gowenrw/psycho_badge/art/Image2LCD_Settings.png

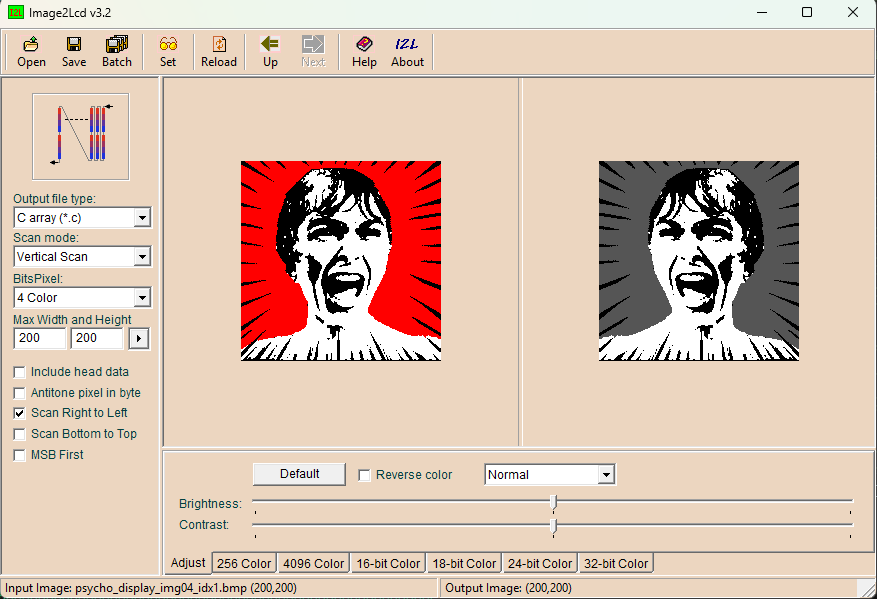
art/Image2LCD_Settings.png
