gowenrw/psycho_badge/art/inspiration/09eceb80-aa4b-47ba-a81a-bc735ab3dbdd.jpg

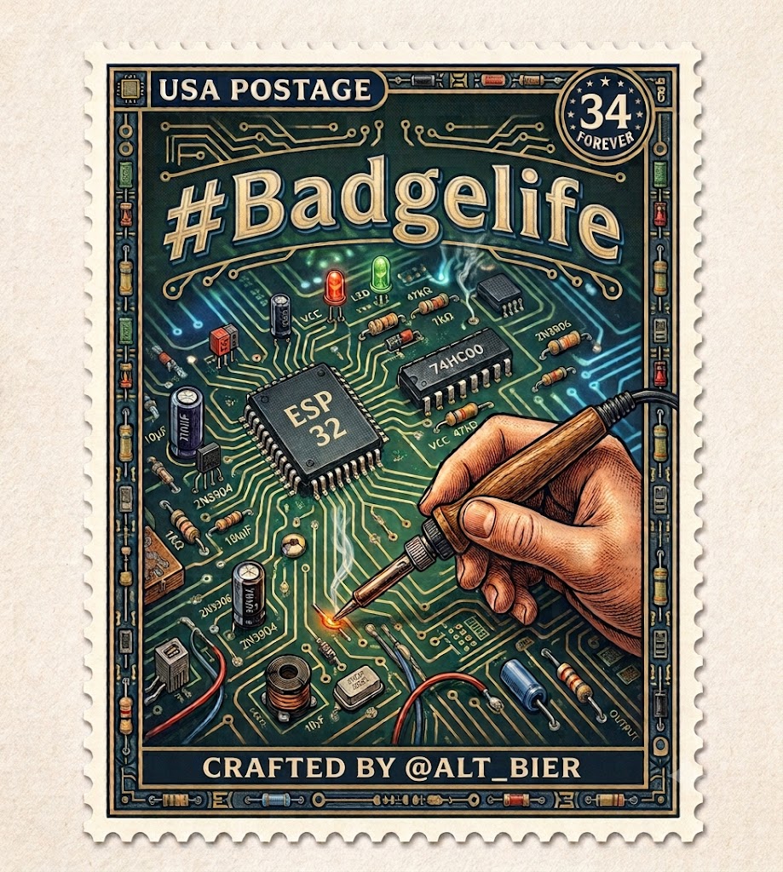
art/inspiration/09eceb80-aa4b-47ba-a81a-bc735ab3dbdd.jpg
