gowenrw/psycho_badge/art/inspiration/51a8uor2yWL._AC_UF894,1000_QL80_.jpg

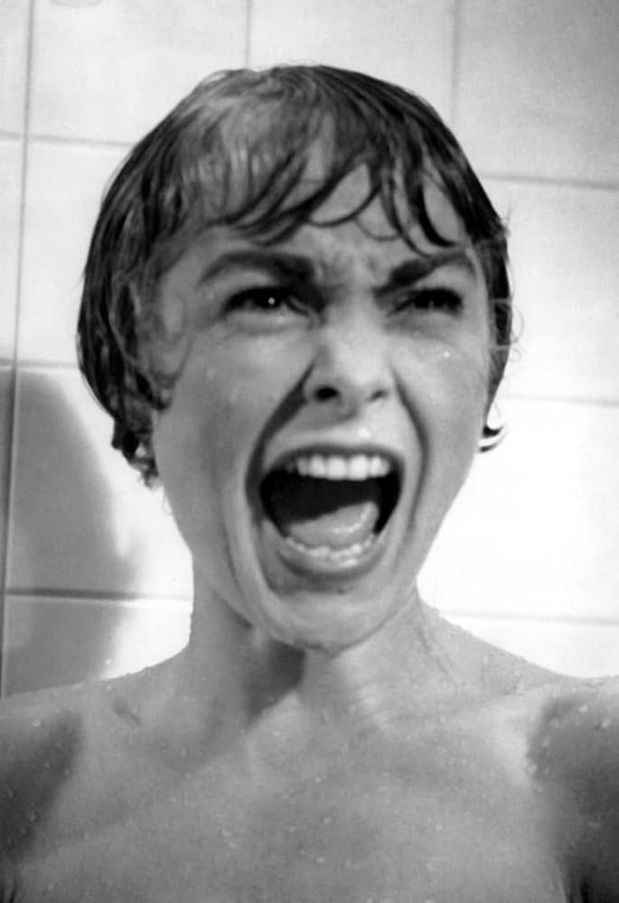
art/inspiration/51a8uor2yWL._AC_UF894,1000_QL80_.jpg
