gowenrw/psycho_badge/art/inspiration/78148790-cfff-4a0e-b91e-01b8ff07a633.jpg

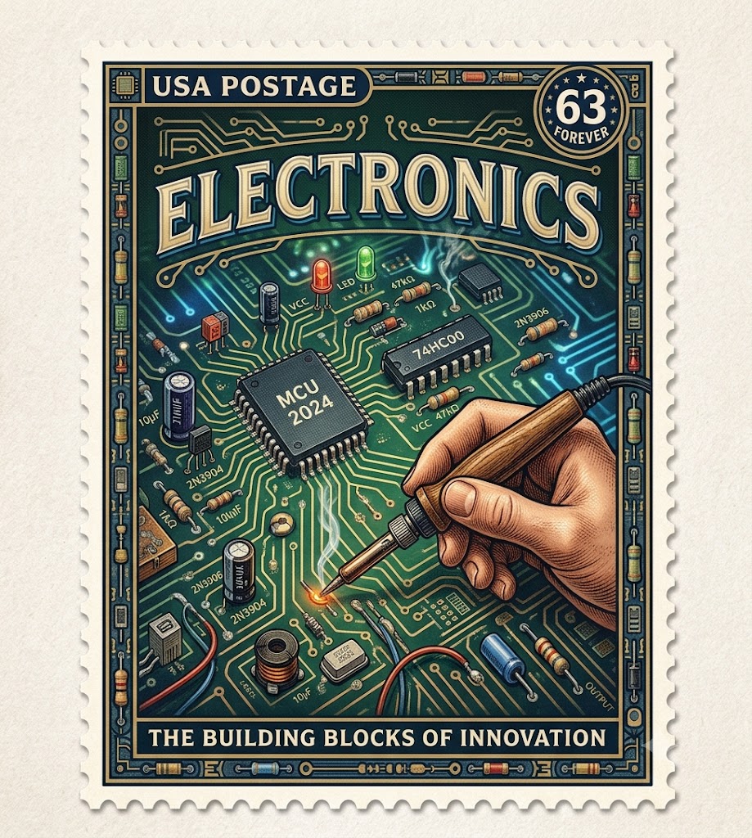
art/inspiration/78148790-cfff-4a0e-b91e-01b8ff07a633.jpg
