gowenrw/psycho_badge/art/inspiration/4122593071_39e41a47dc_c.jpg

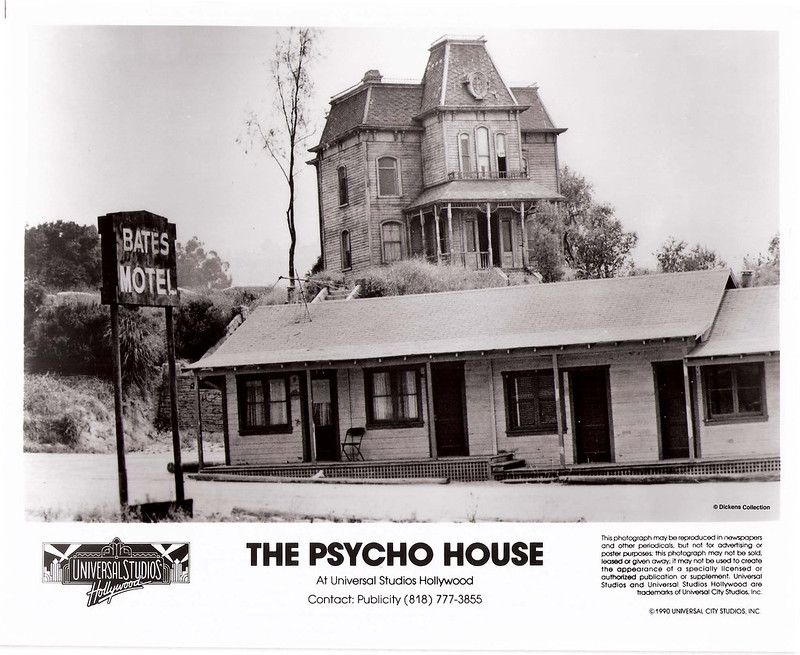
art/inspiration/4122593071_39e41a47dc_c.jpg
