gowenrw/psycho_badge/art/inspiration/5621367626_267cc80568_b.jpg

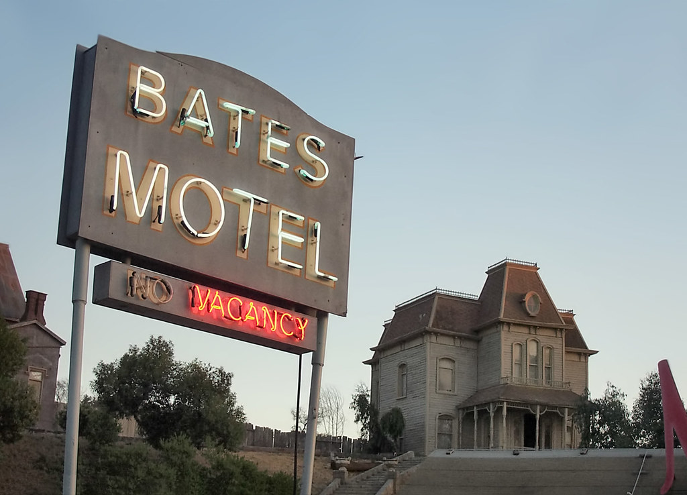
art/inspiration/5621367626_267cc80568_b.jpg
