gowenrw/psycho_badge/art/inspiration/alfred_hitchcock_presents.jpg

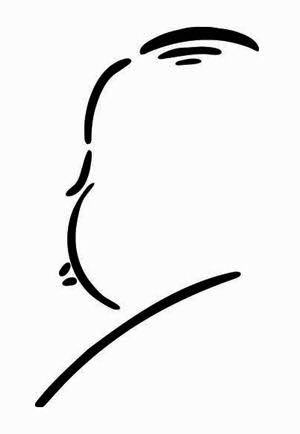
art/inspiration/alfred_hitchcock_presents.jpg
