gowenrw/psycho_badge/art/inspiration/alt_bier_a_small_array_of_antennas_and_satellite_dishes_on_a_ro_00e93679-4413-47bc-a557-2c08350d457e.png

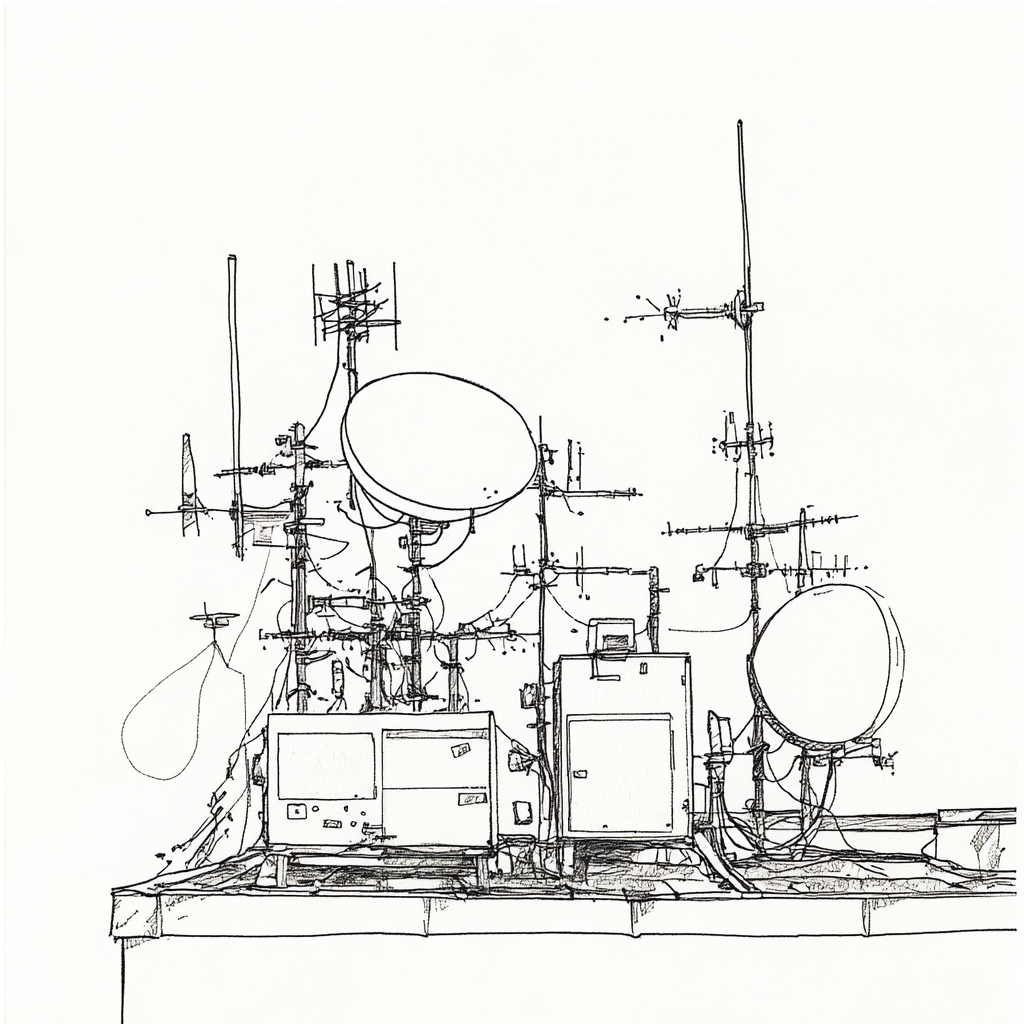
art/inspiration/alt_bier_a_small_array_of_antennas_and_satellite_dishes_on_a_ro_00e93679-4413-47bc-a557-2c08350d457e.png
