gowenrw/psycho_badge/art/inspiration/alt_bier_front_of_a_motel_room_with_a_large_bay_window_and_door_1ff72061-c35d-46a8-9a01-6a3859370cd5.png

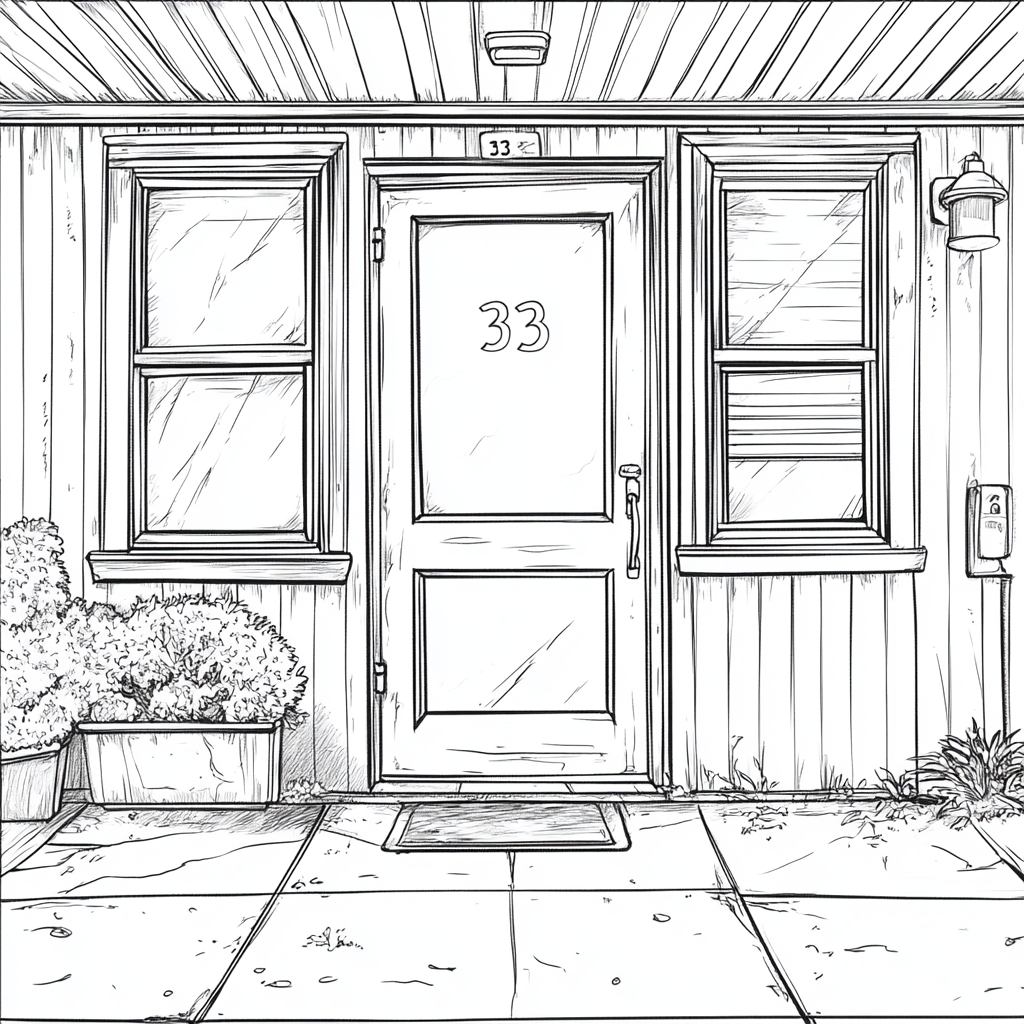
art/inspiration/alt_bier_front_of_a_motel_room_with_a_large_bay_window_and_door_1ff72061-c35d-46a8-9a01-6a3859370cd5.png
