gowenrw/psycho_badge/art/inspiration/alt_bier_front_of_a_motel_room_with_a_large_bay_window_and_door_b3eee03a-e481-4e49-9f6b-45e3d3eed8d4.png

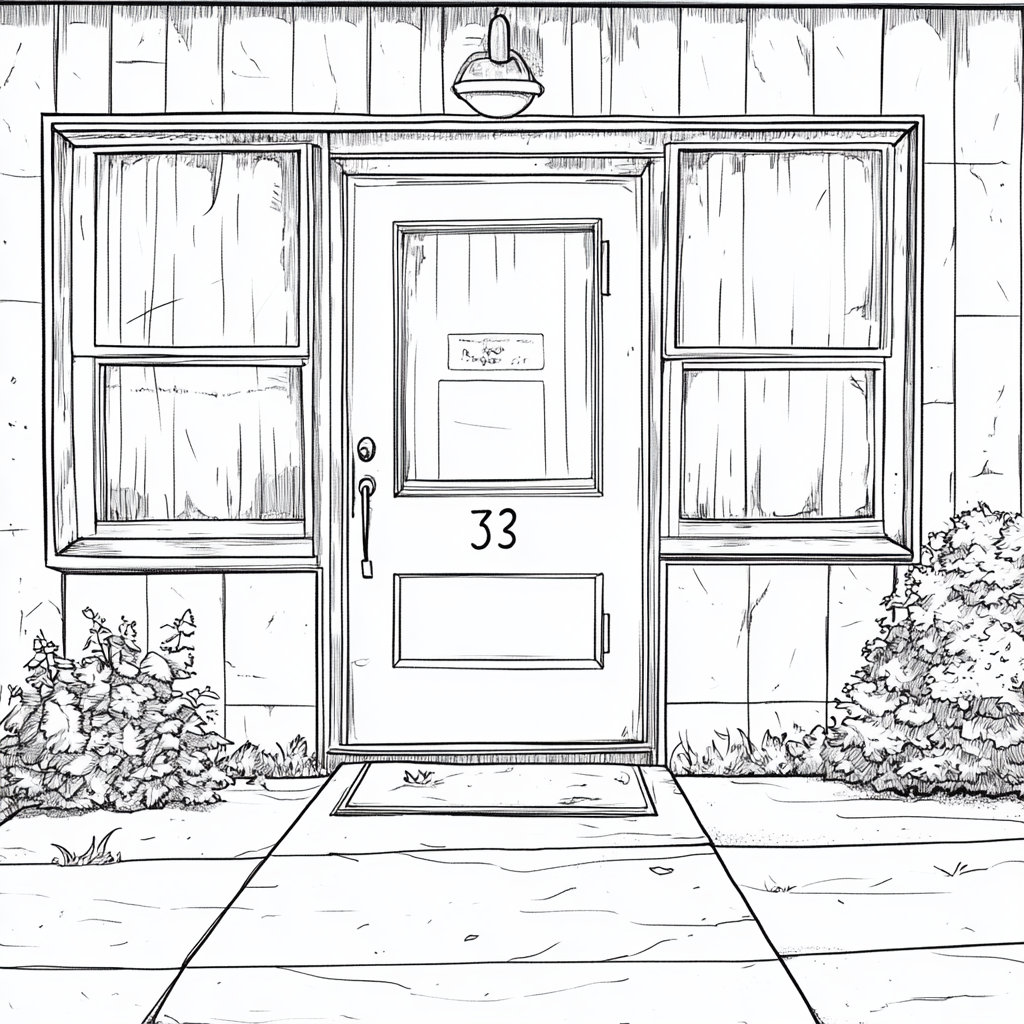
art/inspiration/alt_bier_front_of_a_motel_room_with_a_large_bay_window_and_door_b3eee03a-e481-4e49-9f6b-45e3d3eed8d4.png
