gowenrw/psycho_badge/art/inspiration/alt_bier_image_756xbq756xbq756x.png

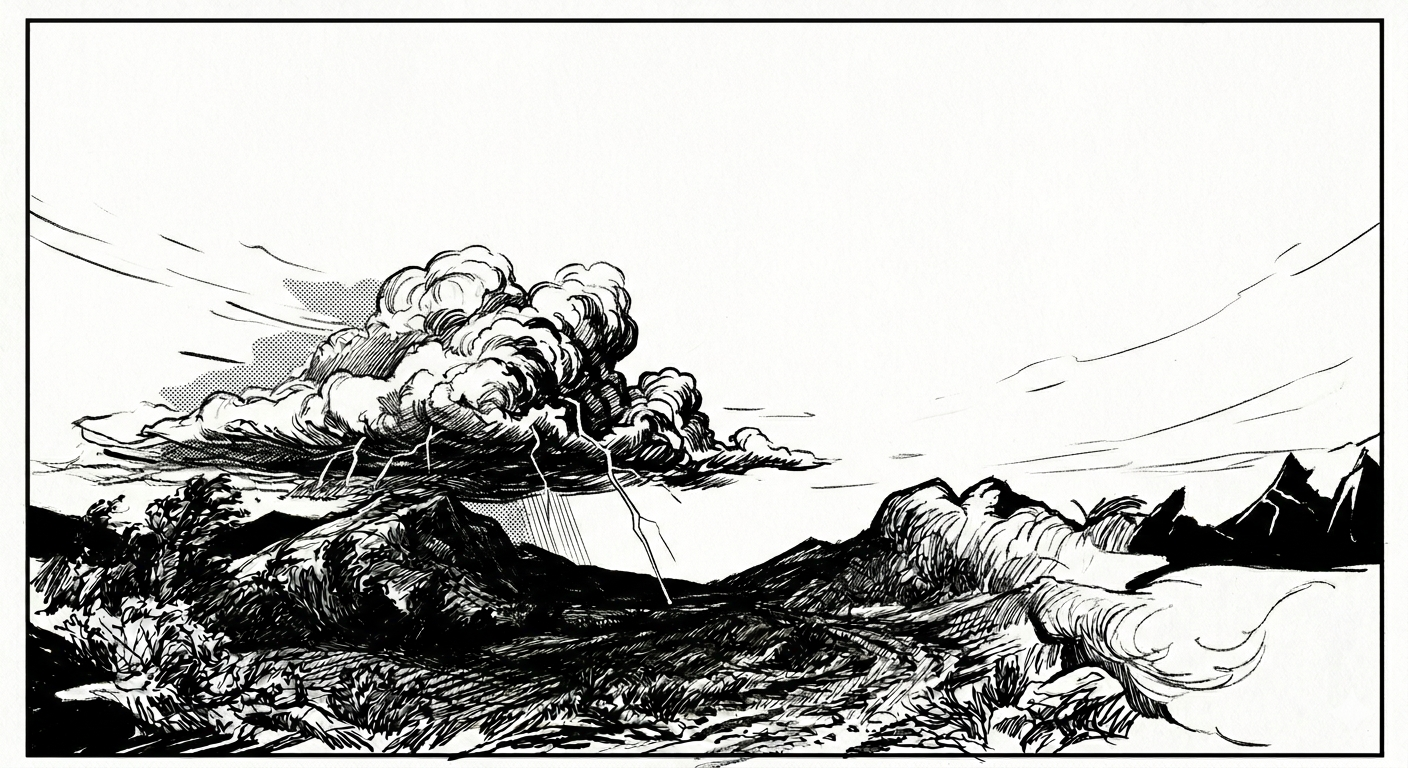
art/inspiration/alt_bier_image_756xbq756xbq756x.png
