gowenrw/psycho_badge/art/inspiration/alt_bier_image_aumj92aumj92aumj.png

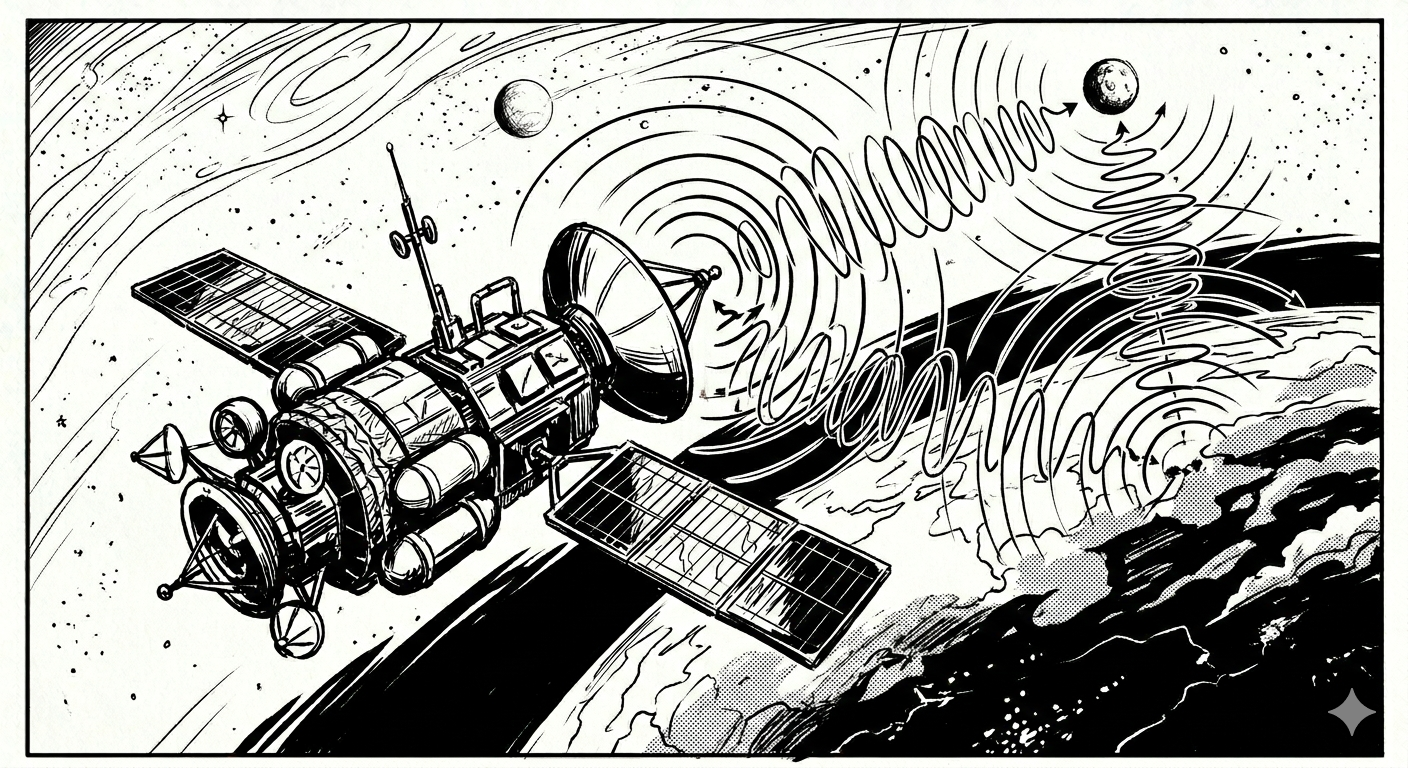
art/inspiration/alt_bier_image_aumj92aumj92aumj.png
