gowenrw/psycho_badge/art/inspiration/alt_bier_image_n5bnvrn5bnvrn5bn.png

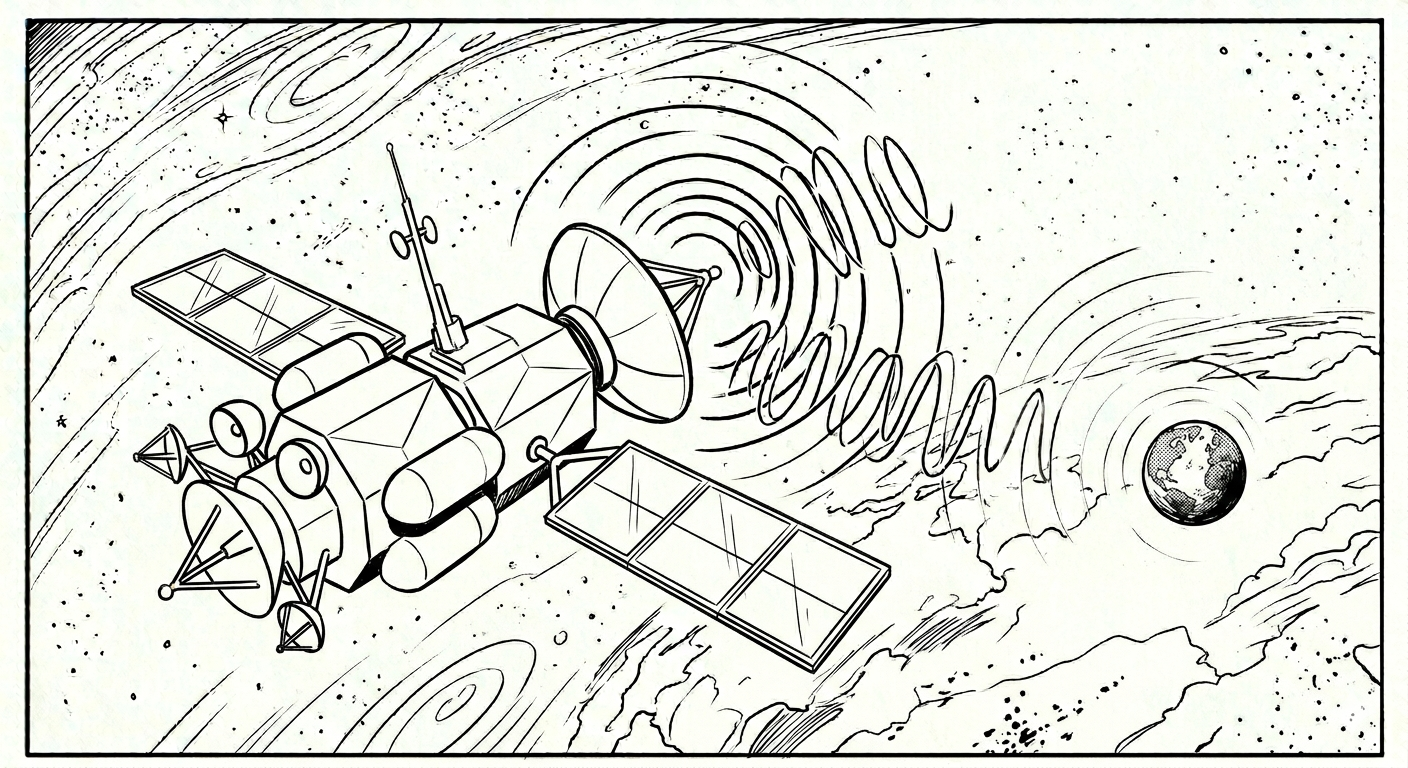
art/inspiration/alt_bier_image_n5bnvrn5bnvrn5bn.png
