gowenrw/psycho_badge/art/inspiration/alt_bier_image_p0ahntp0ahntp0ah.png

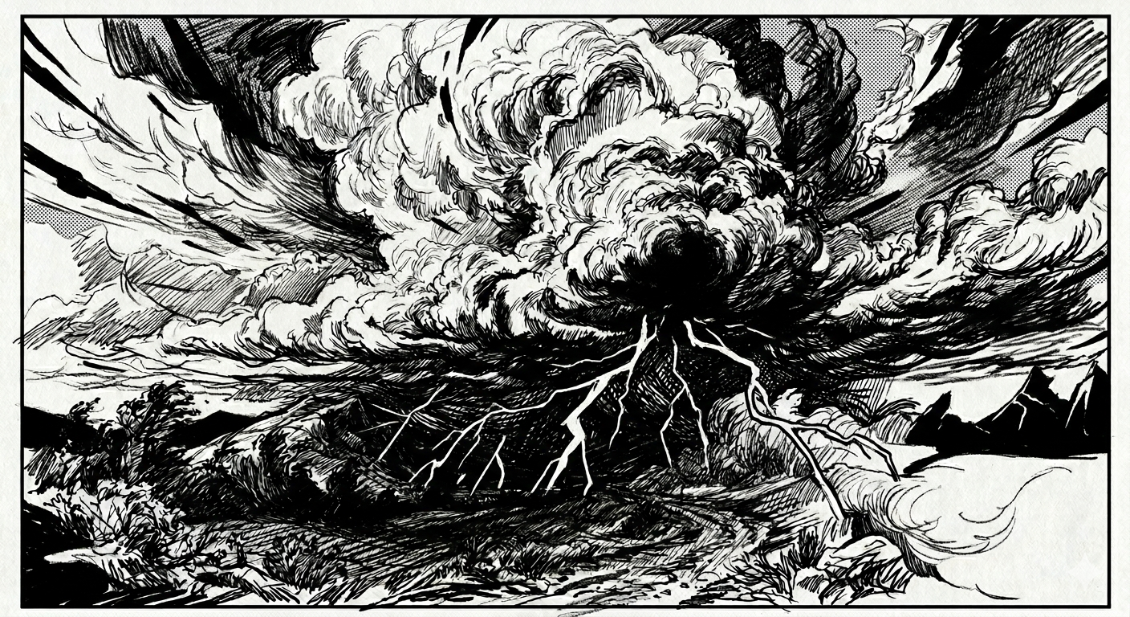
art/inspiration/alt_bier_image_p0ahntp0ahntp0ah.png
