gowenrw/psycho_badge/art/inspiration/alt_bier_image_rigv1rigv1rigv1r.png

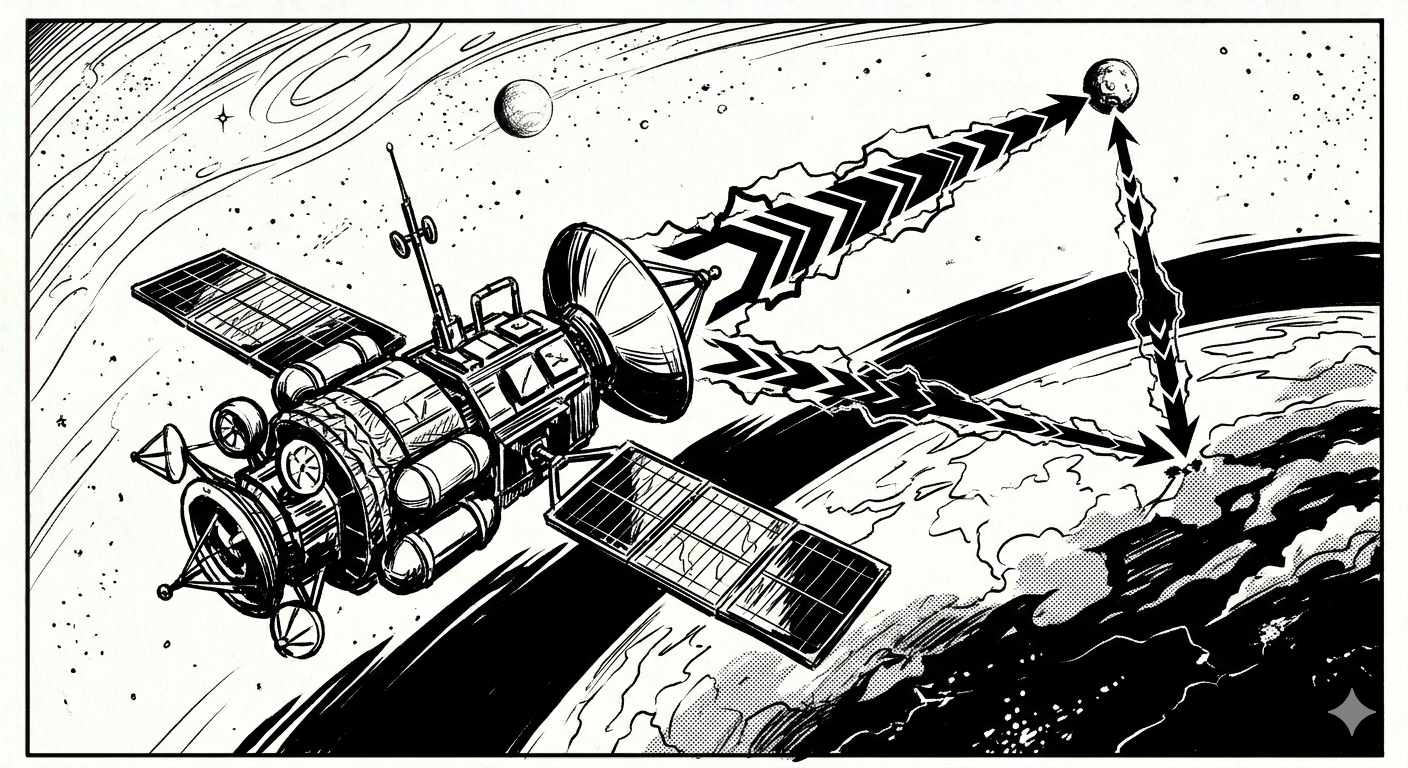
art/inspiration/alt_bier_image_rigv1rigv1rigv1r.png
