gowenrw/psycho_badge/art/inspiration/alt_bier_small_motel_cabin_line_art_in_the_style_of_coloring_bo_fb256de8-bc3b-488d-bda0-6eb76a03a0a5.png

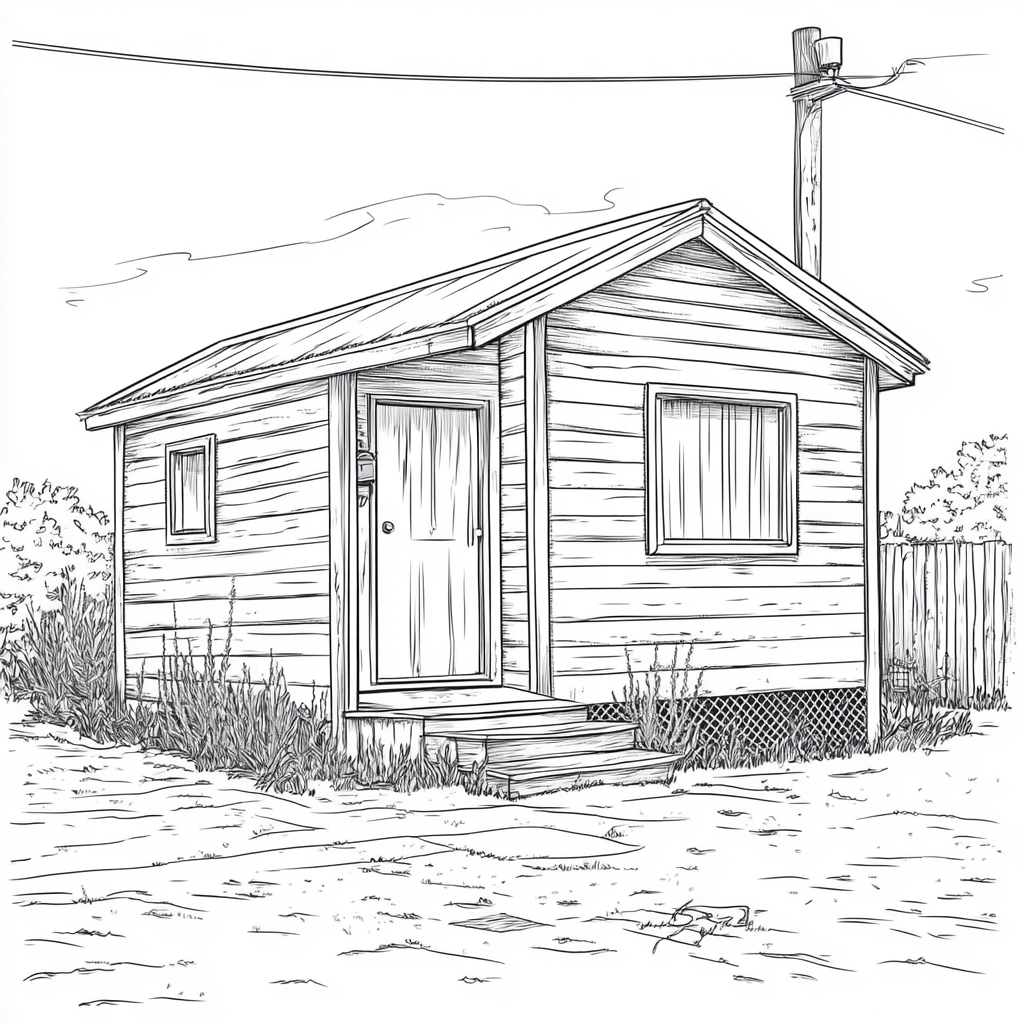
art/inspiration/alt_bier_small_motel_cabin_line_art_in_the_style_of_coloring_bo_fb256de8-bc3b-488d-bda0-6eb76a03a0a5.png
