gowenrw/psycho_badge/art/inspiration/b29aaca8-62c0-4f67-92ab-7d956eef123c.jpg

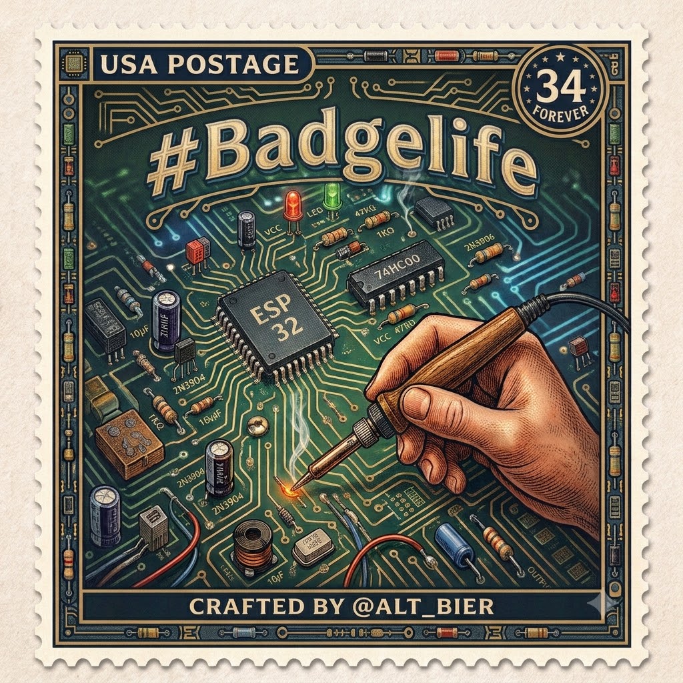
art/inspiration/b29aaca8-62c0-4f67-92ab-7d956eef123c.jpg
