gowenrw/psycho_badge/art/inspiration/Bates-Motel-House-Psycho-1960.jpg

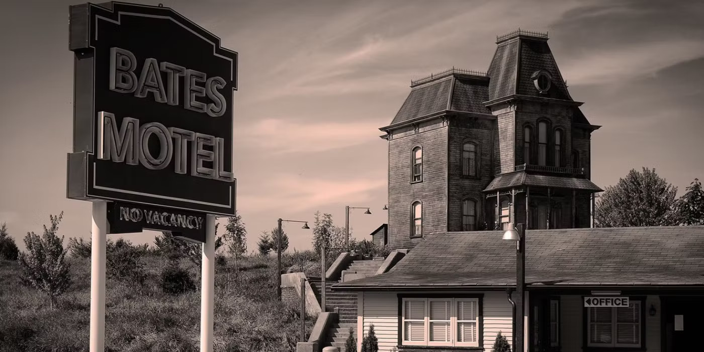
art/inspiration/Bates-Motel-House-Psycho-1960.jpg
