gowenrw/psycho_badge/art/inspiration/cb8425abfd5140c085e9a8f64b2272b4.jpg

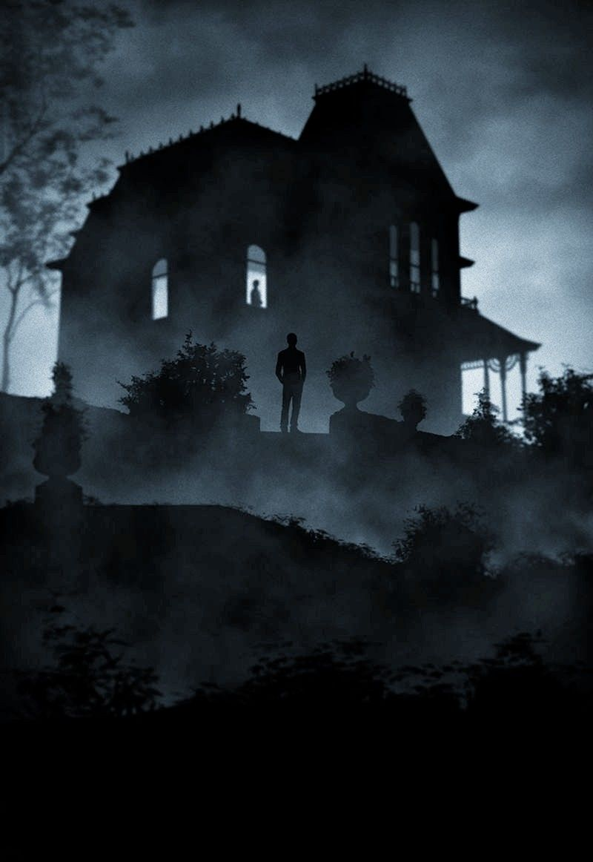
art/inspiration/cb8425abfd5140c085e9a8f64b2272b4.jpg
