gowenrw/psycho_badge/art/inspiration/il_570xN.5547620067_drzp.jpg

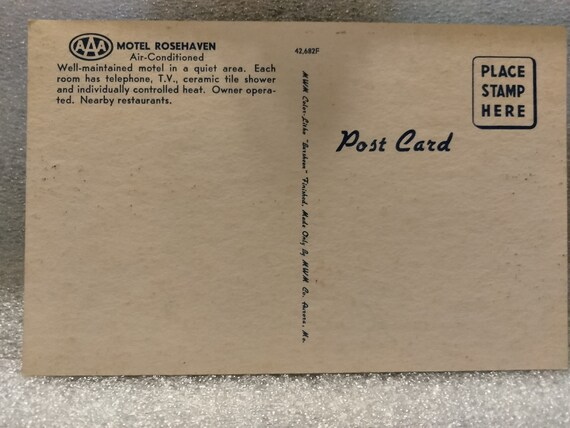
art/inspiration/il_570xN.5547620067_drzp.jpg
