gowenrw/psycho_badge/art/inspiration/il_fullxfull.896021947_tdyu.webp

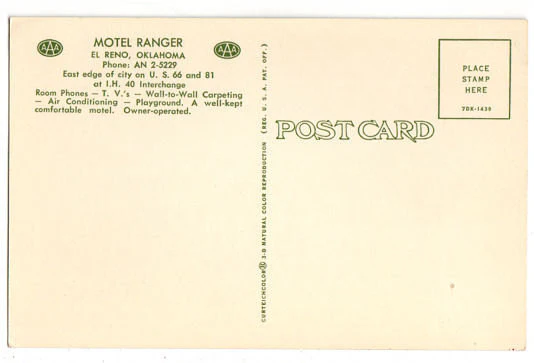
art/inspiration/il_fullxfull.896021947_tdyu.webp
