gowenrw/psycho_badge/art/inspiration/image_9cf47526.png

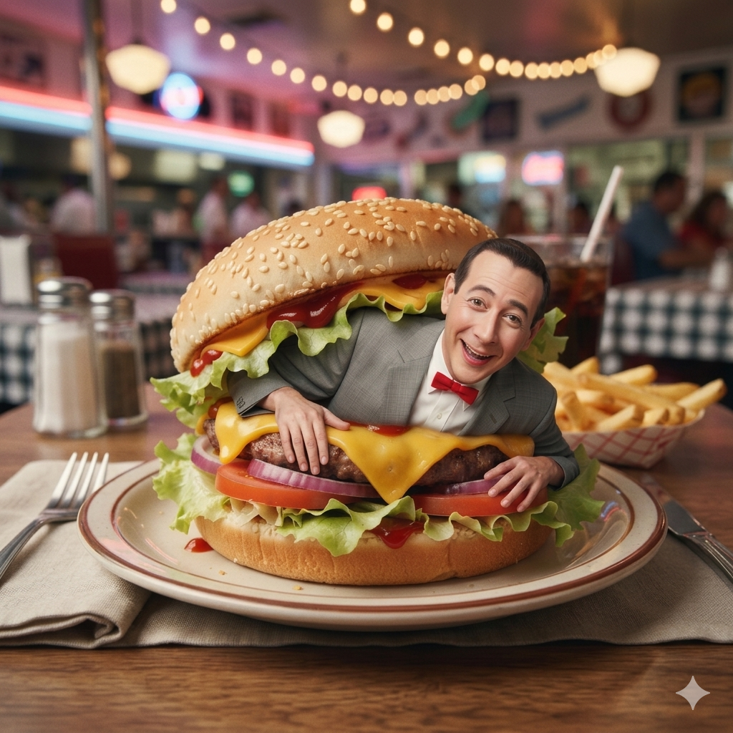
art/inspiration/image_9cf47526.png
