gowenrw/psycho_badge/art/inspiration/images.jpg

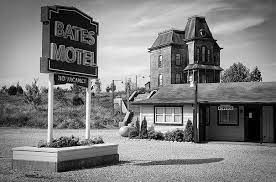
art/inspiration/images.jpg
