gowenrw/psycho_badge/art/inspiration/img_1089.webp

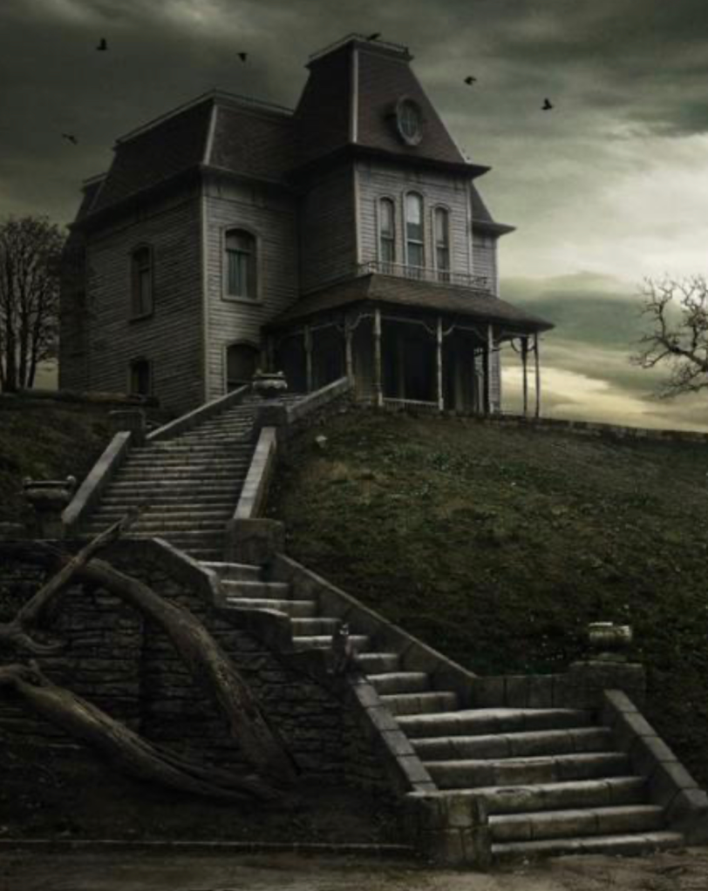
art/inspiration/img_1089.webp
