gowenrw/psycho_badge/art/inspiration/mother_image_1.jpg

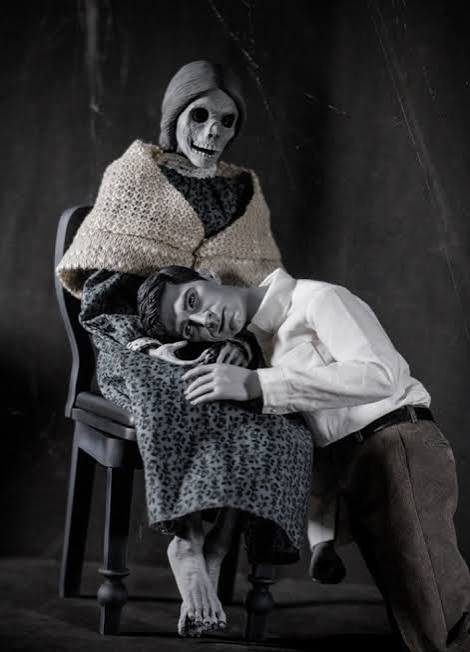
art/inspiration/mother_image_1.jpg
