gowenrw/psycho_badge/art/inspiration/mother_image_2.jpg

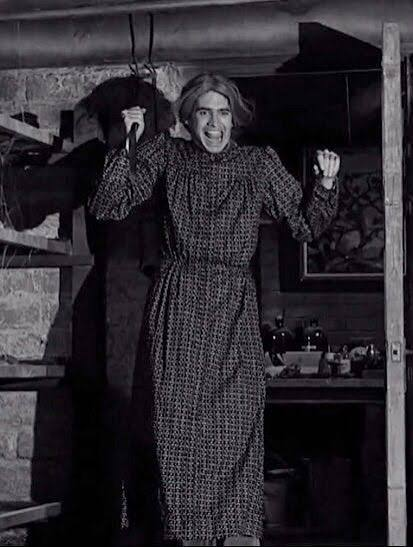
art/inspiration/mother_image_2.jpg
