gowenrw/psycho_badge/art/inspiration/norman_image_1.jpg

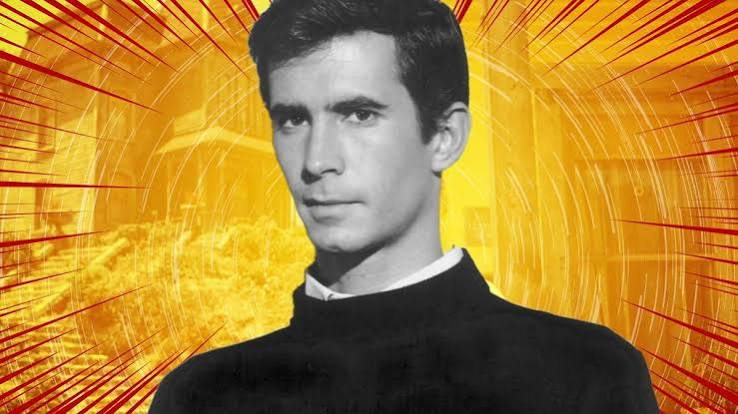
art/inspiration/norman_image_1.jpg
