gowenrw/psycho_badge/art/inspiration/peewee_burger2.png

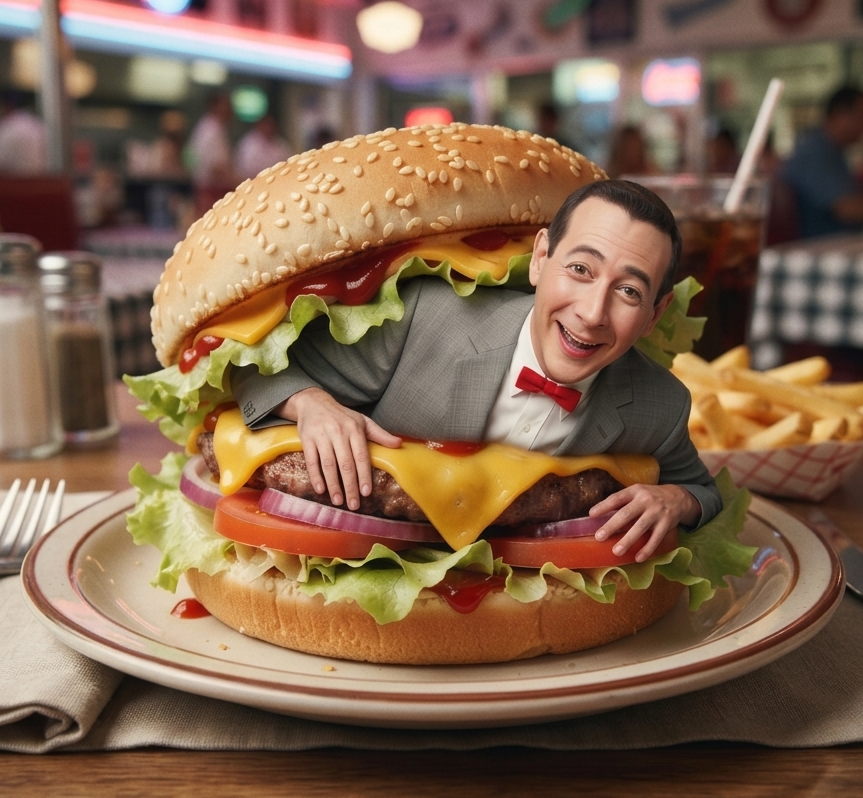
art/inspiration/peewee_burger2.png
