gowenrw/psycho_badge/art/inspiration/peewee_burger.png

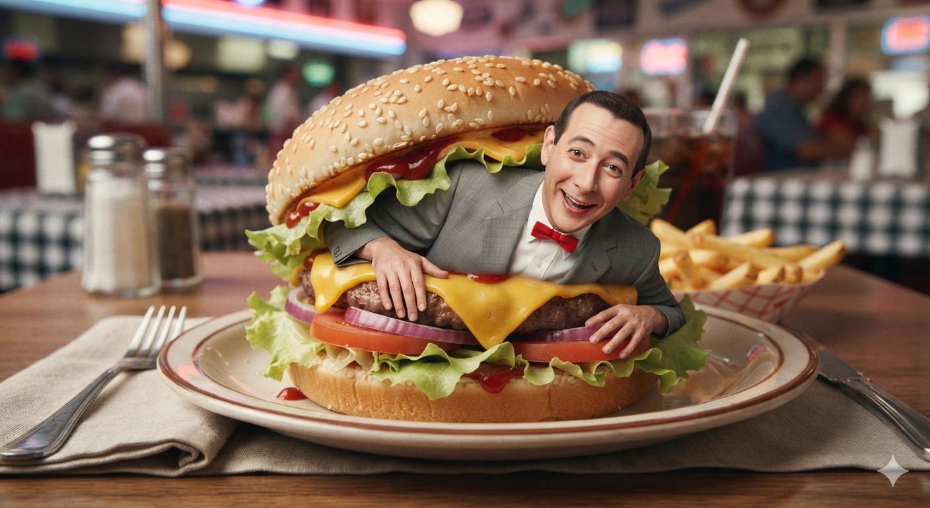
art/inspiration/peewee_burger.png
