gowenrw/psycho_badge/art/inspiration/psycho-bates-motel-alfred-hitchcock-craig-roberts.jpg

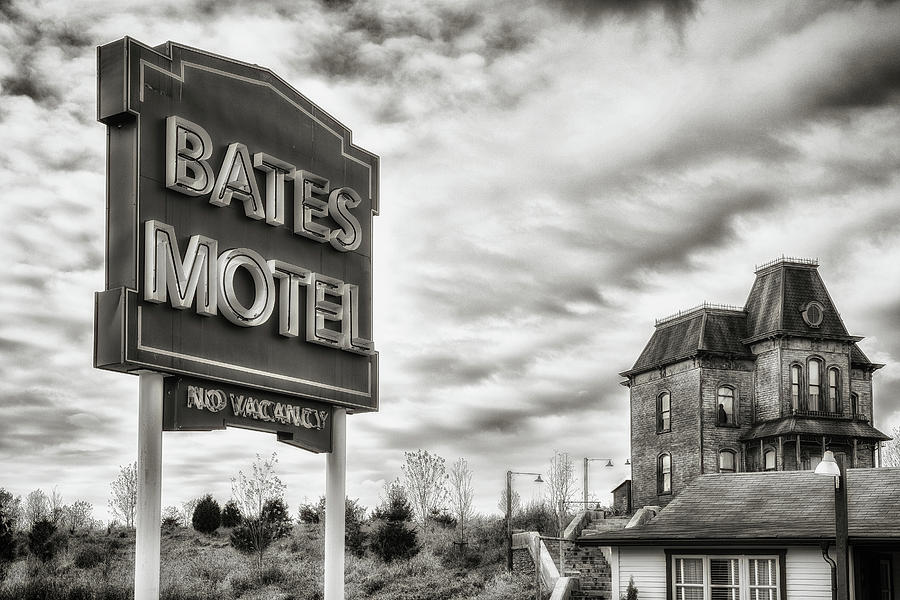
art/inspiration/psycho-bates-motel-alfred-hitchcock-craig-roberts.jpg
