gowenrw/psycho_badge/art/inspiration/psycho-pic-1.jpg

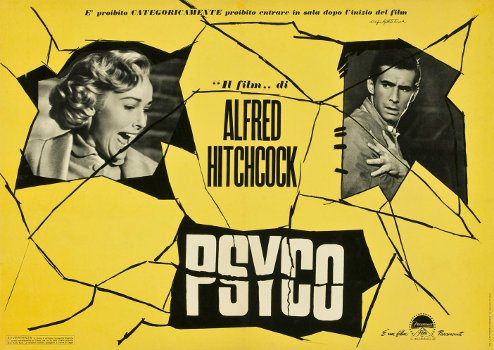
art/inspiration/psycho-pic-1.jpg
