gowenrw/psycho_badge/art/inspiration/psycho-pic-2.jpg

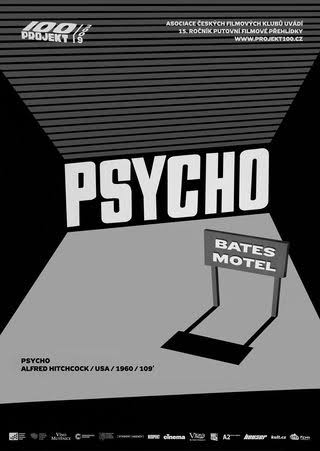
art/inspiration/psycho-pic-2.jpg
