gowenrw/psycho_badge/art/inspiration/psycho-pic-3.jpg

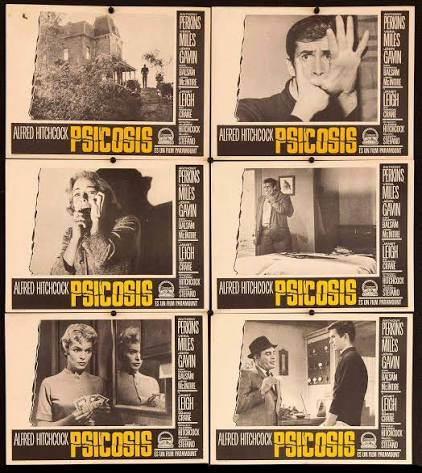
art/inspiration/psycho-pic-3.jpg
