gowenrw/psycho_badge/art/inspiration/psycho-pic-4.jpg

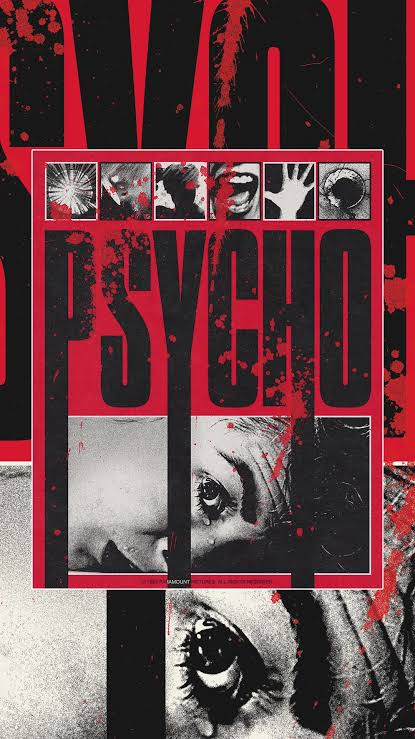
art/inspiration/psycho-pic-4.jpg
