gowenrw/psycho_badge/art/inspiration/psycho_car_swamp.jpg

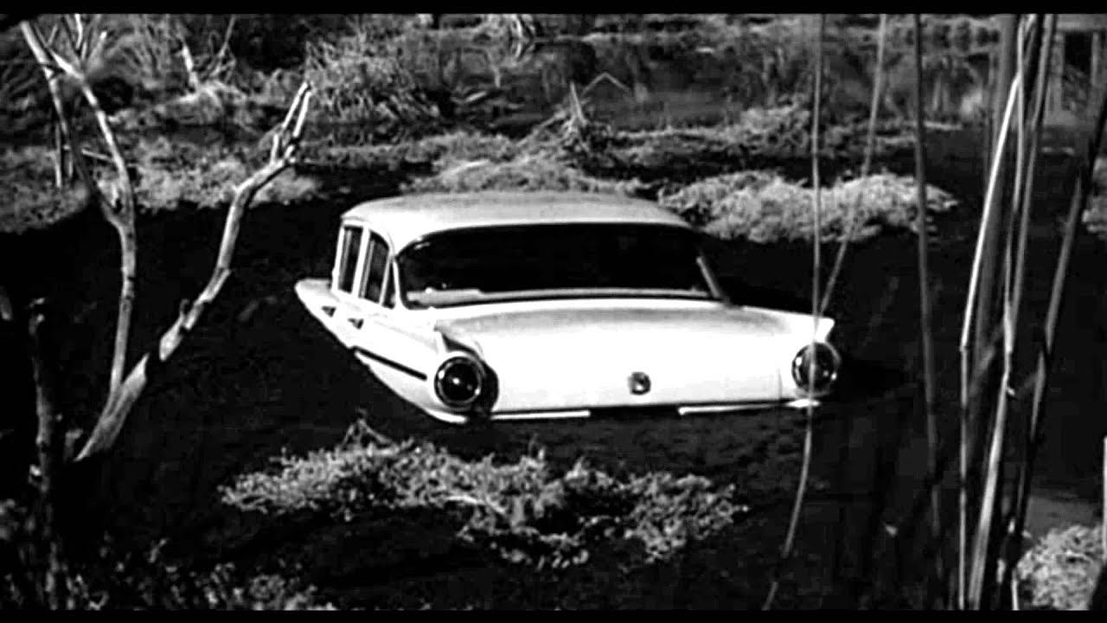
art/inspiration/psycho_car_swamp.jpg
