gowenrw/psycho_badge/art/inspiration/PsychoLC5A.jpg

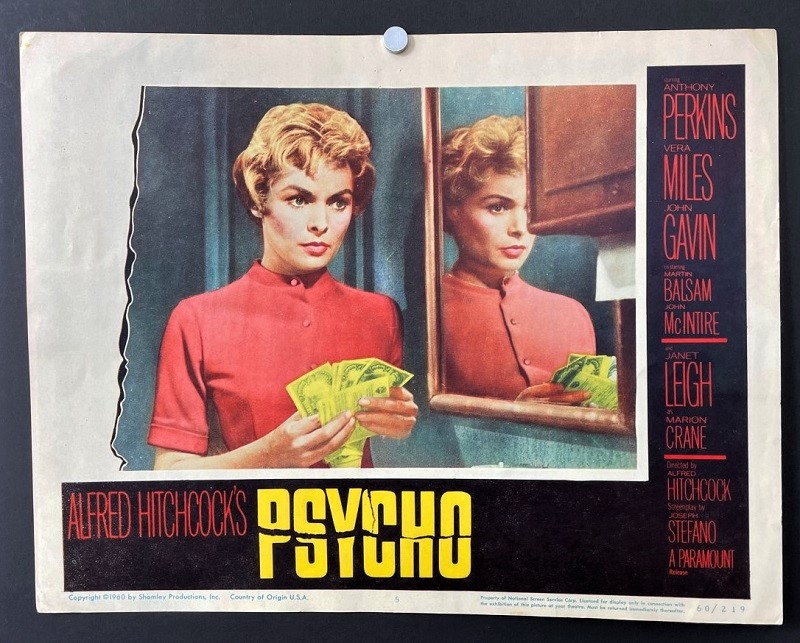
art/inspiration/PsychoLC5A.jpg
