gowenrw/psycho_badge/art/inspiration/PsychoLC5A_3.jpg

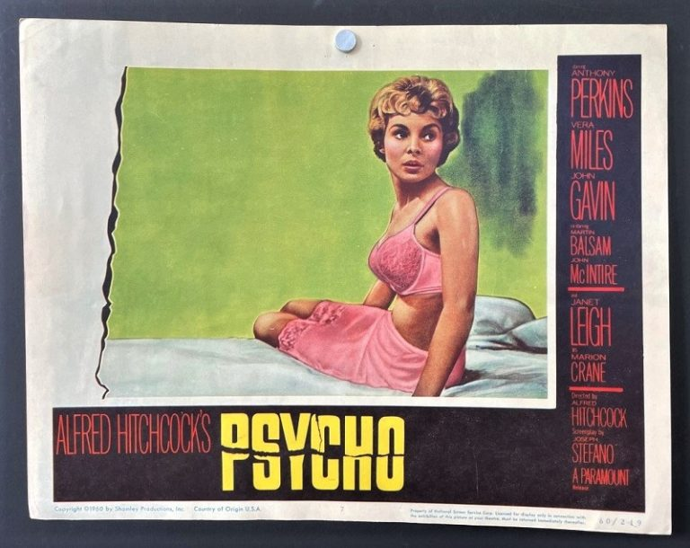
art/inspiration/PsychoLC5A_3.jpg
