gowenrw/psycho_badge/art/inspiration/reaching_image_1.jpg

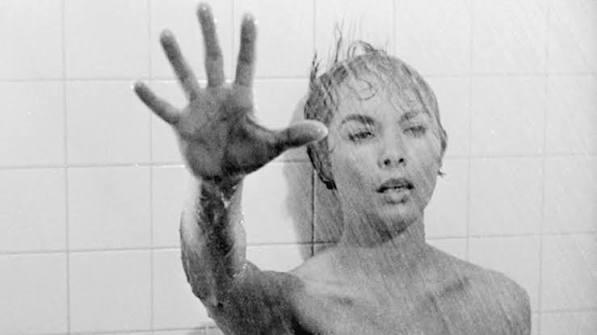
art/inspiration/reaching_image_1.jpg
