gowenrw/psycho_badge/art/inspiration/s-l400.jpg

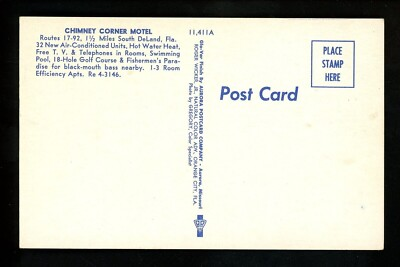
art/inspiration/s-l400.jpg
