gowenrw/psycho_badge/art/inspiration/s-l1200.jpg

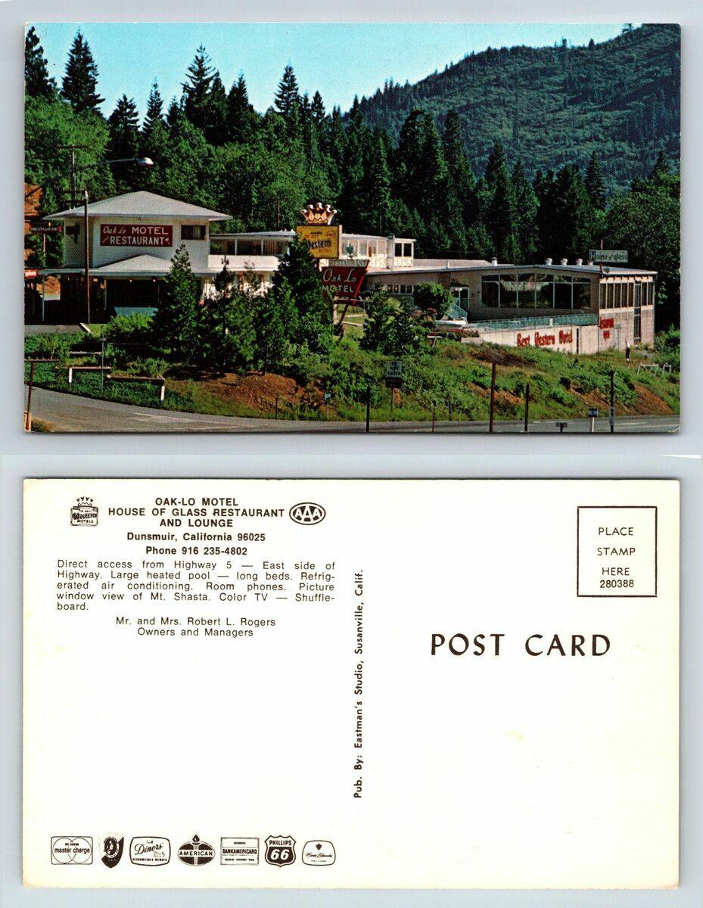
art/inspiration/s-l1200.jpg
