gowenrw/psycho_badge/art/inspiration/s-l1200.png

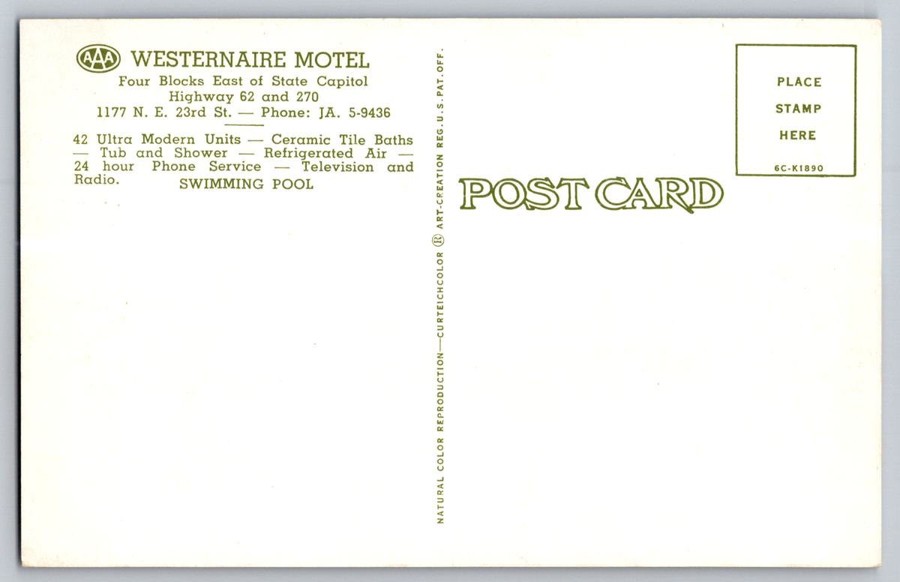
art/inspiration/s-l1200.png
