gowenrw/psycho_badge/art/inspiration/s-l1200_1.jpg

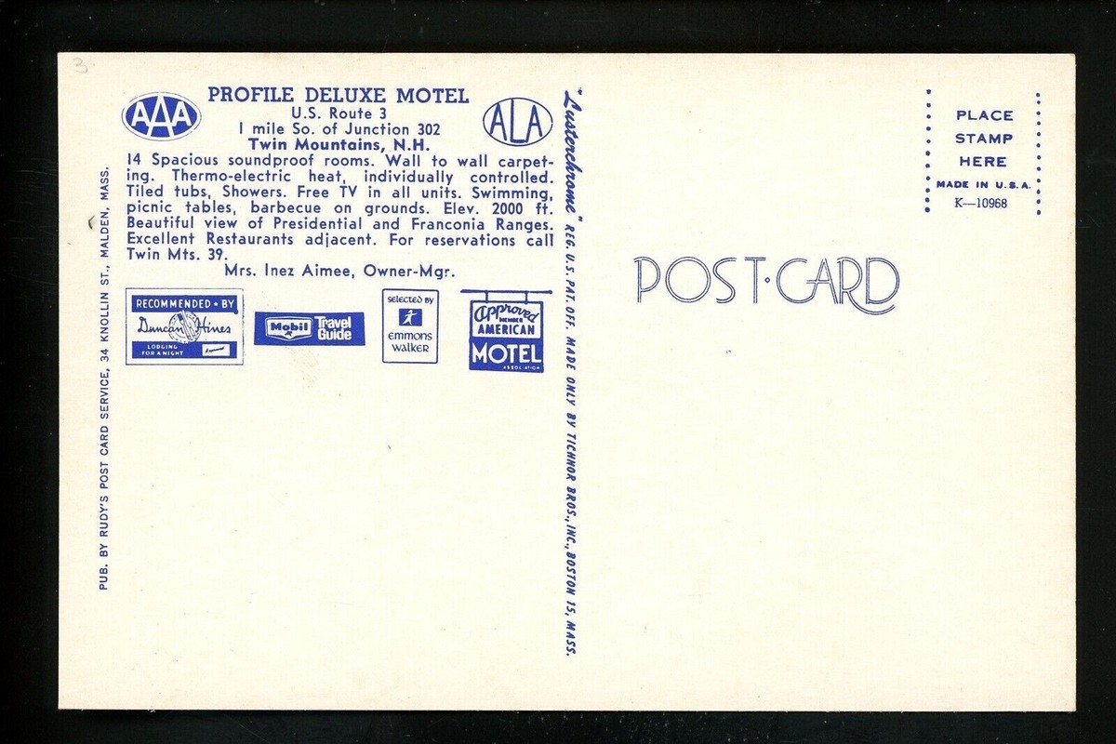
art/inspiration/s-l1200_1.jpg
