gowenrw/psycho_badge/art/inspiration/scream_images_1.jpg

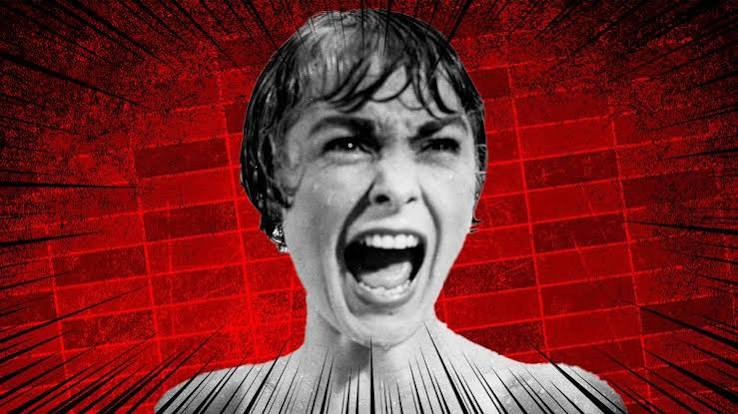
art/inspiration/scream_images_1.jpg
