gowenrw/psycho_badge/art/inspiration/Screenshot 2026-07-10 091231.png

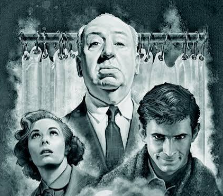
art/inspiration/Screenshot 2026-07-10 091231.png
