gowenrw/psycho_badge/art/inspiration/Screenshot 2026-07-10 091304.png

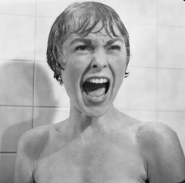
art/inspiration/Screenshot 2026-07-10 091304.png
