gowenrw/psycho_badge/art/inspiration/Screenshot 2026-07-10 091631.png

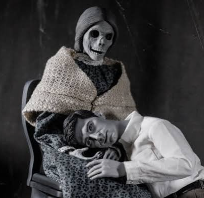
art/inspiration/Screenshot 2026-07-10 091631.png
