gowenrw/psycho_badge/art/inspiration/Screenshot 2026-07-10 092219.png

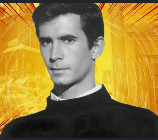
art/inspiration/Screenshot 2026-07-10 092219.png
