gowenrw/psycho_badge/art/inspiration/stabbing_image_1.jpg

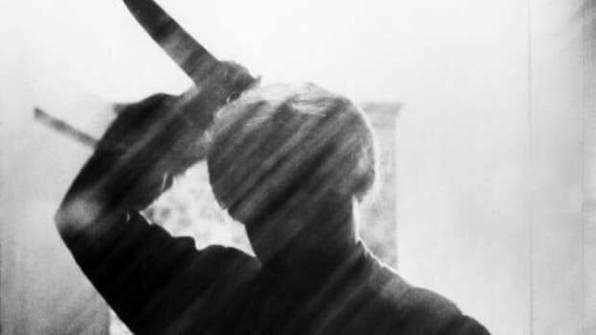
art/inspiration/stabbing_image_1.jpg
