gowenrw/psycho_badge/art/inspiration/thumb1-640x360.jpg

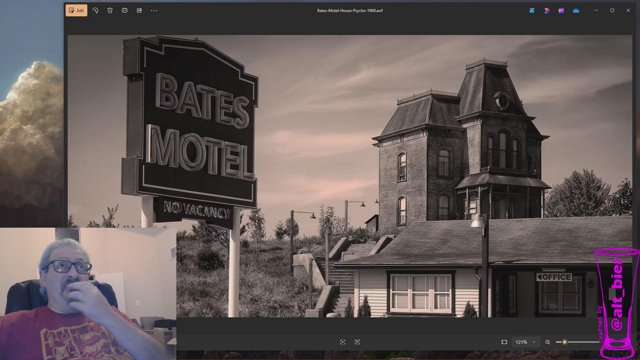
art/inspiration/thumb1-640x360.jpg
