gowenrw/psycho_badge/art/inspiration/tumblr_nlfos3hwl71qgivo1o1_1280.jpg

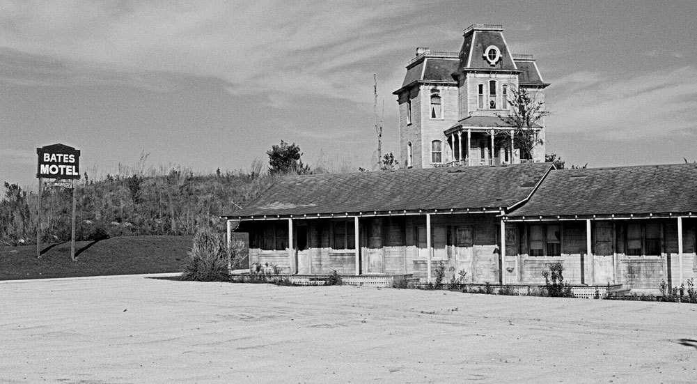
art/inspiration/tumblr_nlfos3hwl71qgivo1o1_1280.jpg
