gowenrw/psycho_badge/art/inspiration/univ_psycho_house_mid_1970s_bison.jpg

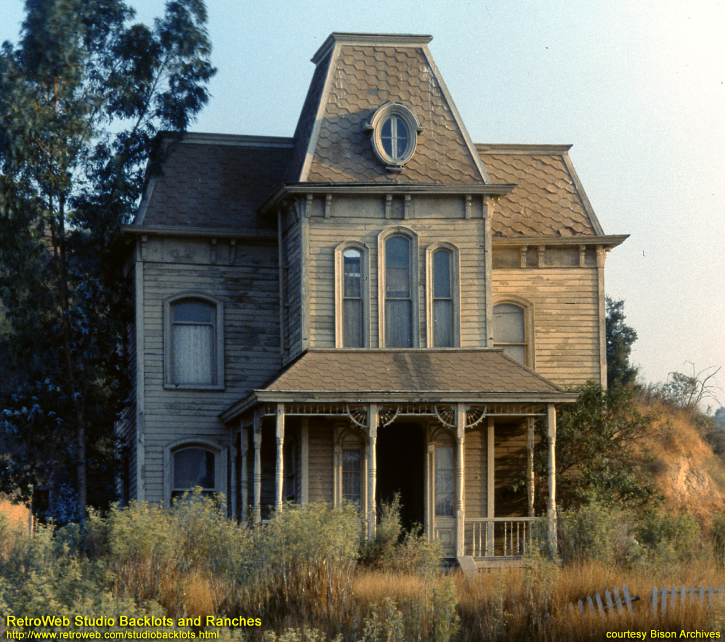
art/inspiration/univ_psycho_house_mid_1970s_bison.jpg
