gowenrw/psycho_badge/art/psycho_display_img02.jpg

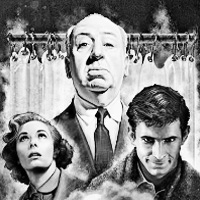
art/psycho_display_img02.jpg
