gowenrw/psycho_badge/art/psycho_display_img03.jpg

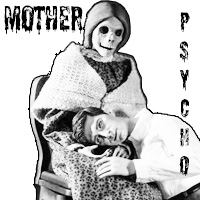
art/psycho_display_img03.jpg
