gowenrw/psycho_badge/art/psycho_display_img04.jpg

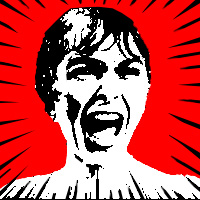
art/psycho_display_img04.jpg
