gowenrw/psycho_badge/art/psycho_display_img05.jpg

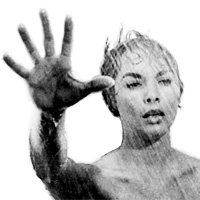
art/psycho_display_img05.jpg
