gowenrw/psycho_badge/art/psycho_display_img06.jpg

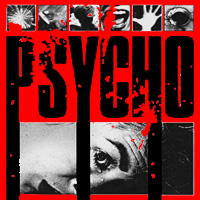
art/psycho_display_img06.jpg
