gowenrw/psycho_badge/art/psycho_display_img07.jpg

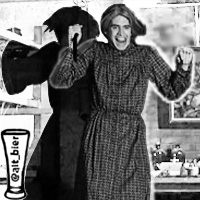
art/psycho_display_img07.jpg
