gowenrw/psycho_badge/art/SandB_silhouette-1.png

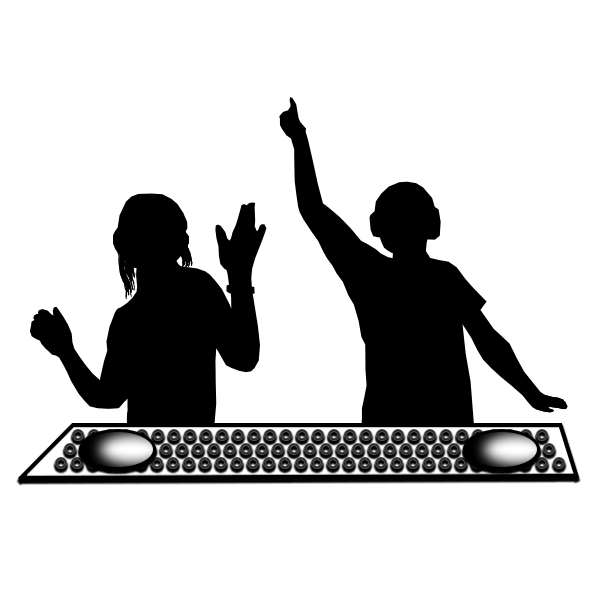
art/SandB_silhouette-1.png
