gowenrw/psycho_badge/art/SB_Hype_Train-1.png

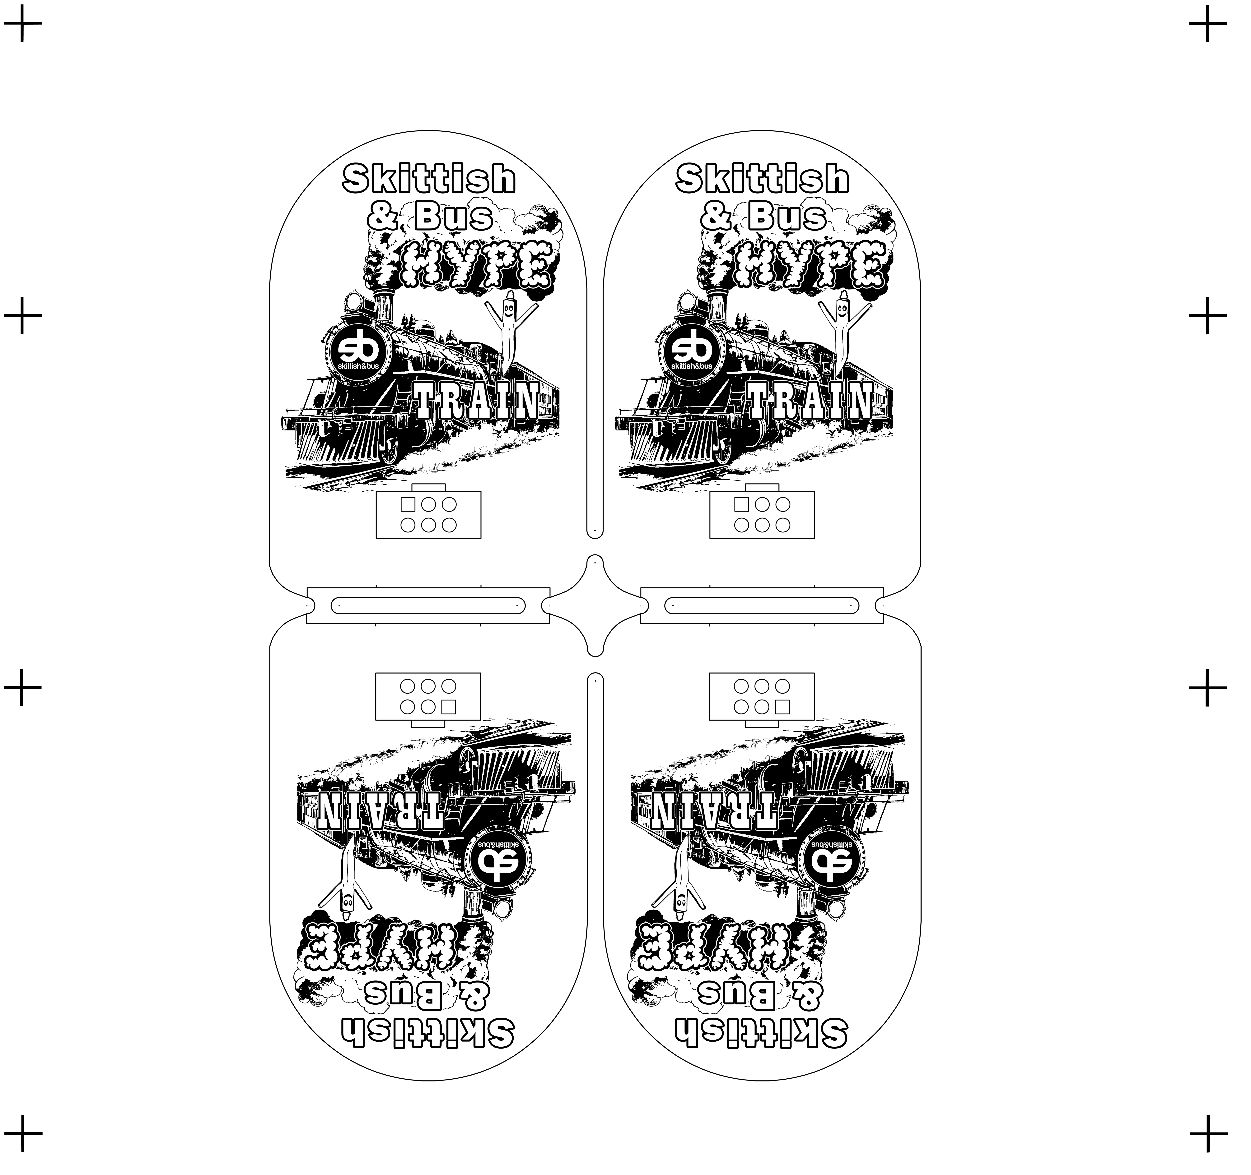
art/SB_Hype_Train-1.png
