gowenrw/psycho_badge/art/SB_Hype_Train-1_F_Mask.png

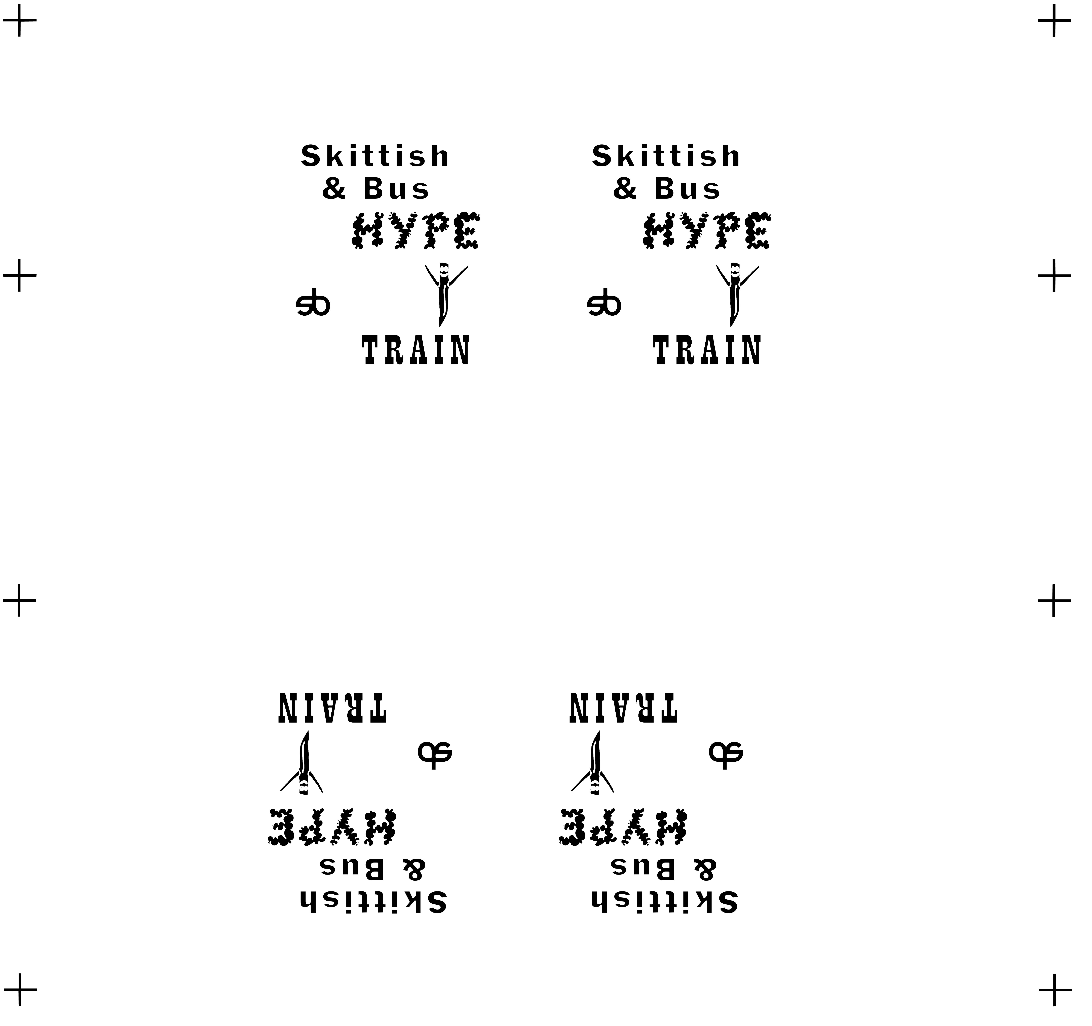
art/SB_Hype_Train-1_F_Mask.png
