gowenrw/psycho_badge/art/SB_Hype_Train-1_F_Silk.png

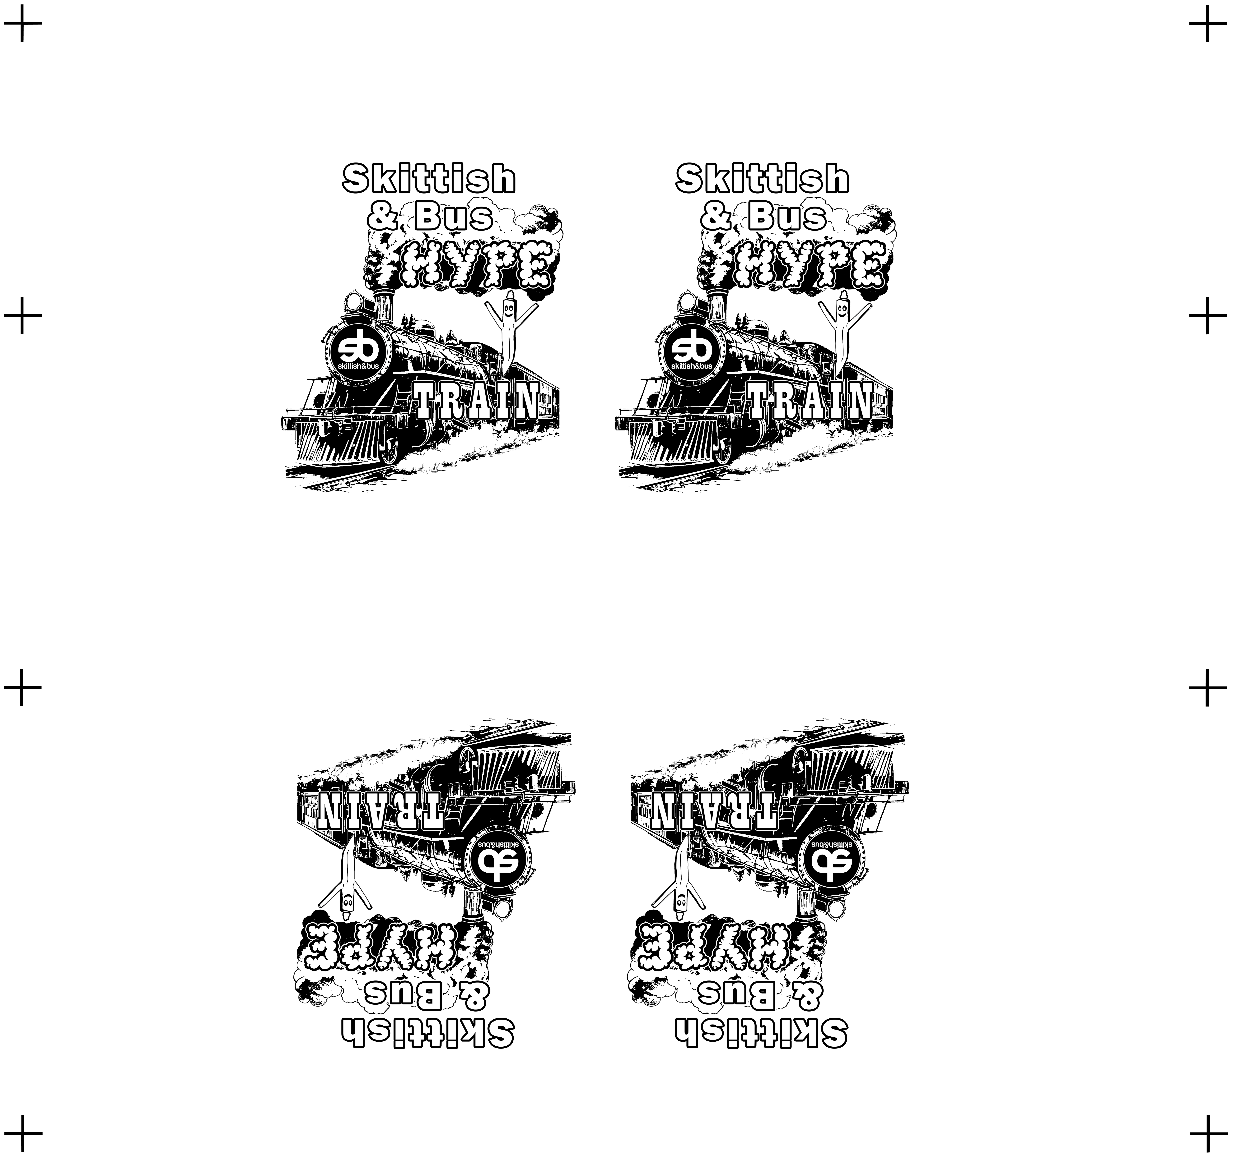
art/SB_Hype_Train-1_F_Silk.png
