gowenrw/psycho_badge/art/Scream_Face_.png

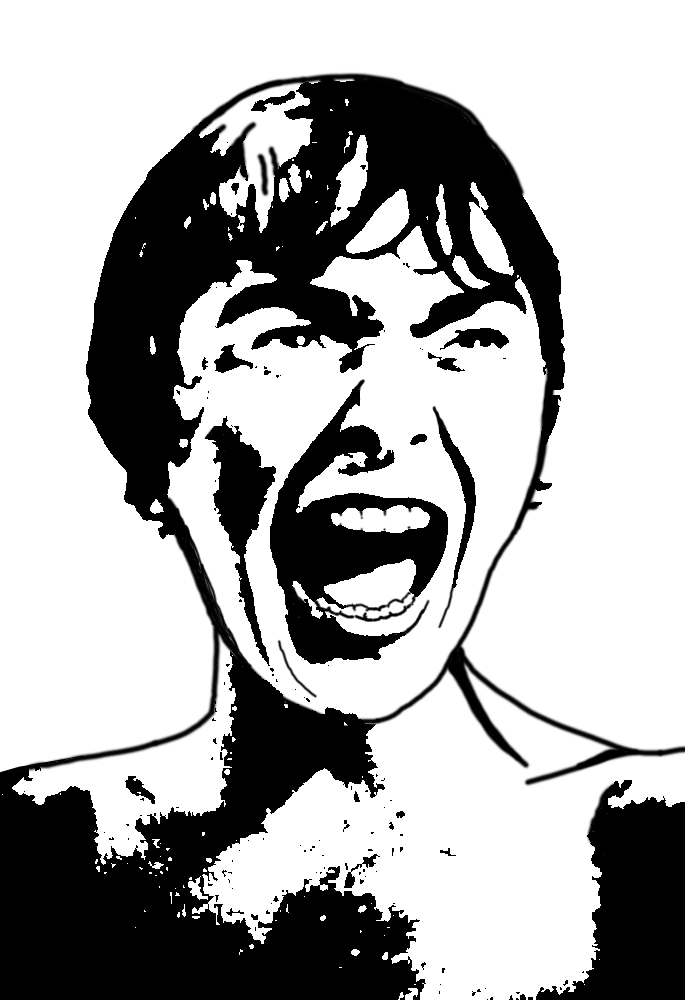
art/Scream_Face_.png
