gowenrw/psycho_badge/art/Scream_Face_SAO_B_Mask.png

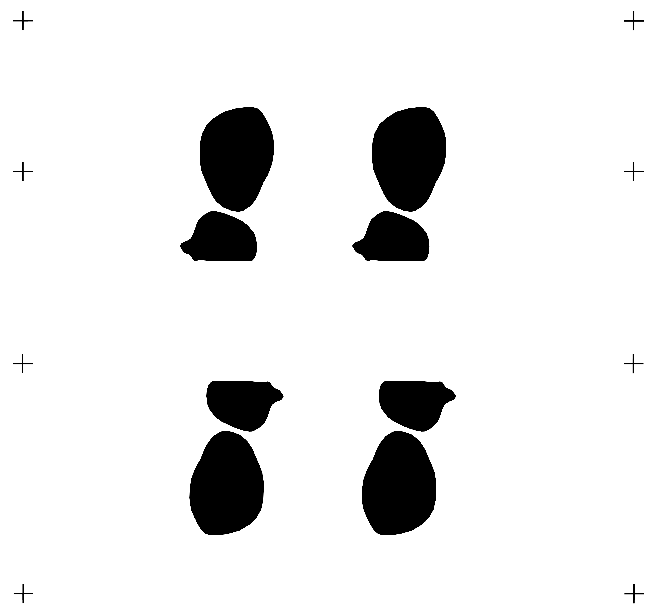
art/Scream_Face_SAO_B_Mask.png
