gowenrw/psycho_badge/art/Scream_Face_SAO_F_Cu.png

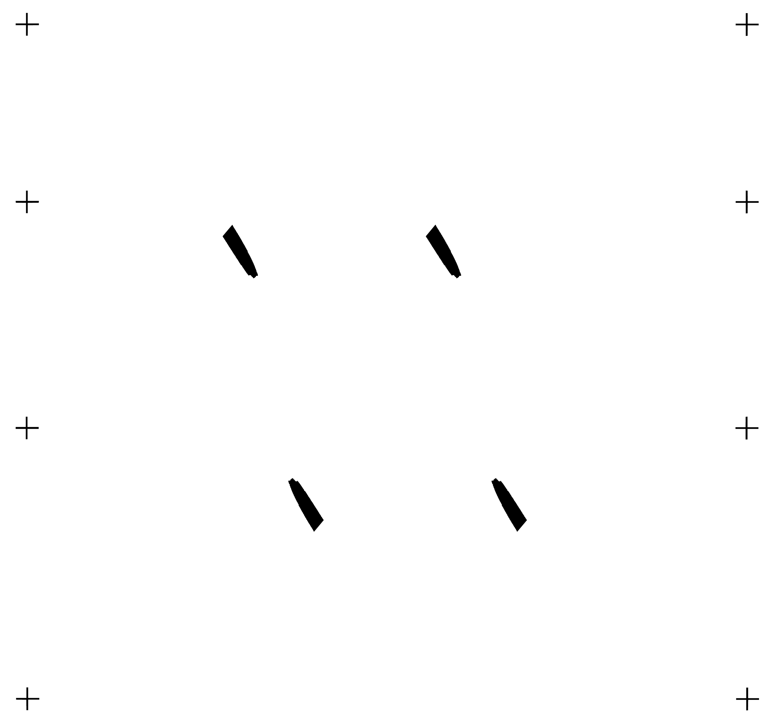
art/Scream_Face_SAO_F_Cu.png
