gowenrw/psycho_badge/art/Scream_Face_SAO_F_Silk.png

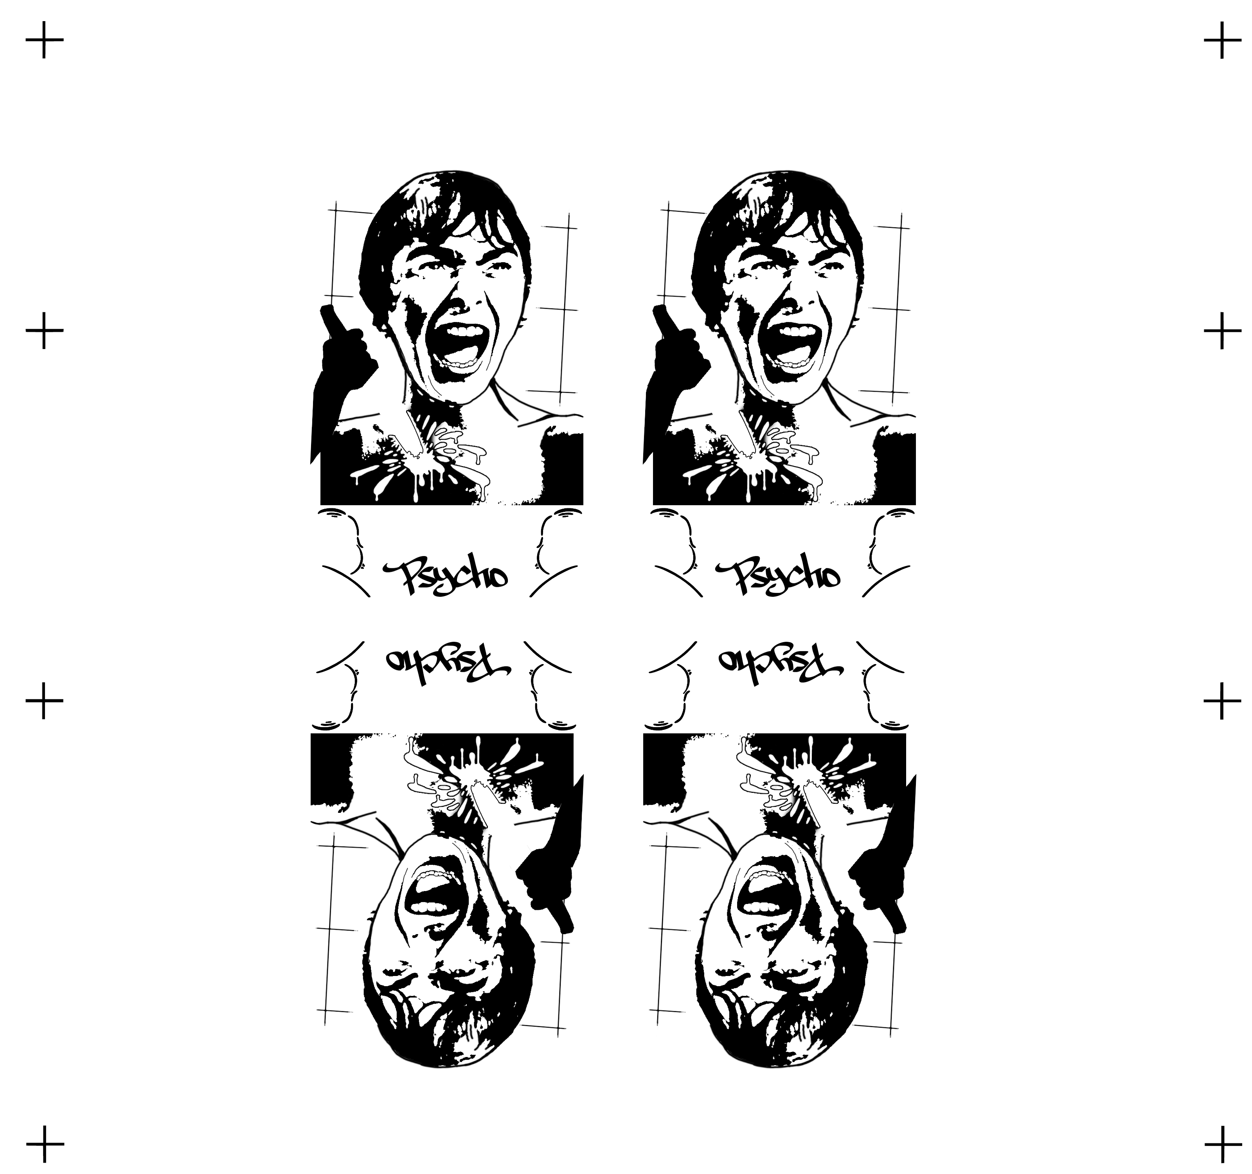
art/Scream_Face_SAO_F_Silk.png
