gowenrw/psycho_badge/eda/psycho_sao/snapshots/psycho_sao_3d_back.png

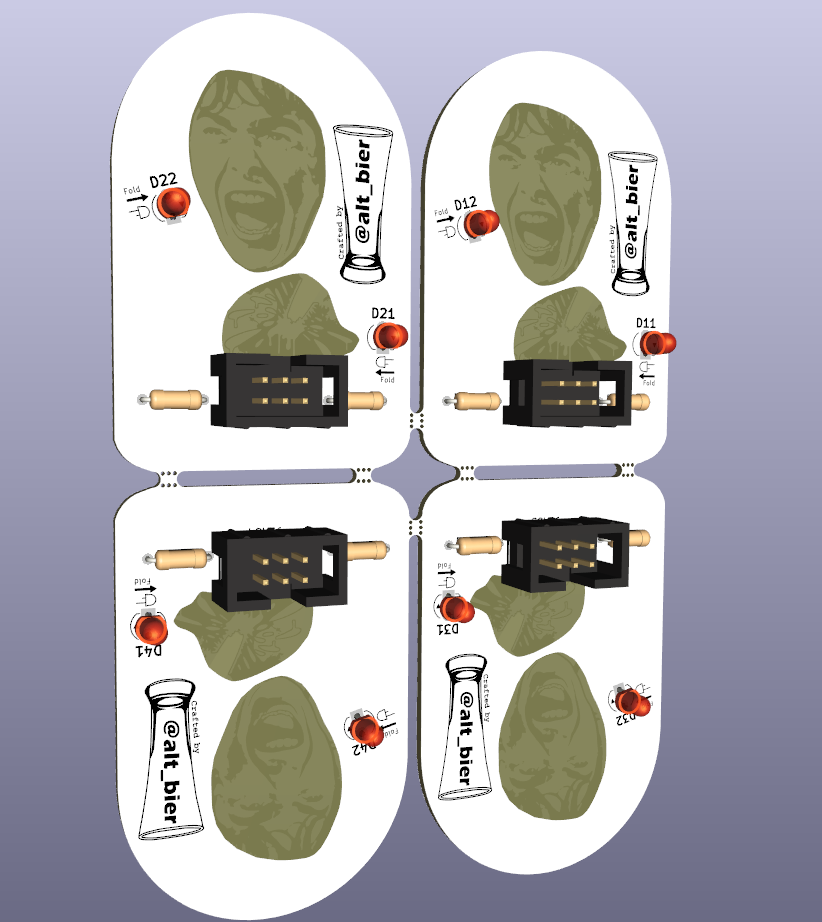
eda/psycho_sao/snapshots/psycho_sao_3d_back.png
