gowenrw/psycho_badge/eda/psycho_sao/snapshots/psycho_sao_3d_front.png

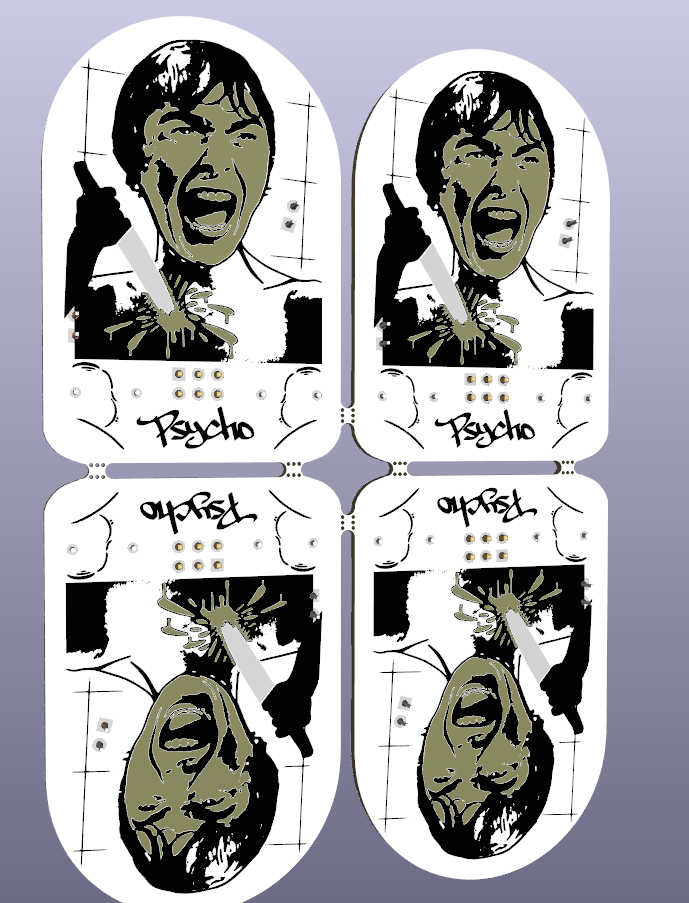
eda/psycho_sao/snapshots/psycho_sao_3d_front.png
