gowenrw/psycho_badge/eda/psycho_sao/3d_models/BatteryHolder_2466_1xAAA.step

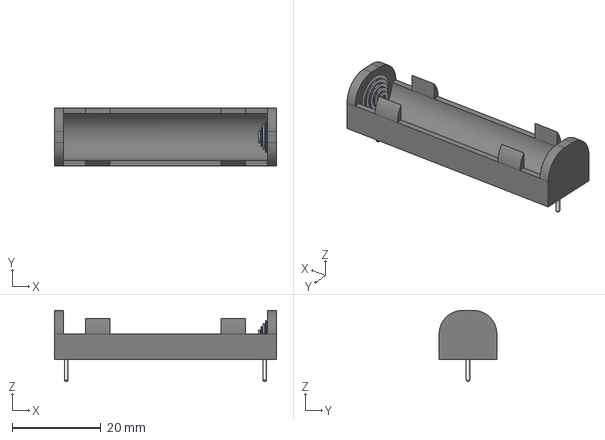
[picture p113: CAD file, 2025-05-31]
eda/psycho_sao/3d_models/BatteryHolder_2466_1xAAA.step
50.0 x 13.0 x 16.0 mm
