gowenrw/psycho_badge/eda/psycho_sao/3d_models/CP_Radial_D5.0mm_P2.00mm.step

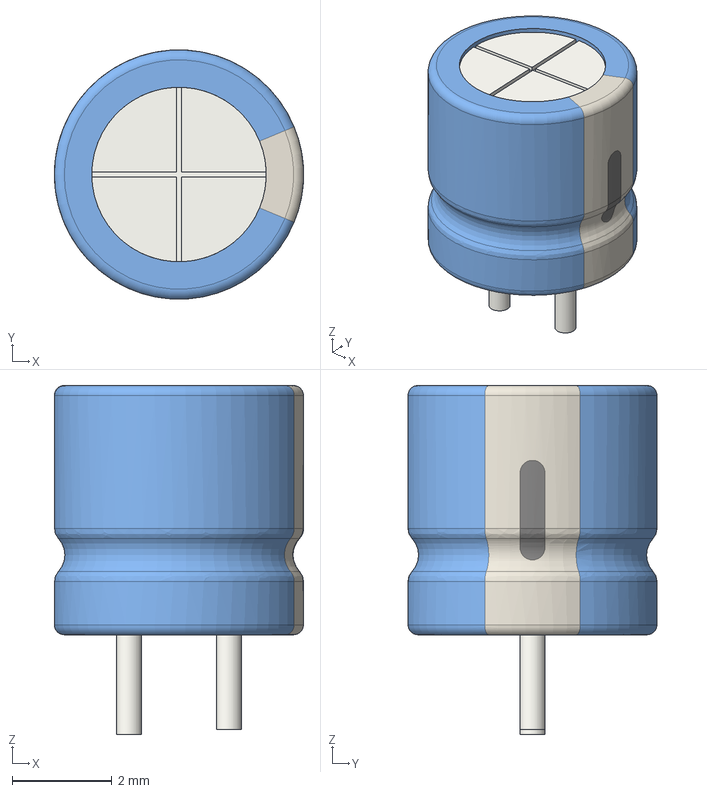
[picture p115: CAD file, 2025-05-31]
eda/psycho_sao/3d_models/CP_Radial_D5.0mm_P2.00mm.step
5.00 x 5.00 x 7.00 mm
