gowenrw/psycho_badge/eda/psycho_sao/3d_models/LED_0805_2012Metric_Castellated.step

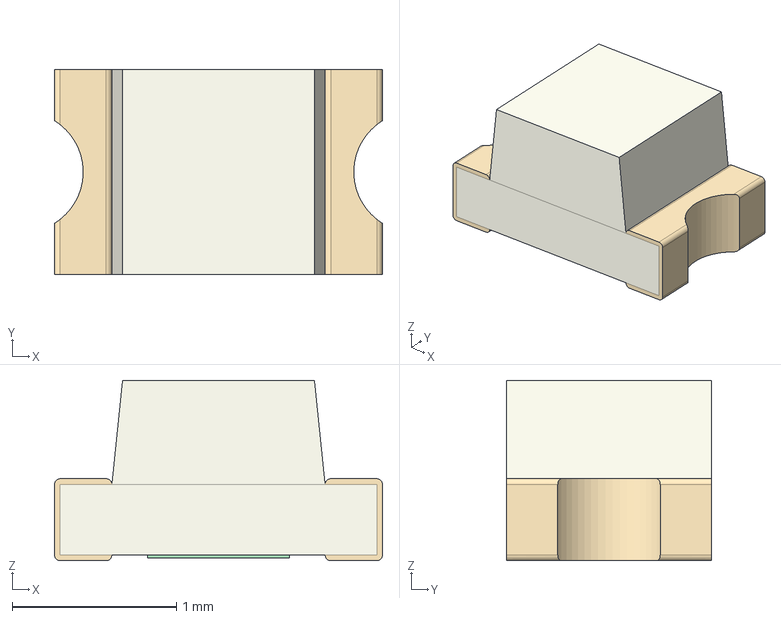
[picture p119: CAD file, 2025-05-31]
eda/psycho_sao/3d_models/LED_0805_2012Metric_Castellated.step
2.00 x 1.25 x 1.10 mm
