gowenrw/psycho_badge/eda/psycho_sao/3d_models/PinHeader_1x04_P2.54mm_Horizontal.step

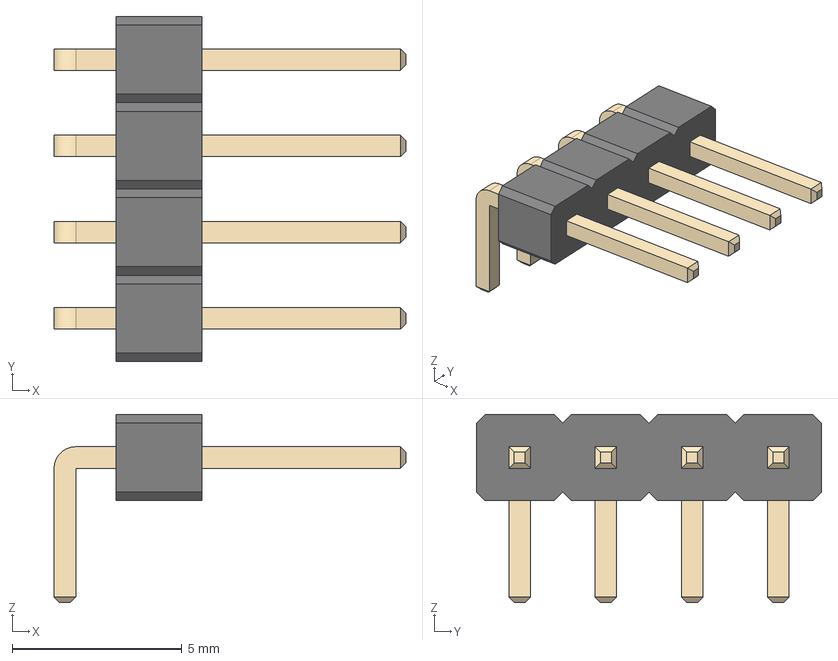
[picture p121: CAD file, 2025-05-31]
eda/psycho_sao/3d_models/PinHeader_1x04_P2.54mm_Horizontal.step
10.4 x 10.2 x 5.54 mm
