gowenrw/psycho_badge/eda/psycho_sao/3d_models/PinHeader_1x10_P2.54mm_Vertical.step

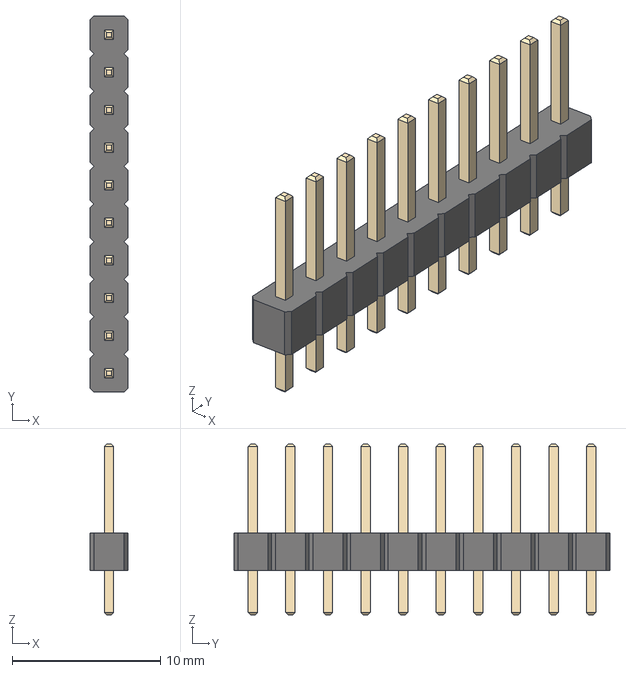
[picture p124: CAD file, 2025-05-31]
eda/psycho_sao/3d_models/PinHeader_1x10_P2.54mm_Vertical.step
2.54 x 25.4 x 11.5 mm
