gowenrw/psycho_badge/eda/psycho_sao/3d_models/LED_D3.0mm-3.step

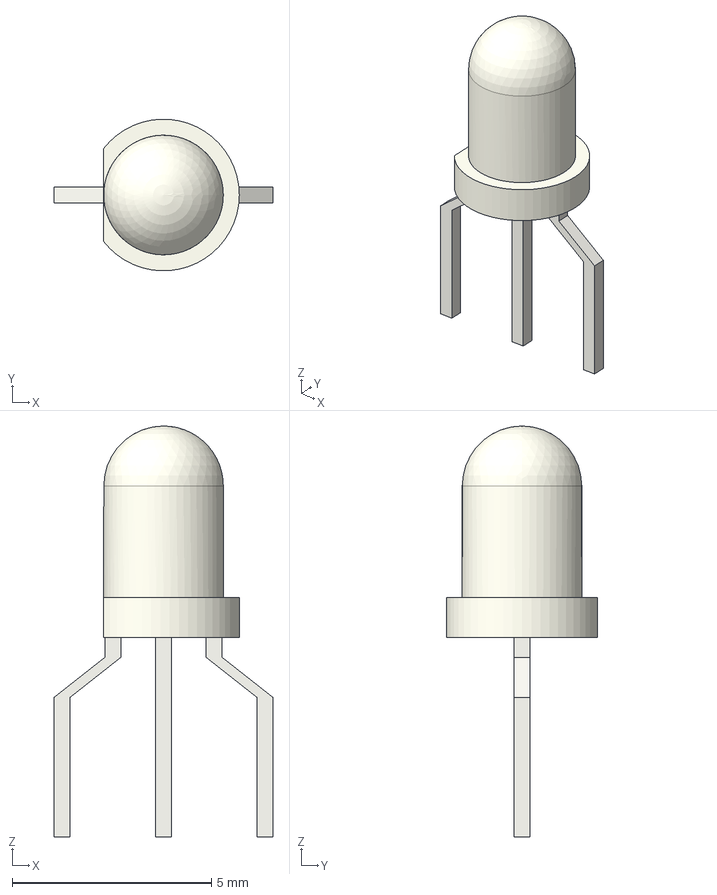
[picture p126: CAD file, 2025-05-31]
eda/psycho_sao/3d_models/LED_D3.0mm-3.step
5.48 x 3.80 x 10.3 mm
