gowenrw/psycho_badge/eda/psycho_sao/3d_models/PinSocket_1x07_P2.54mm_Vertical.step

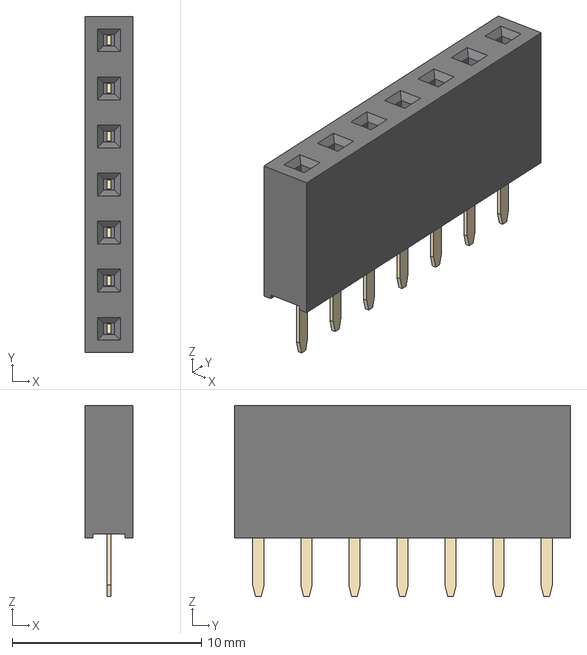
[picture p128: CAD file, 2025-05-31]
eda/psycho_sao/3d_models/PinSocket_1x07_P2.54mm_Vertical.step
2.54 x 17.8 x 10.1 mm
