gowenrw/psycho_badge/eda/psycho_sao/3d_models/PinHeader_1x08_P2.54mm_Horizontal.step

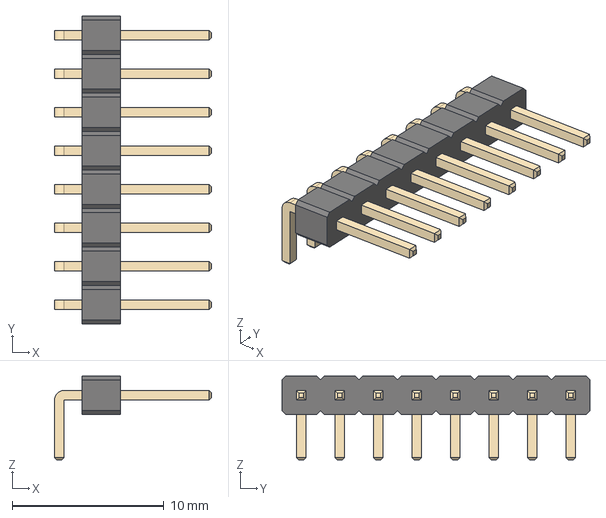
[picture p129: CAD file, 2025-05-31]
eda/psycho_sao/3d_models/PinHeader_1x08_P2.54mm_Horizontal.step
10.4 x 20.3 x 5.54 mm
