gowenrw/psycho_badge/eda/psycho_sao/3d_models/LED_D3.0mm_Horizontal_O1.27mm_Z2.0mm_IRBlack.step

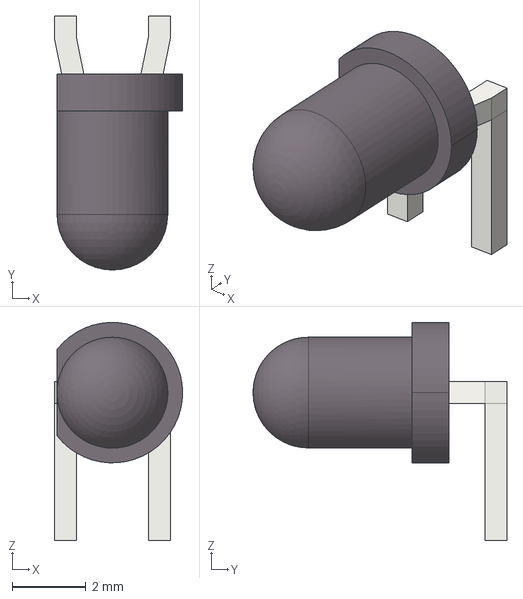
[picture p131: CAD file, 2025-05-31]
eda/psycho_sao/3d_models/LED_D3.0mm_Horizontal_O1.27mm_Z2.0mm_IRBlack.step
3.47 x 6.87 x 5.90 mm
