gowenrw/psycho_badge/eda/psycho_sao/3d_models/Battery_Holder_CR2032_BS-2-1.stp

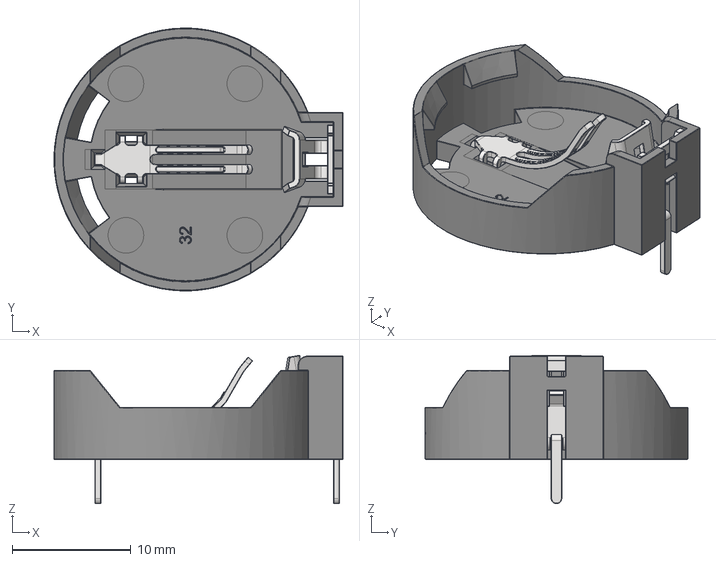
[picture p132: CAD file, 2025-05-31]
eda/psycho_sao/3d_models/Battery_Holder_CR2032_BS-2-1.stp
24.3 x 22.1 x 12.5 mm
