gowenrw/psycho_badge/eda/psycho_sao/3d_models/PinHeader_1x04_P2.54mm_Vertical.step

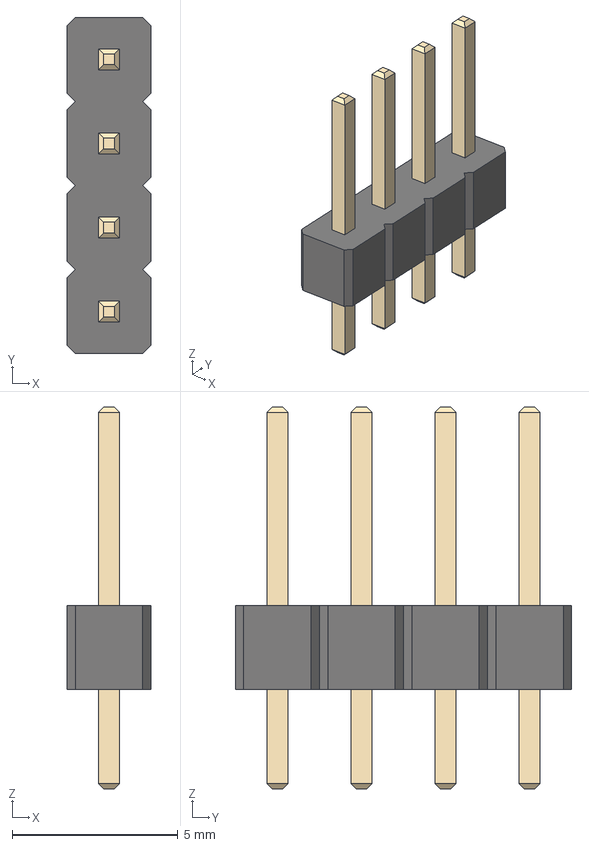
[picture p133: CAD file, 2025-05-31]
eda/psycho_sao/3d_models/PinHeader_1x04_P2.54mm_Vertical.step
2.54 x 10.2 x 11.5 mm
