gowenrw/psycho_badge/eda/psycho_sao/3d_models/LED_D5.0mm.step

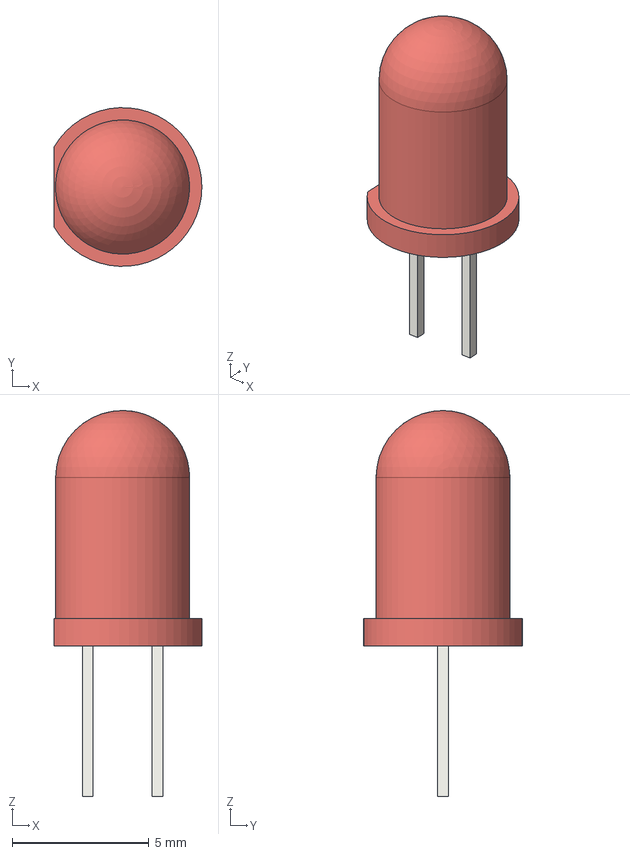
[picture p135: CAD file, 2025-05-31]
eda/psycho_sao/3d_models/LED_D5.0mm.step
5.40 x 5.79 x 14.1 mm
