gowenrw/psycho_badge/eda/psycho_sao/3d_models/IDC-Header_2x03_P2.54mm_Vertical.step

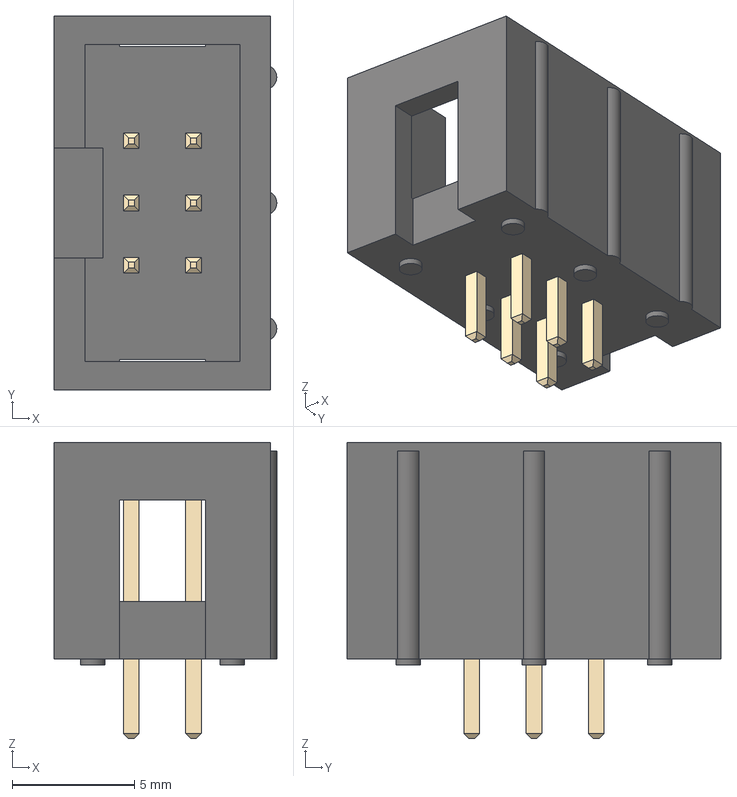
[picture p138: CAD file, 2025-05-31]
eda/psycho_sao/3d_models/IDC-Header_2x03_P2.54mm_Vertical.step
9.10 x 15.3 x 12.1 mm
