gowenrw/psycho_badge/eda/psycho_sao/3d_models/LED_D5.0mm_Horizontal_O6.35mm_Z9.0mm.step

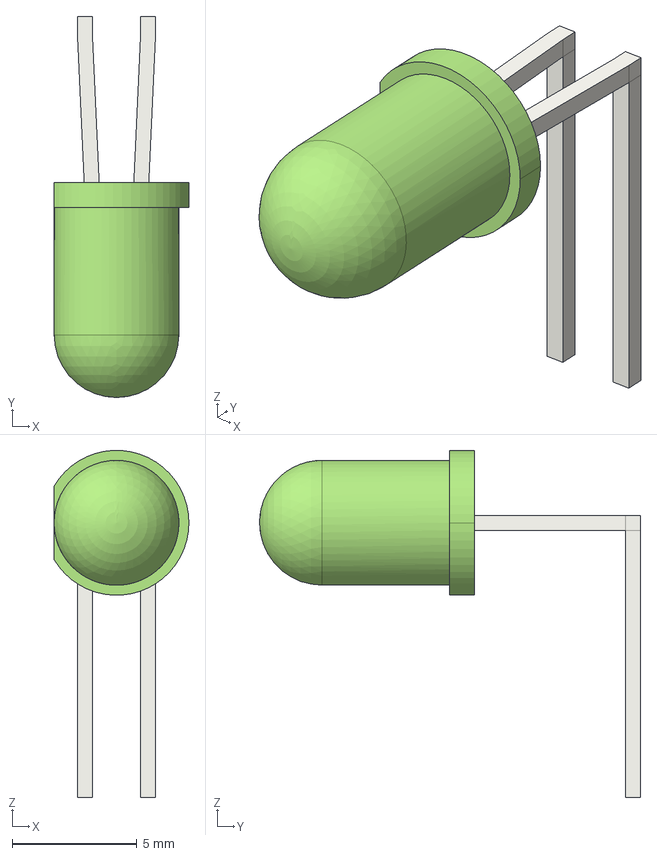
[picture p140: CAD file, 2025-05-31]
eda/psycho_sao/3d_models/LED_D5.0mm_Horizontal_O6.35mm_Z9.0mm.step
5.40 x 15.2 x 13.9 mm
