gowenrw/psycho_badge/eda/psycho_sao/3d_models/LED_0603_1608Metric_Castellated.step

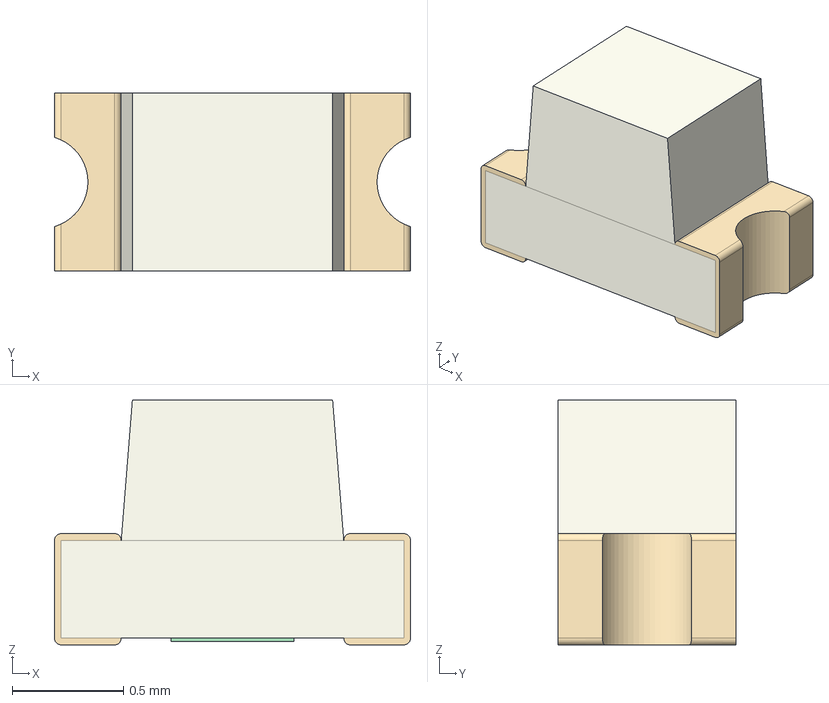
[picture p145: CAD file, 2025-05-31]
eda/psycho_sao/3d_models/LED_0603_1608Metric_Castellated.step
1.60 x 0.8 x 1.10 mm
