gowenrw/psycho_badge/eda/psycho_sao/3d_models/LED_D5.0mm_FlatTop.step

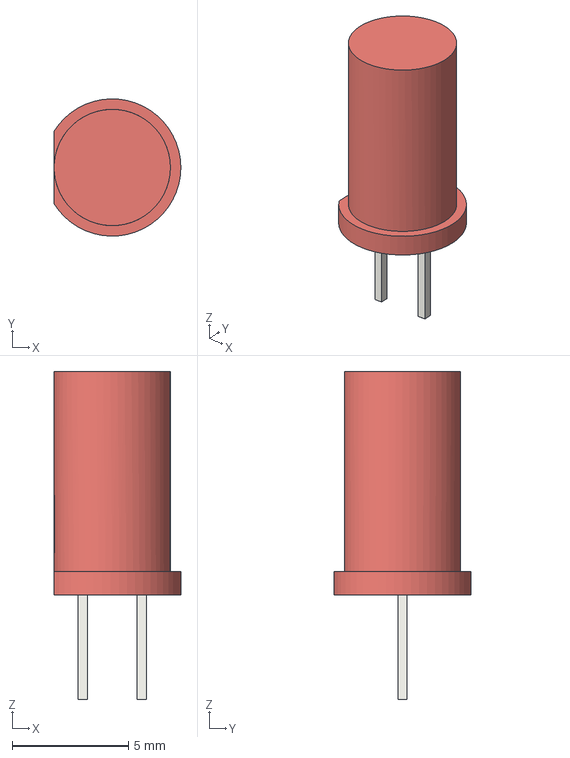
[picture p147: CAD file, 2025-05-31]
eda/psycho_sao/3d_models/LED_D5.0mm_FlatTop.step
5.45 x 5.90 x 14.1 mm
