gowenrw/psycho_badge/eda/psycho_sao/3d_models/BatteryHolder_2468_2xAAA.step

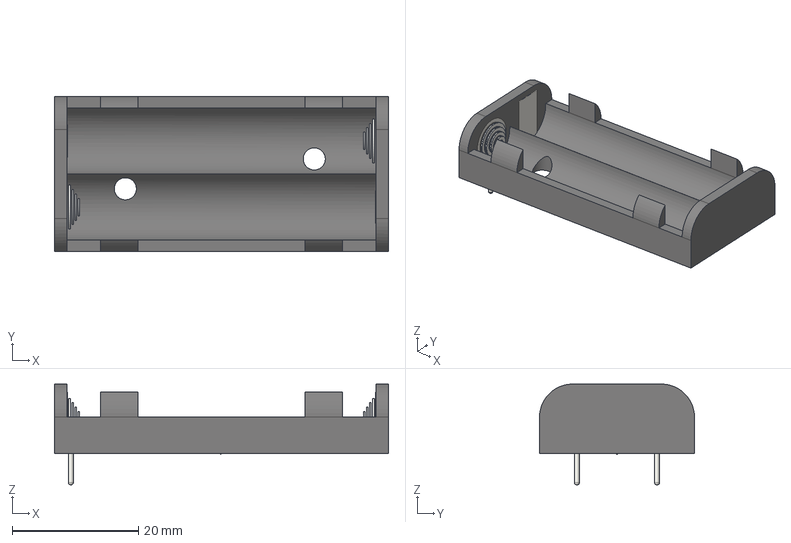
[picture p148: CAD file, 2025-05-31]
eda/psycho_sao/3d_models/BatteryHolder_2468_2xAAA.step
53.0 x 24.6 x 16.0 mm
