gowenrw/psycho_badge/eda/psycho_sao/3d_models/LED_D5.0mm_Horizontal_O3.81mm_Z9.0mm.step

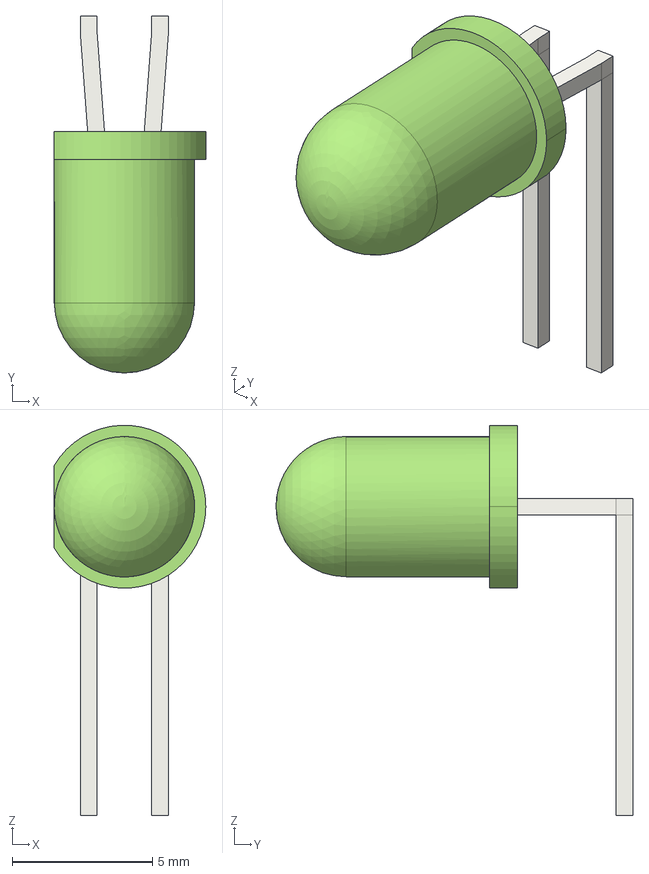
[picture p151: CAD file, 2025-05-31]
eda/psycho_sao/3d_models/LED_D5.0mm_Horizontal_O3.81mm_Z9.0mm.step
5.40 x 12.7 x 13.9 mm
