gowenrw/psycho_badge/eda/psycho_sao/3d_models/PinSocket_1x02_P2.54mm_Vertical.step

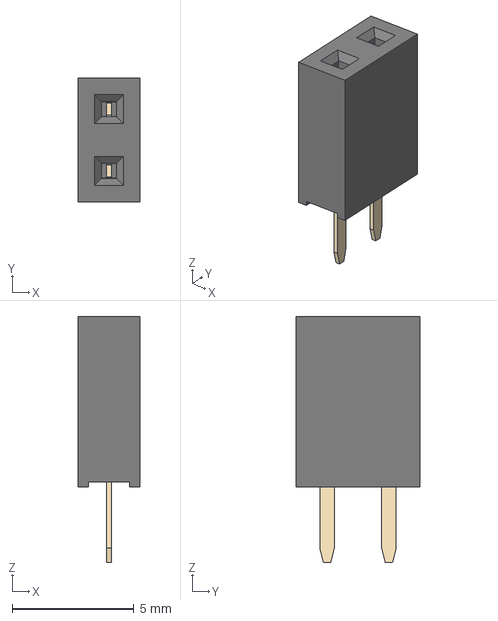
[picture p152: CAD file, 2025-05-31]
eda/psycho_sao/3d_models/PinSocket_1x02_P2.54mm_Vertical.step
2.54 x 5.08 x 10.1 mm
