gowenrw/psycho_badge/eda/psycho_sao/3d_models/PinSocket_1x06_P2.54mm_Vertical.step

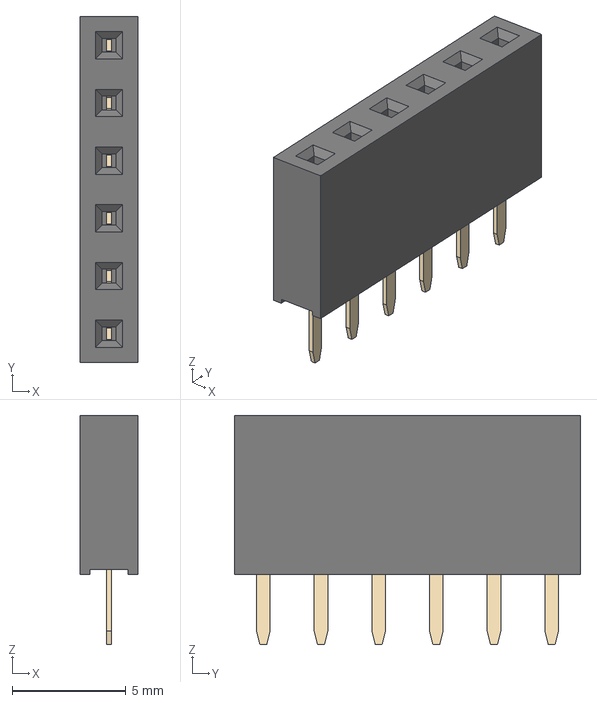
[picture p153: CAD file, 2025-05-31]
eda/psycho_sao/3d_models/PinSocket_1x06_P2.54mm_Vertical.step
2.54 x 15.2 x 10.1 mm
