gowenrw/psycho_badge/eda/psycho_sao/3d_models/LED_D3.0mm_Horizontal_O1.27mm_Z6.0mm.step

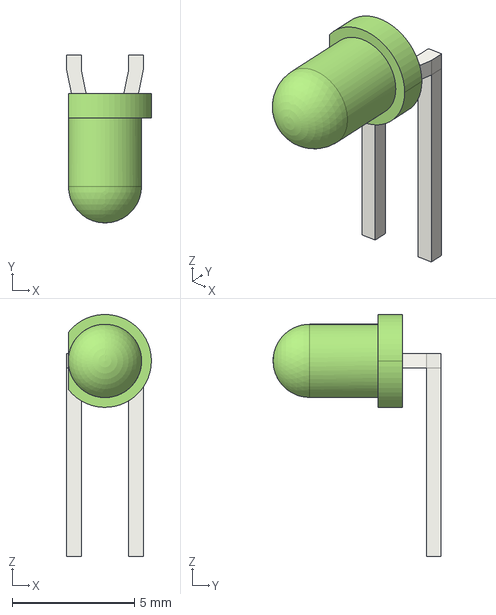
[picture p155: CAD file, 2025-05-31]
eda/psycho_sao/3d_models/LED_D3.0mm_Horizontal_O1.27mm_Z6.0mm.step
3.47 x 6.87 x 9.90 mm
