gowenrw/psycho_badge/eda/psycho_sao/3d_models/RJ45_Amphenol_RJHSE-5080-56544.STEP

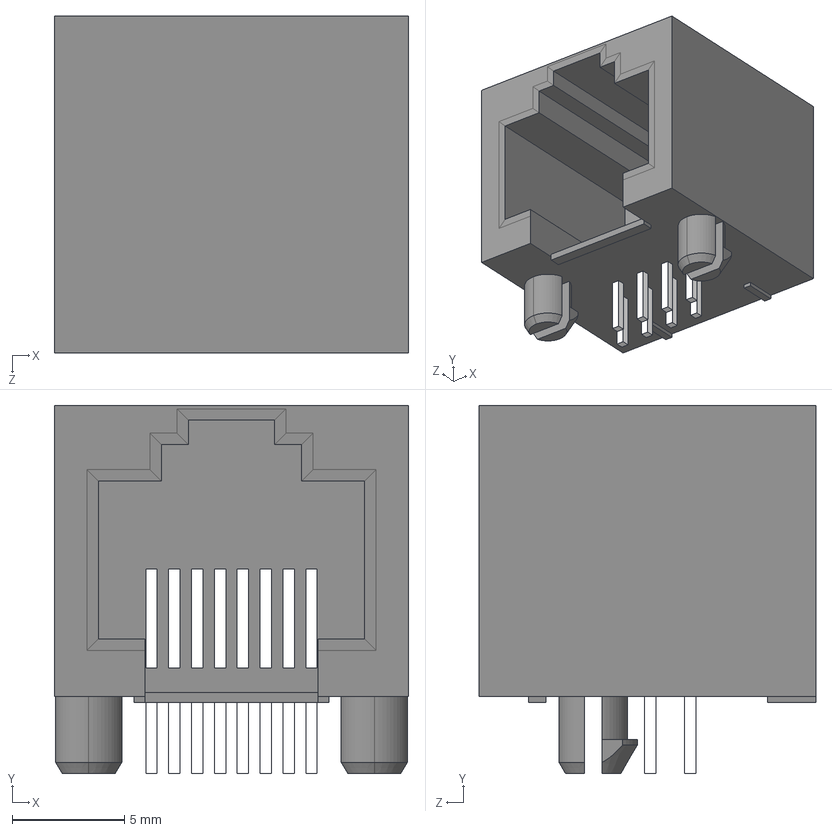
[picture p160: CAD file, 2025-05-31]
eda/psycho_sao/3d_models/RJ45_Amphenol_RJHSE-5080-56544.STEP
15.7 x 16.4 x 15.0 mm
