gowenrw/psycho_badge/eda/psycho_sao/3d_models/LED_D8.0mm.step

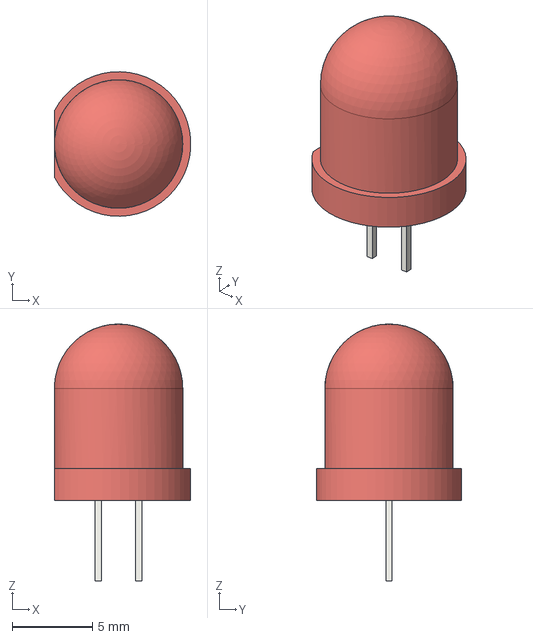
[picture p161: CAD file, 2025-05-31]
eda/psycho_sao/3d_models/LED_D8.0mm.step
8.49 x 9.00 x 16.0 mm
