gowenrw/psycho_badge/eda/psycho_sao/3d_models/PinHeader_1x07_P2.54mm_Horizontal.step

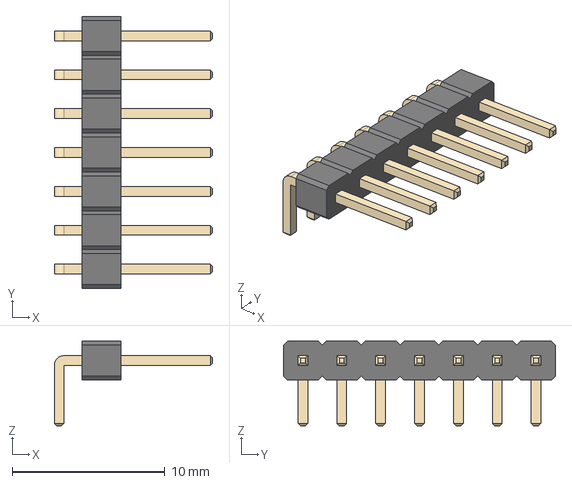
[picture p163: CAD file, 2025-05-31]
eda/psycho_sao/3d_models/PinHeader_1x07_P2.54mm_Horizontal.step
10.4 x 17.8 x 5.54 mm
