gowenrw/psycho_badge/eda/psycho_sao/3d_models/SOIC-16_3.9x9.9mm_P1.27mm.step

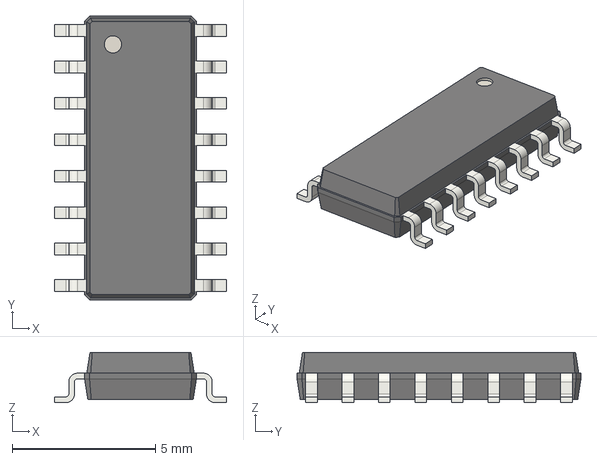
[picture p165: CAD file, 2025-05-31]
eda/psycho_sao/3d_models/SOIC-16_3.9x9.9mm_P1.27mm.step
6.00 x 9.90 x 1.75 mm
