gowenrw/psycho_badge/eda/psycho_sao/3d_models/GC9A01_1.28IN_240x240_v1.step

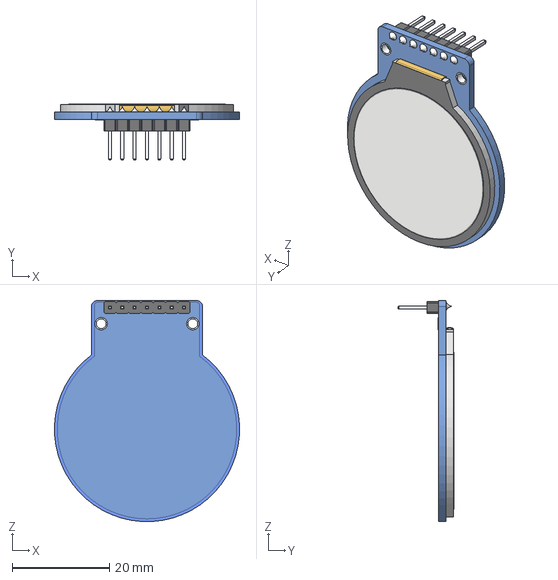
[picture p166: CAD file, 2025-05-31]
eda/psycho_sao/3d_models/GC9A01_1.28IN_240x240_v1.step
38.1 x 11.5 x 45.5 mm
