gowenrw/psycho_badge/eda/psycho_sao/3d_models/SAO_BadgeSide_SFH11-xxPC-D03-ST-BK.STEP

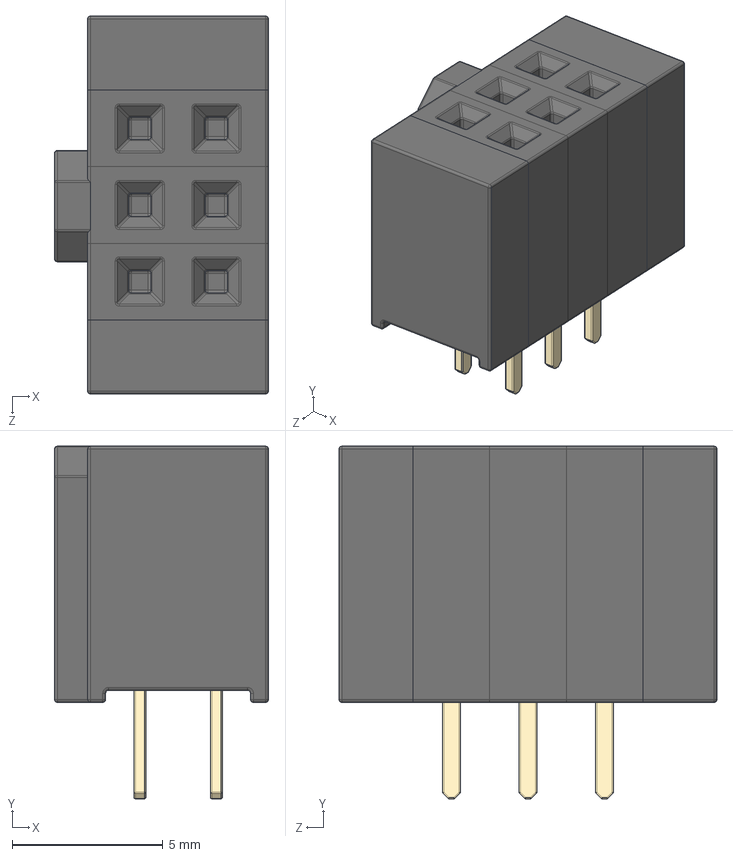
[picture p167: CAD file, 2025-05-31]
eda/psycho_sao/3d_models/SAO_BadgeSide_SFH11-xxPC-D03-ST-BK.STEP
7.10 x 11.7 x 12.5 mm
body section with ST gold pins x 4
end x 2
Polarizing Key
