gowenrw/psycho_badge/eda/psycho_sao/3d_models/LED_D3.0mm_FlatTop.step

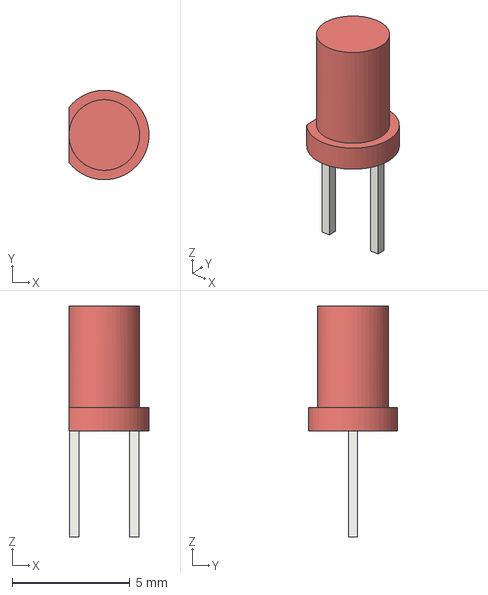
[picture p168: CAD file, 2025-05-31]
eda/psycho_sao/3d_models/LED_D3.0mm_FlatTop.step
3.40 x 3.80 x 9.80 mm
