gowenrw/psycho_badge/eda/psycho_sao/3d_models/LED_1206_3216Metric_Castellated.step

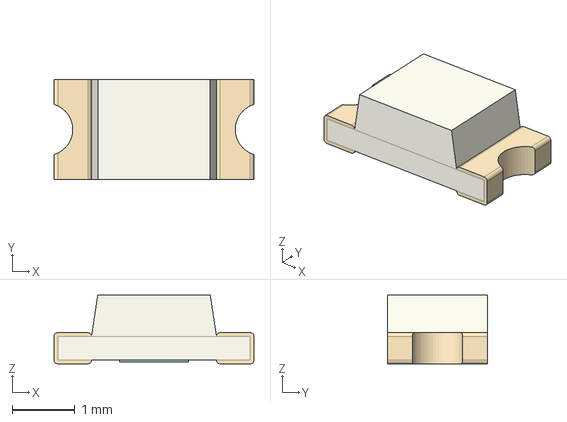
[picture p170: CAD file, 2025-05-31]
eda/psycho_sao/3d_models/LED_1206_3216Metric_Castellated.step
3.20 x 1.60 x 1.10 mm
