gowenrw/psycho_badge/eda/psycho_sao/3d_models/TS2306A.step

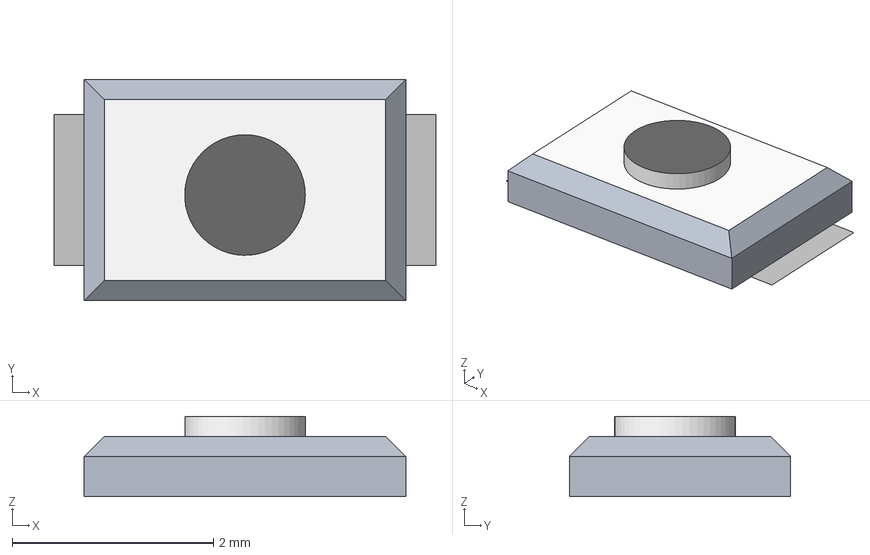
[picture p171: CAD file, 2025-05-31]
eda/psycho_sao/3d_models/TS2306A.step
3.80 x 2.20 x 0.8 mm
Plane
