gowenrw/psycho_badge/eda/psycho_sao/3d_models/USB_Micro-B_Molex_47346-0001.step

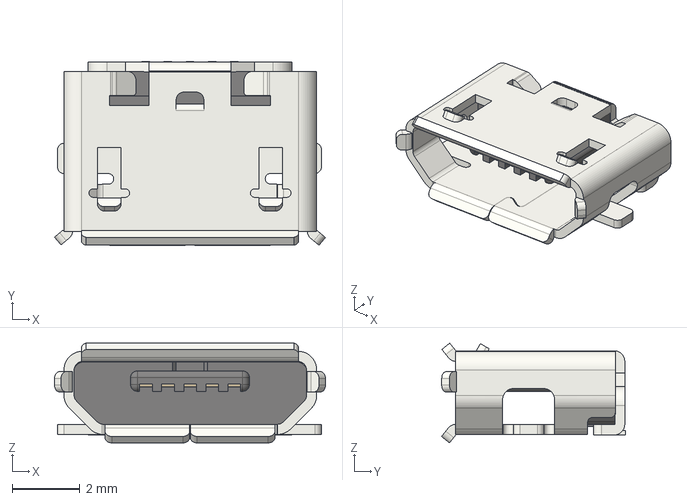
[picture p172: CAD file, 2025-05-31]
eda/psycho_sao/3d_models/USB_Micro-B_Molex_47346-0001.step
7.98 x 5.42 x 2.94 mm
