gowenrw/psycho_badge/eda/psycho_sao/3d_models/C_0805_2012Metric.step

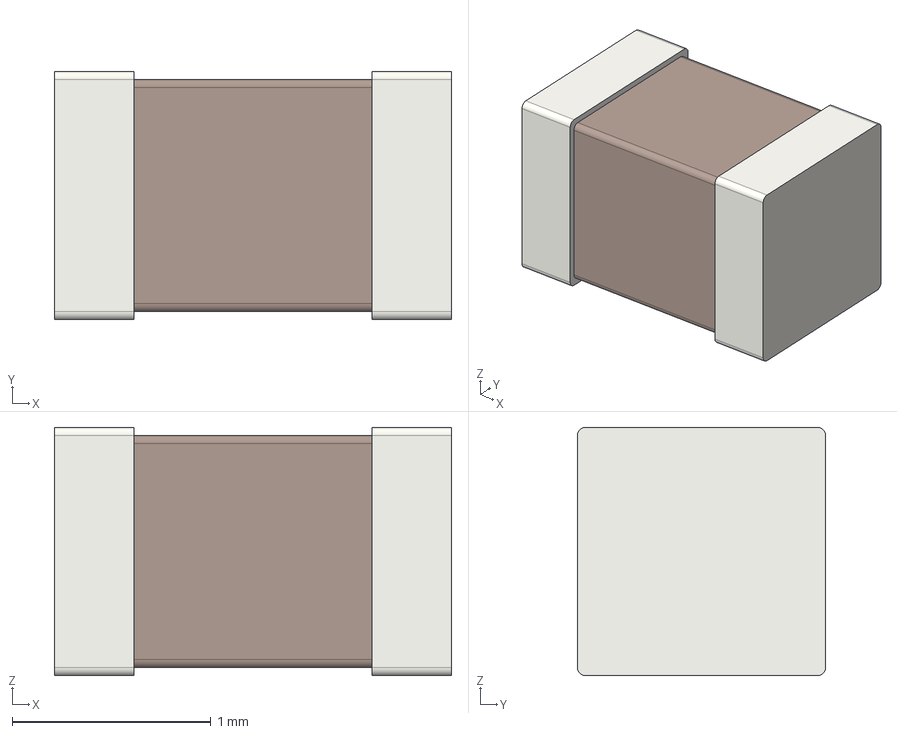
[picture p177: CAD file, 2025-05-31]
eda/psycho_sao/3d_models/C_0805_2012Metric.step
2.00 x 1.25 x 1.25 mm
