gowenrw/psycho_badge/eda/psycho_sao/3d_models/R_0805_2012Metric.step

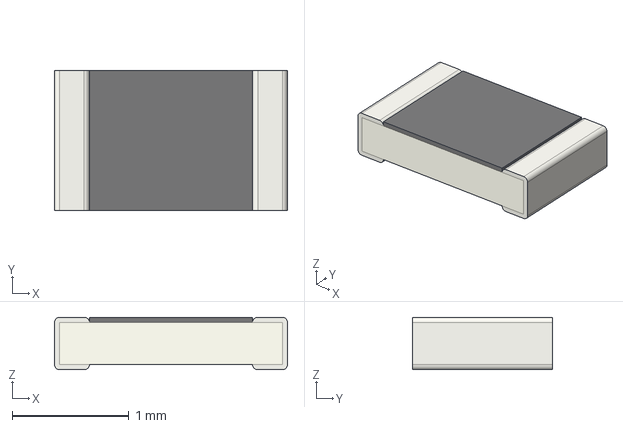
[picture p180: CAD file, 2025-05-31]
eda/psycho_sao/3d_models/R_0805_2012Metric.step
2.00 x 1.20 x 0.45 mm
