gowenrw/psycho_badge/eda/psycho_sao/3d_models/C_Disc_D3.0mm_W2.0mm_P2.50mm.step

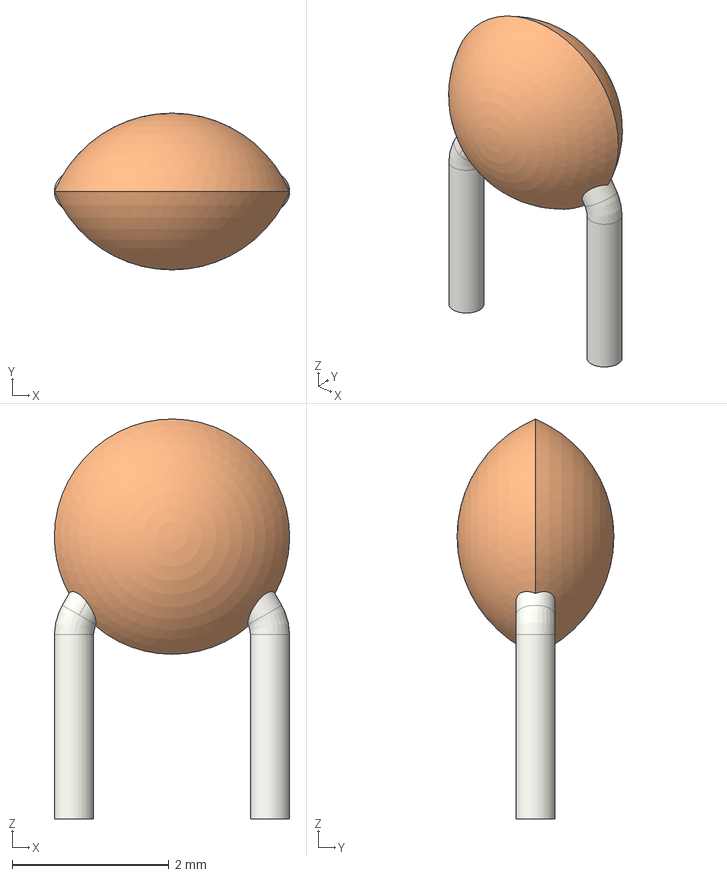
[picture p183: CAD file, 2025-05-31]
eda/psycho_sao/3d_models/C_Disc_D3.0mm_W2.0mm_P2.50mm.step
3.00 x 2.00 x 5.10 mm
