gowenrw/psycho_badge/eda/psycho_sao/3d_models/TO-92_Inline.step

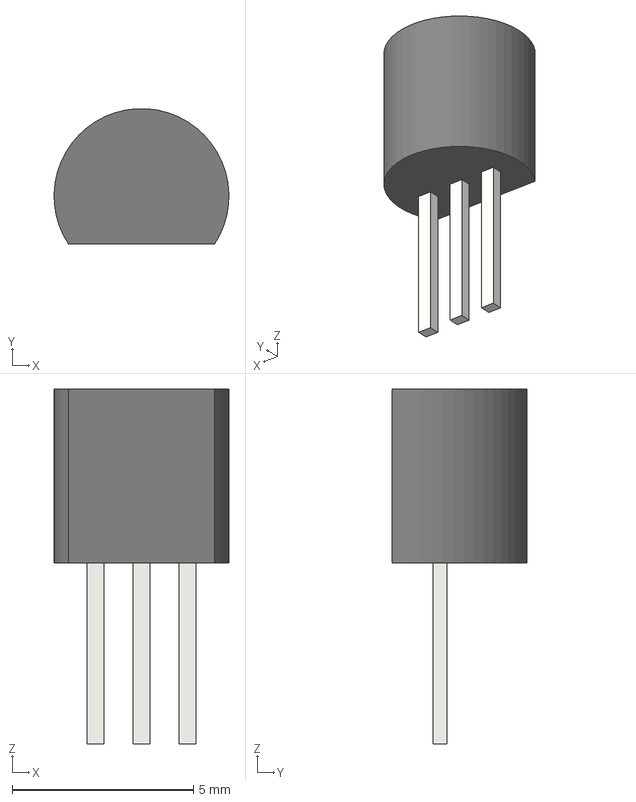
[picture p185: CAD file, 2025-05-31]
eda/psycho_sao/3d_models/TO-92_Inline.step
4.83 x 3.74 x 9.80 mm
