gowenrw/psycho_badge/eda/psycho_sao/3d_models/PinSocket_2x03_P2.54mm_Vertical.step

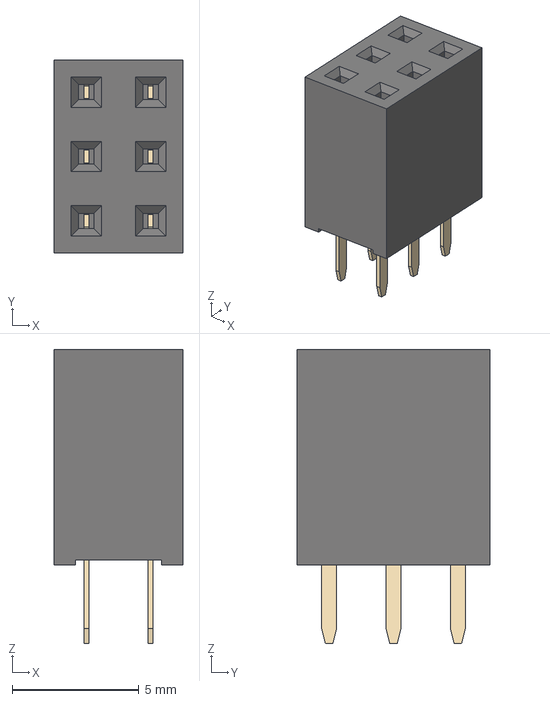
[picture p187: CAD file, 2025-05-31]
eda/psycho_sao/3d_models/PinSocket_2x03_P2.54mm_Vertical.step
5.08 x 7.62 x 11.6 mm
