gowenrw/psycho_badge/eda/psycho_sao/3d_models/PinSocket_1x04_P2.54mm_Horizontal.step

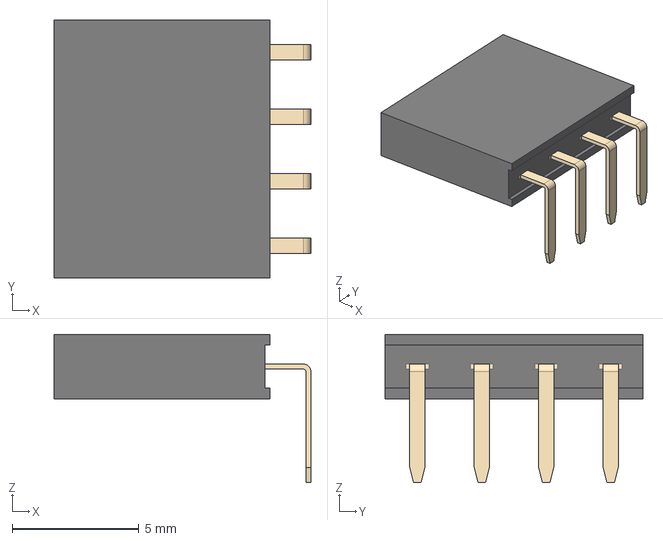
[picture p188: CAD file, 2025-05-31]
eda/psycho_sao/3d_models/PinSocket_1x04_P2.54mm_Horizontal.step
10.1 x 10.2 x 5.84 mm
