gowenrw/psycho_badge/eda/psycho_sao/3d_models/LED_D3.0mm.step

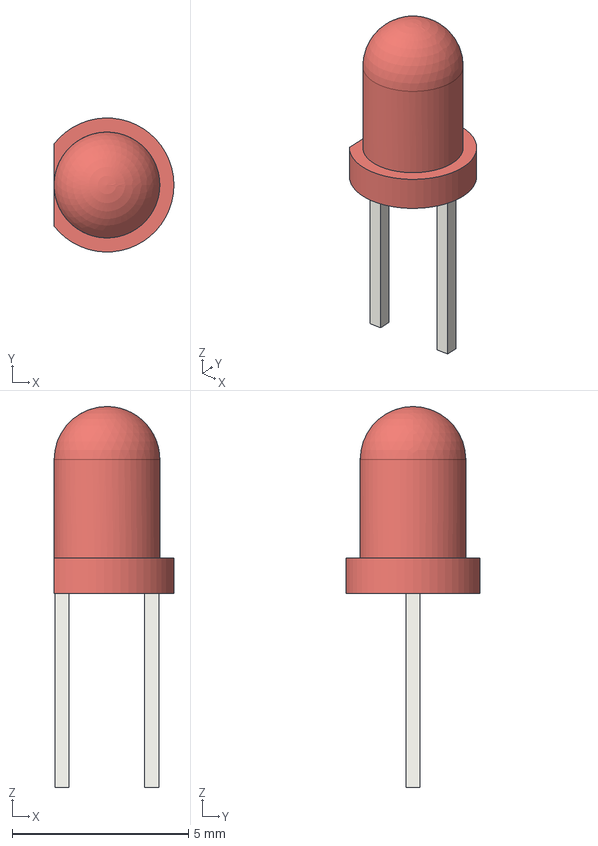
[picture p189: CAD file, 2025-05-31]
eda/psycho_sao/3d_models/LED_D3.0mm.step
3.40 x 3.80 x 10.8 mm
