gowenrw/psycho_badge/eda/psycho_sao/3d_models/LED_D5.0mm_Horizontal_O6.35mm_Z3.0mm.step

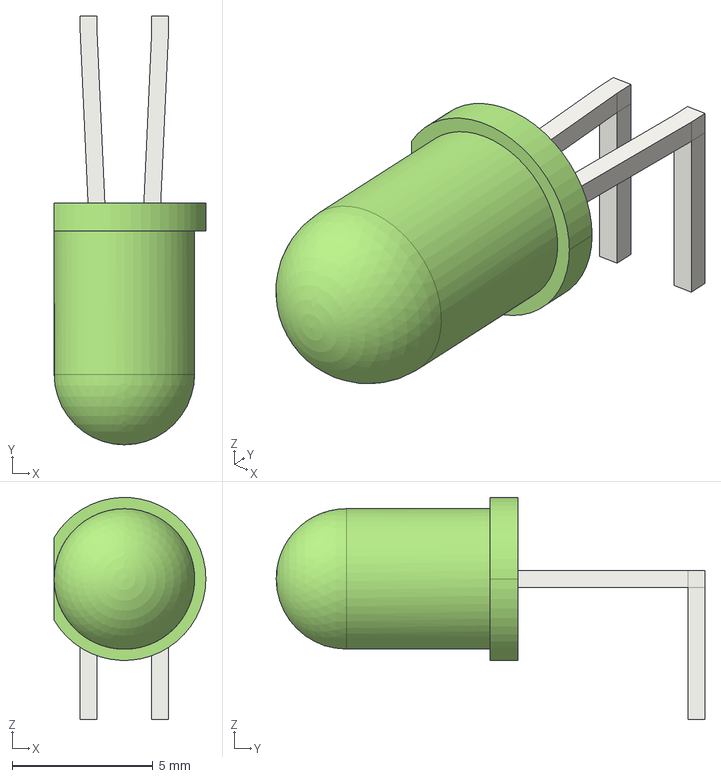
[picture p190: CAD file, 2025-05-31]
eda/psycho_sao/3d_models/LED_D5.0mm_Horizontal_O6.35mm_Z3.0mm.step
5.40 x 15.2 x 7.90 mm
