gowenrw/psycho_badge/eda/psycho_sao/3d_models/SOT-23.step

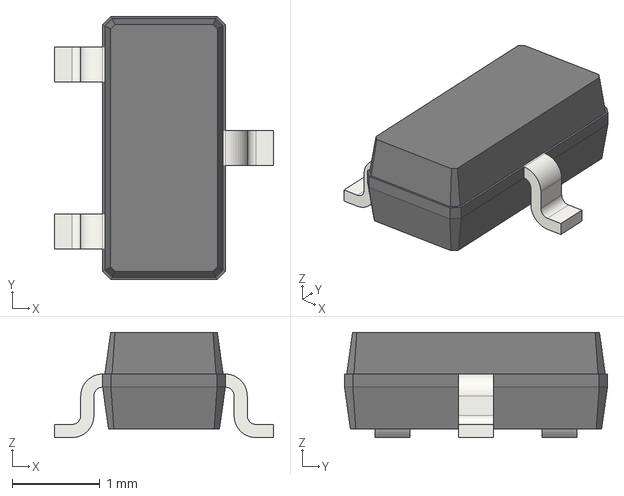
[picture p191: CAD file, 2025-05-31]
eda/psycho_sao/3d_models/SOT-23.step
2.50 x 3.00 x 1.20 mm
