gowenrw/psycho_badge/eda/psycho_sao/3d_models/PinHeader_1x15_P2.54mm_Horizontal.step

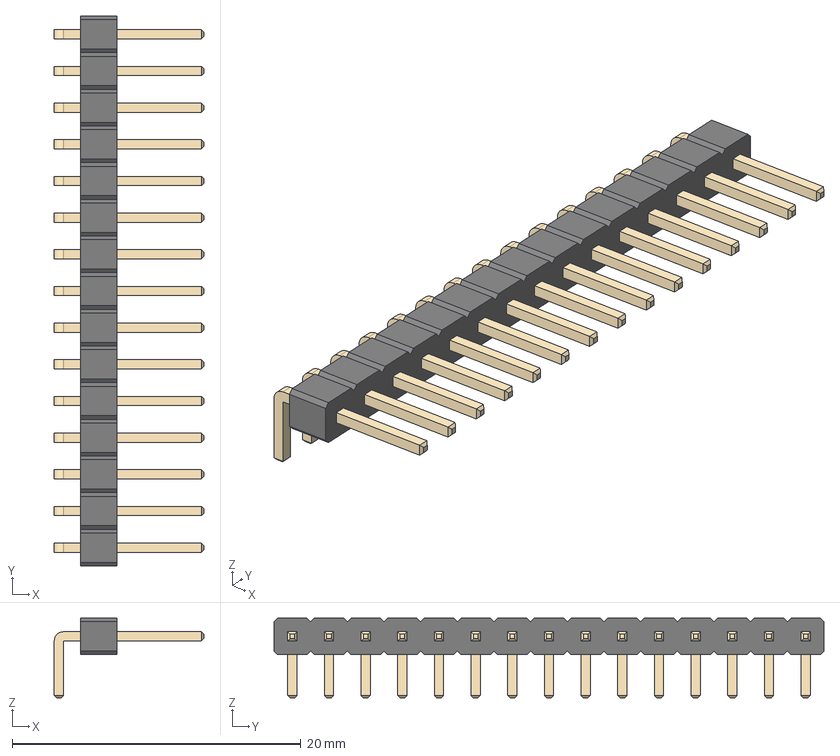
[picture p192: CAD file, 2025-05-31]
eda/psycho_sao/3d_models/PinHeader_1x15_P2.54mm_Horizontal.step
10.4 x 38.1 x 5.54 mm
