gowenrw/psycho_badge/eda/psycho_sao/3d_models/PinHeader_1x07_P2.54mm_Vertical.step

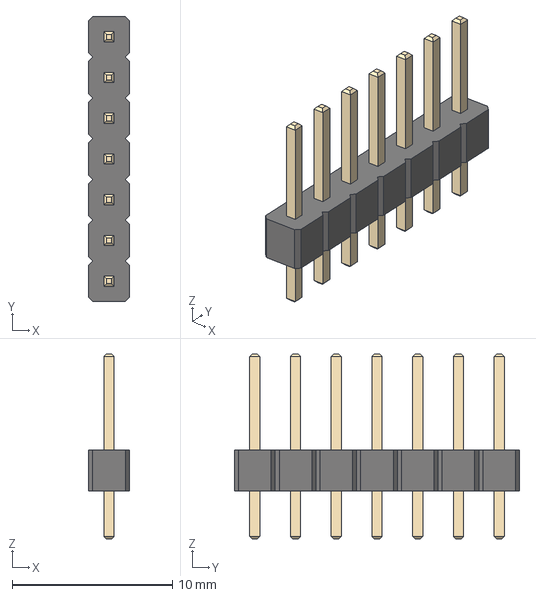
[picture p194: CAD file, 2025-05-31]
eda/psycho_sao/3d_models/PinHeader_1x07_P2.54mm_Vertical.step
2.54 x 17.8 x 11.5 mm
