gowenrw/psycho_badge/eda/psycho_sao/3d_models/LED_D3.0mm_Horizontal_O3.81mm_Z10.0mm.step

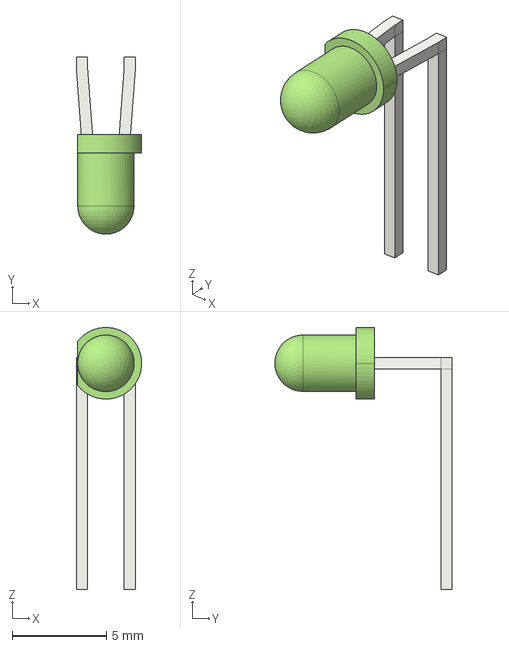
[picture p197: CAD file, 2025-05-31]
eda/psycho_sao/3d_models/LED_D3.0mm_Horizontal_O3.81mm_Z10.0mm.step
3.47 x 9.41 x 13.9 mm
