gowenrw/psycho_badge/eda/psycho_sao/3d_models/CP_Radial_D6.3mm_P2.50mm.step

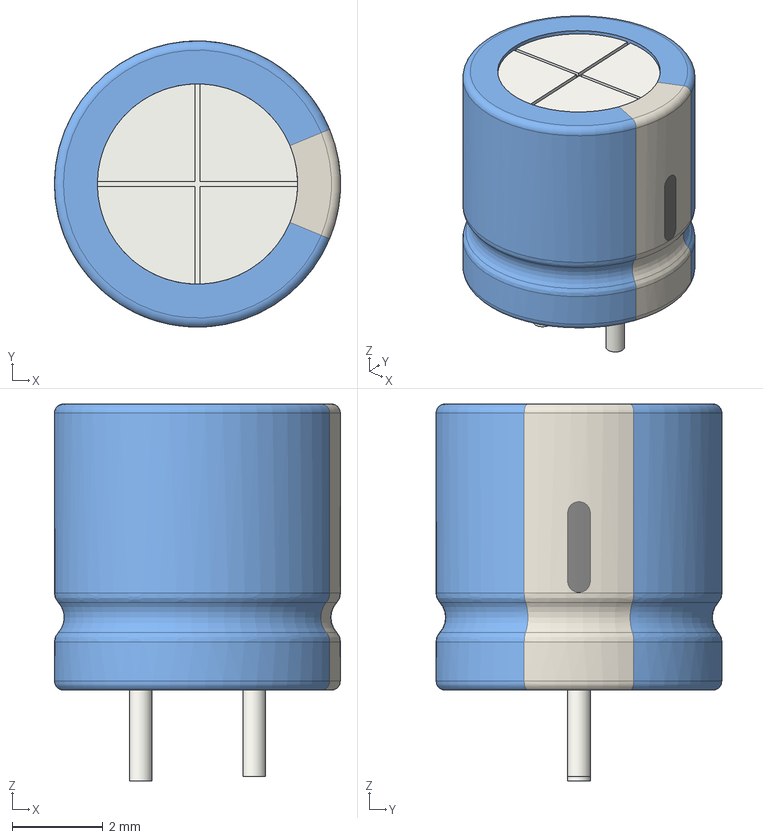
[picture p200: CAD file, 2025-05-31]
eda/psycho_sao/3d_models/CP_Radial_D6.3mm_P2.50mm.step
6.30 x 6.30 x 8.30 mm
