gowenrw/psycho_badge/eda/psycho_sao/3d_models/LED_D3.0mm_Horizontal_O6.35mm_Z2.0mm.step

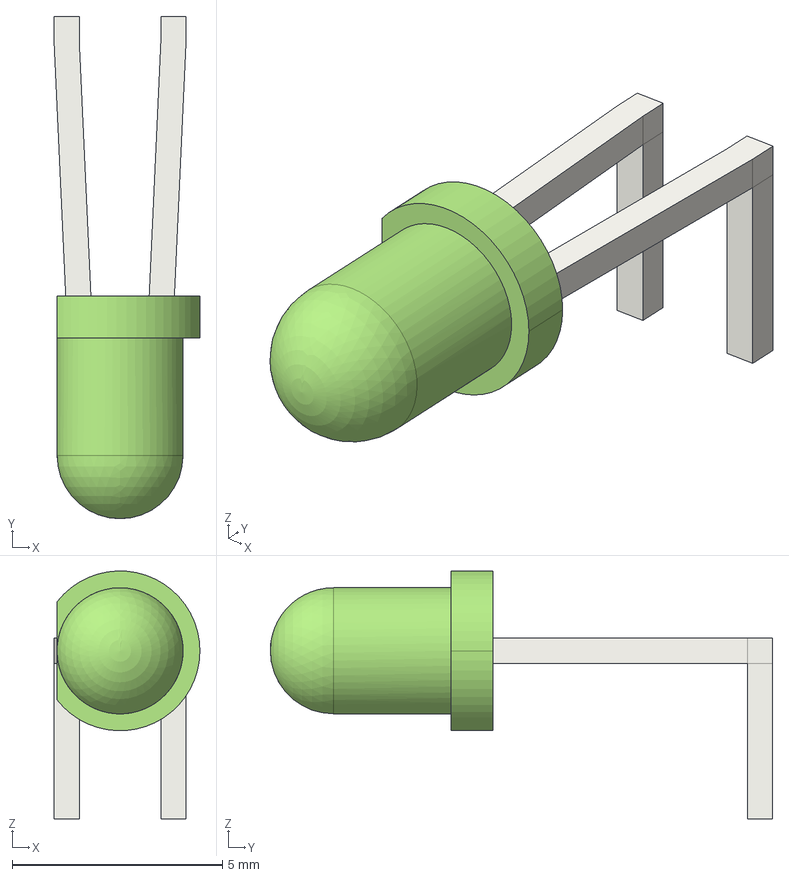
[picture p201: CAD file, 2025-05-31]
eda/psycho_sao/3d_models/LED_D3.0mm_Horizontal_O6.35mm_Z2.0mm.step
3.47 x 12.0 x 5.90 mm
