gowenrw/psycho_badge/eda/psycho_sao/3d_models/SW_SPDT_PCM12.step

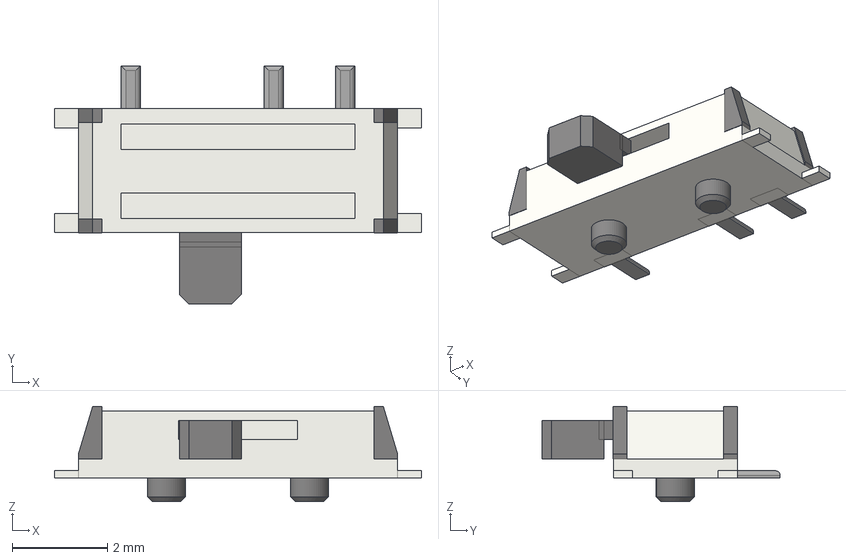
[picture p202: CAD file, 2025-05-31]
eda/psycho_sao/3d_models/SW_SPDT_PCM12.step
7.70 x 5.00 x 2.00 mm
