gowenrw/psycho_badge/eda/psycho_sao/3d_models/R_0603_1608Metric.step

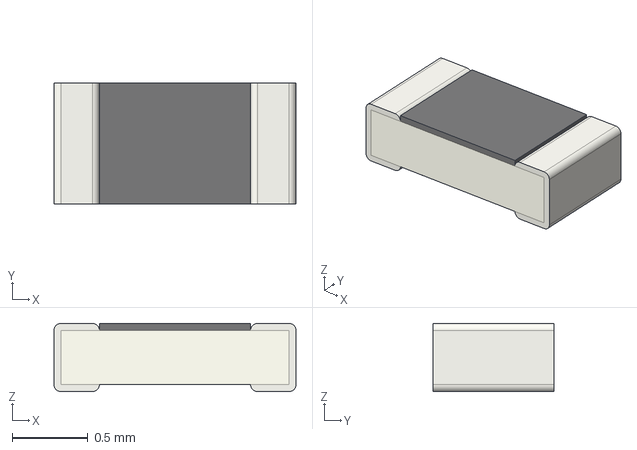
[picture p204: CAD file, 2025-05-31]
eda/psycho_sao/3d_models/R_0603_1608Metric.step
1.60 x 0.8 x 0.45 mm
