gowenrw/psycho_badge/eda/psycho_sao/3d_models/RJ45_Amphenol_RJHSE538X.step

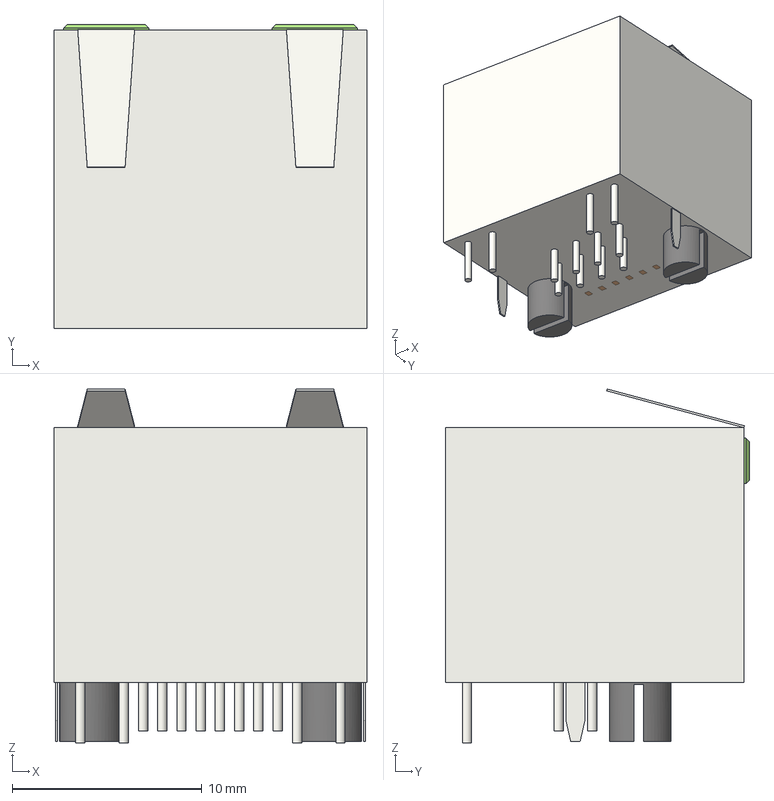
[picture p205: CAD file, 2025-05-31]
eda/psycho_sao/3d_models/RJ45_Amphenol_RJHSE538X.step
16.5 x 16.1 x 18.7 mm
