gowenrw/psycho_badge/eda/psycho_sao/3d_models/Battery_Holder_3xAAA_Simple.step

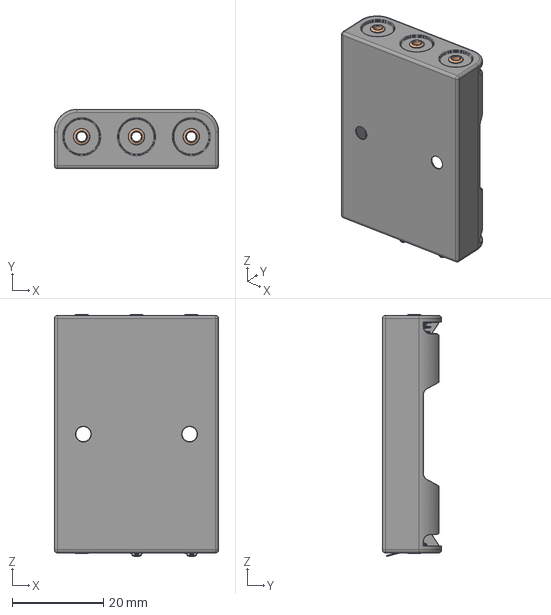
[picture p209: CAD file, 2025-05-31]
eda/psycho_sao/3d_models/Battery_Holder_3xAAA_Simple.step
36.0 x 13.0 x 53.0 mm
