gowenrw/psycho_badge/eda/psycho_sao/3d_models/PinSocket_1x01_P2.54mm_Horizontal.step

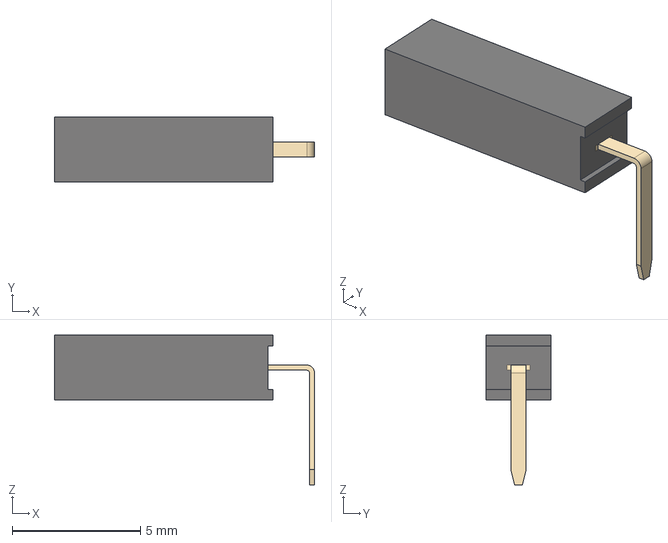
[picture p210: CAD file, 2025-05-31]
eda/psycho_sao/3d_models/PinSocket_1x01_P2.54mm_Horizontal.step
10.1 x 2.54 x 5.84 mm
