gowenrw/psycho_badge/eda/psycho_sao/3d_models/R_1206_3216Metric.step

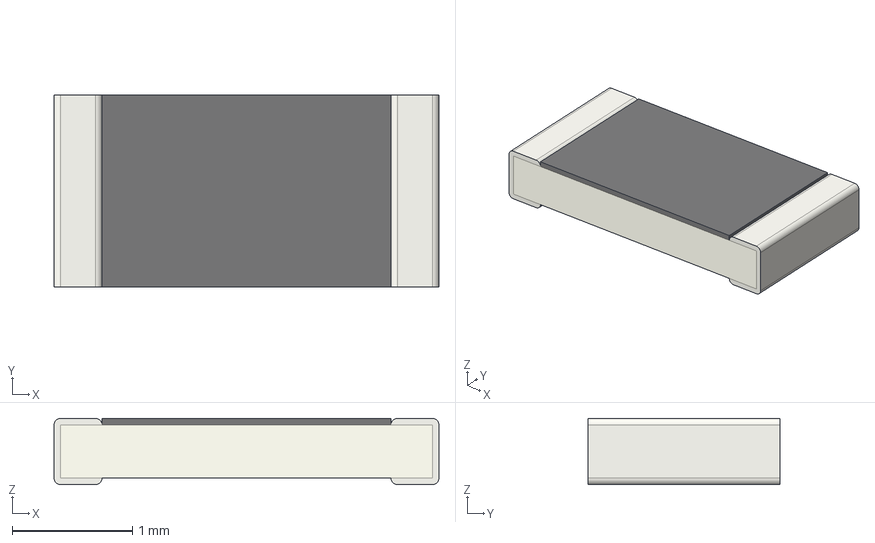
[picture p211: CAD file, 2025-05-31]
eda/psycho_sao/3d_models/R_1206_3216Metric.step
3.20 x 1.60 x 0.55 mm
