gowenrw/psycho_badge/eda/psycho_sao/3d_models/CUI_PXO7803-500-M-TR.step

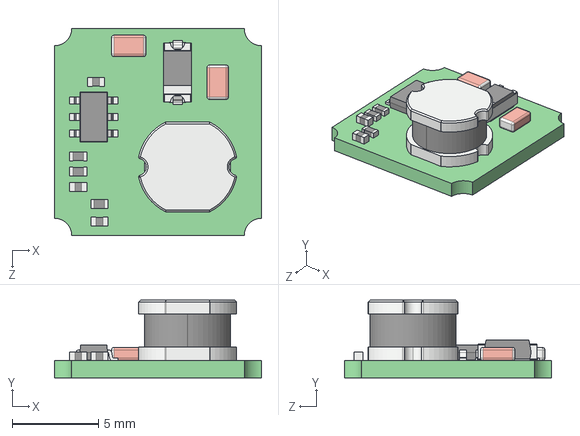
[picture p212: CAD file, 2025-05-31]
eda/psycho_sao/3d_models/CUI_PXO7803-500-M-TR.step
12.0 x 4.50 x 12.0 mm
