gowenrw/psycho_badge/eda/psycho_badge/snapshots/psycho_badge_eink_dev_pcb_rev1.pdf

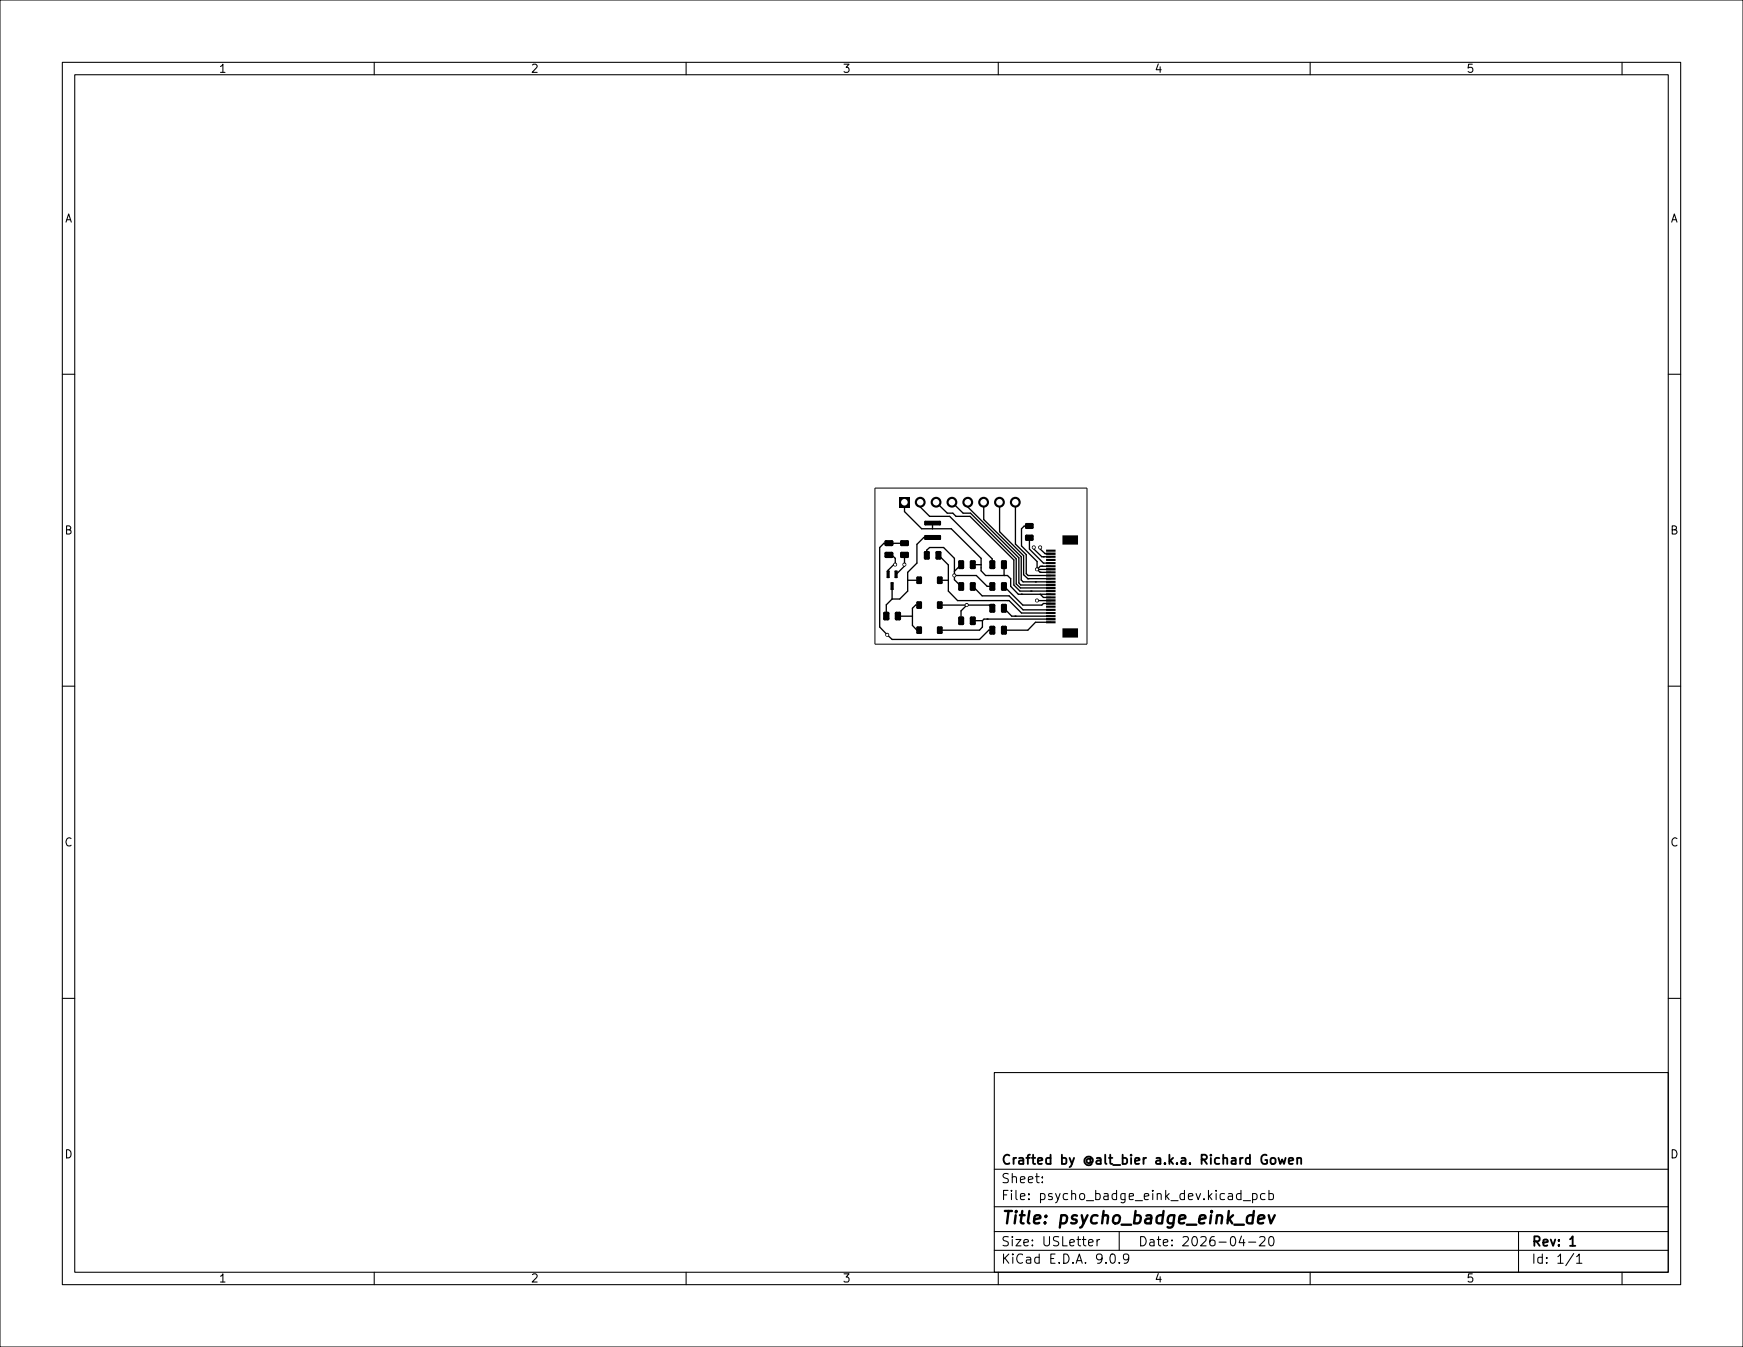
[picture p223: page 1]

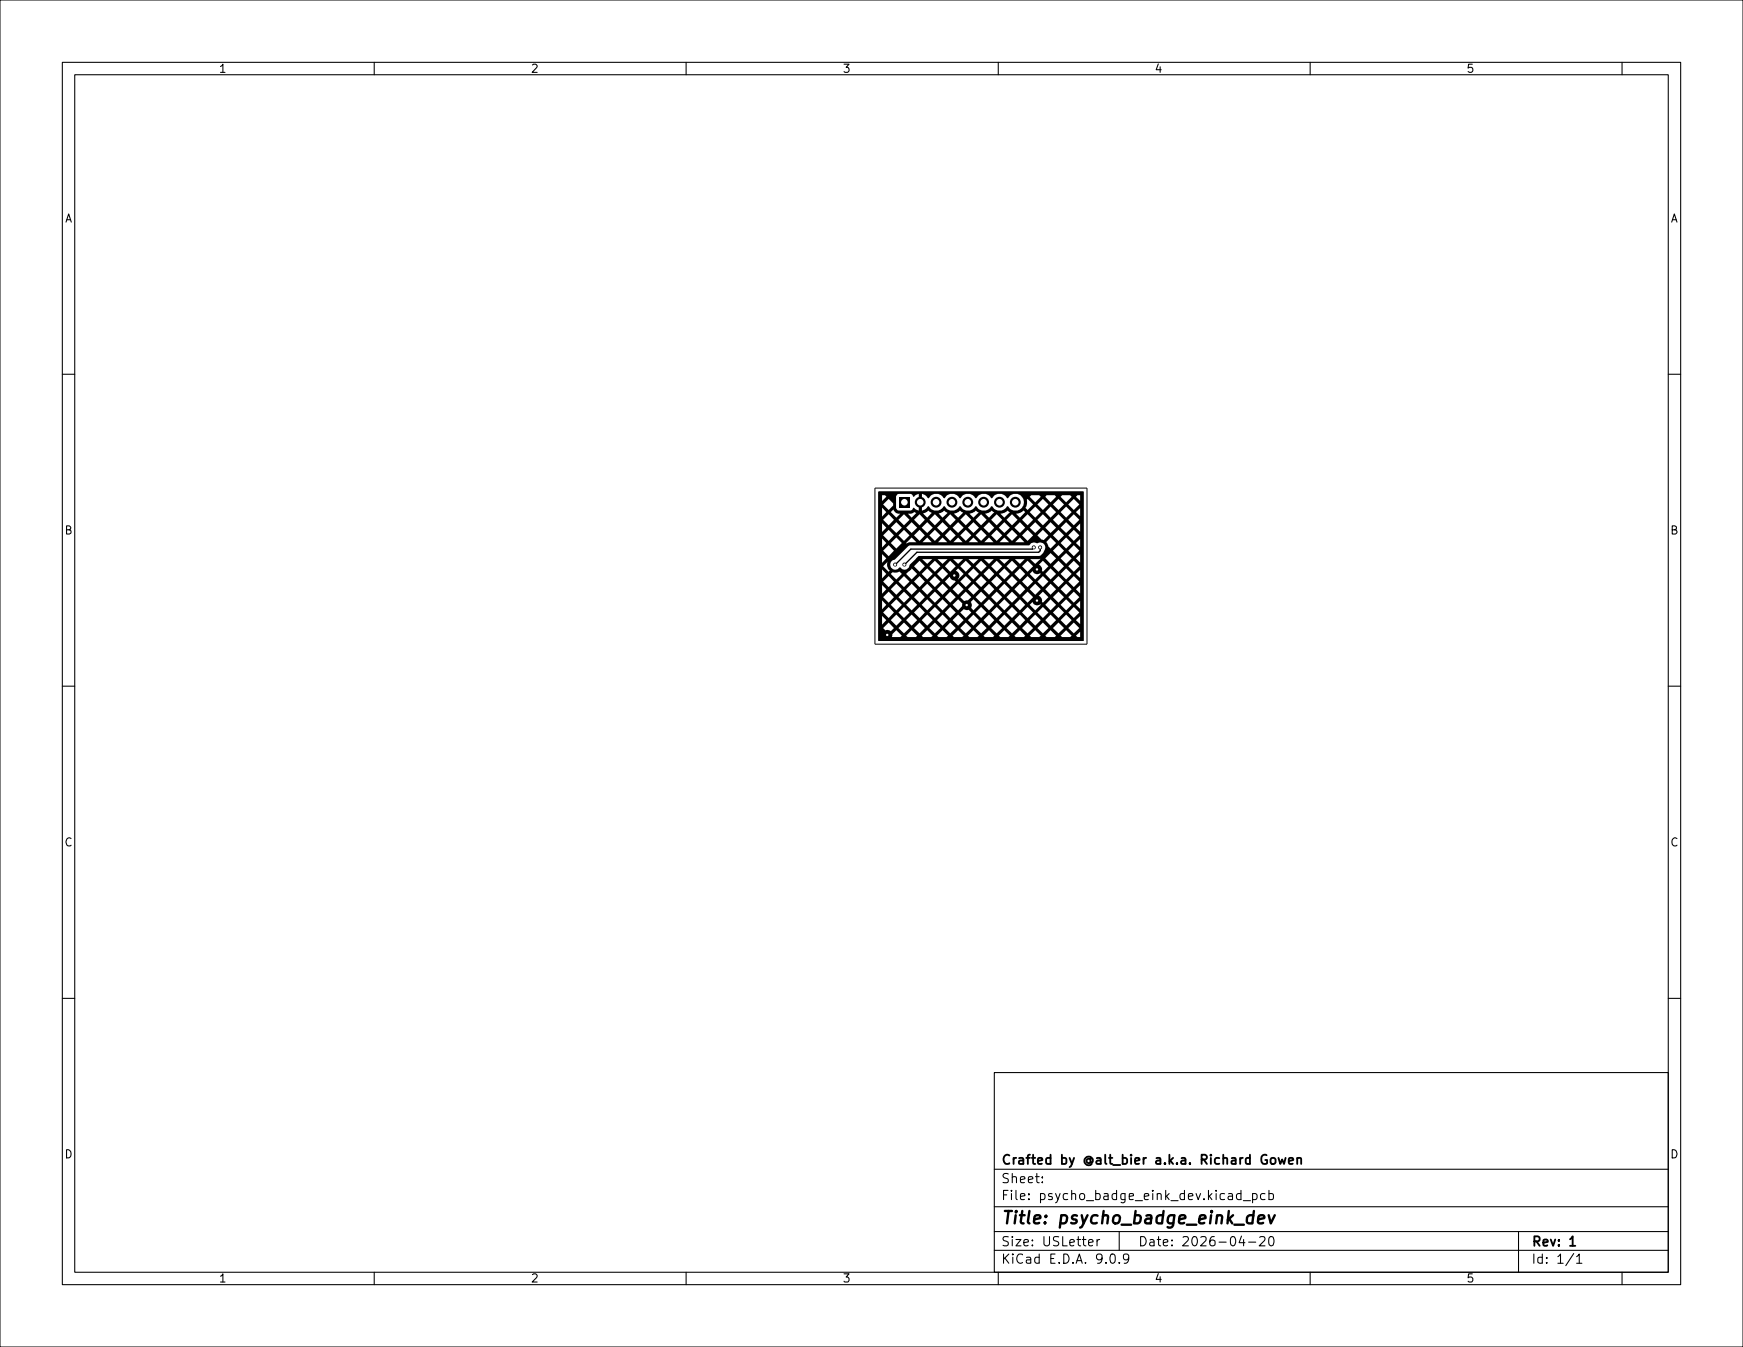
[picture p224: page 2]

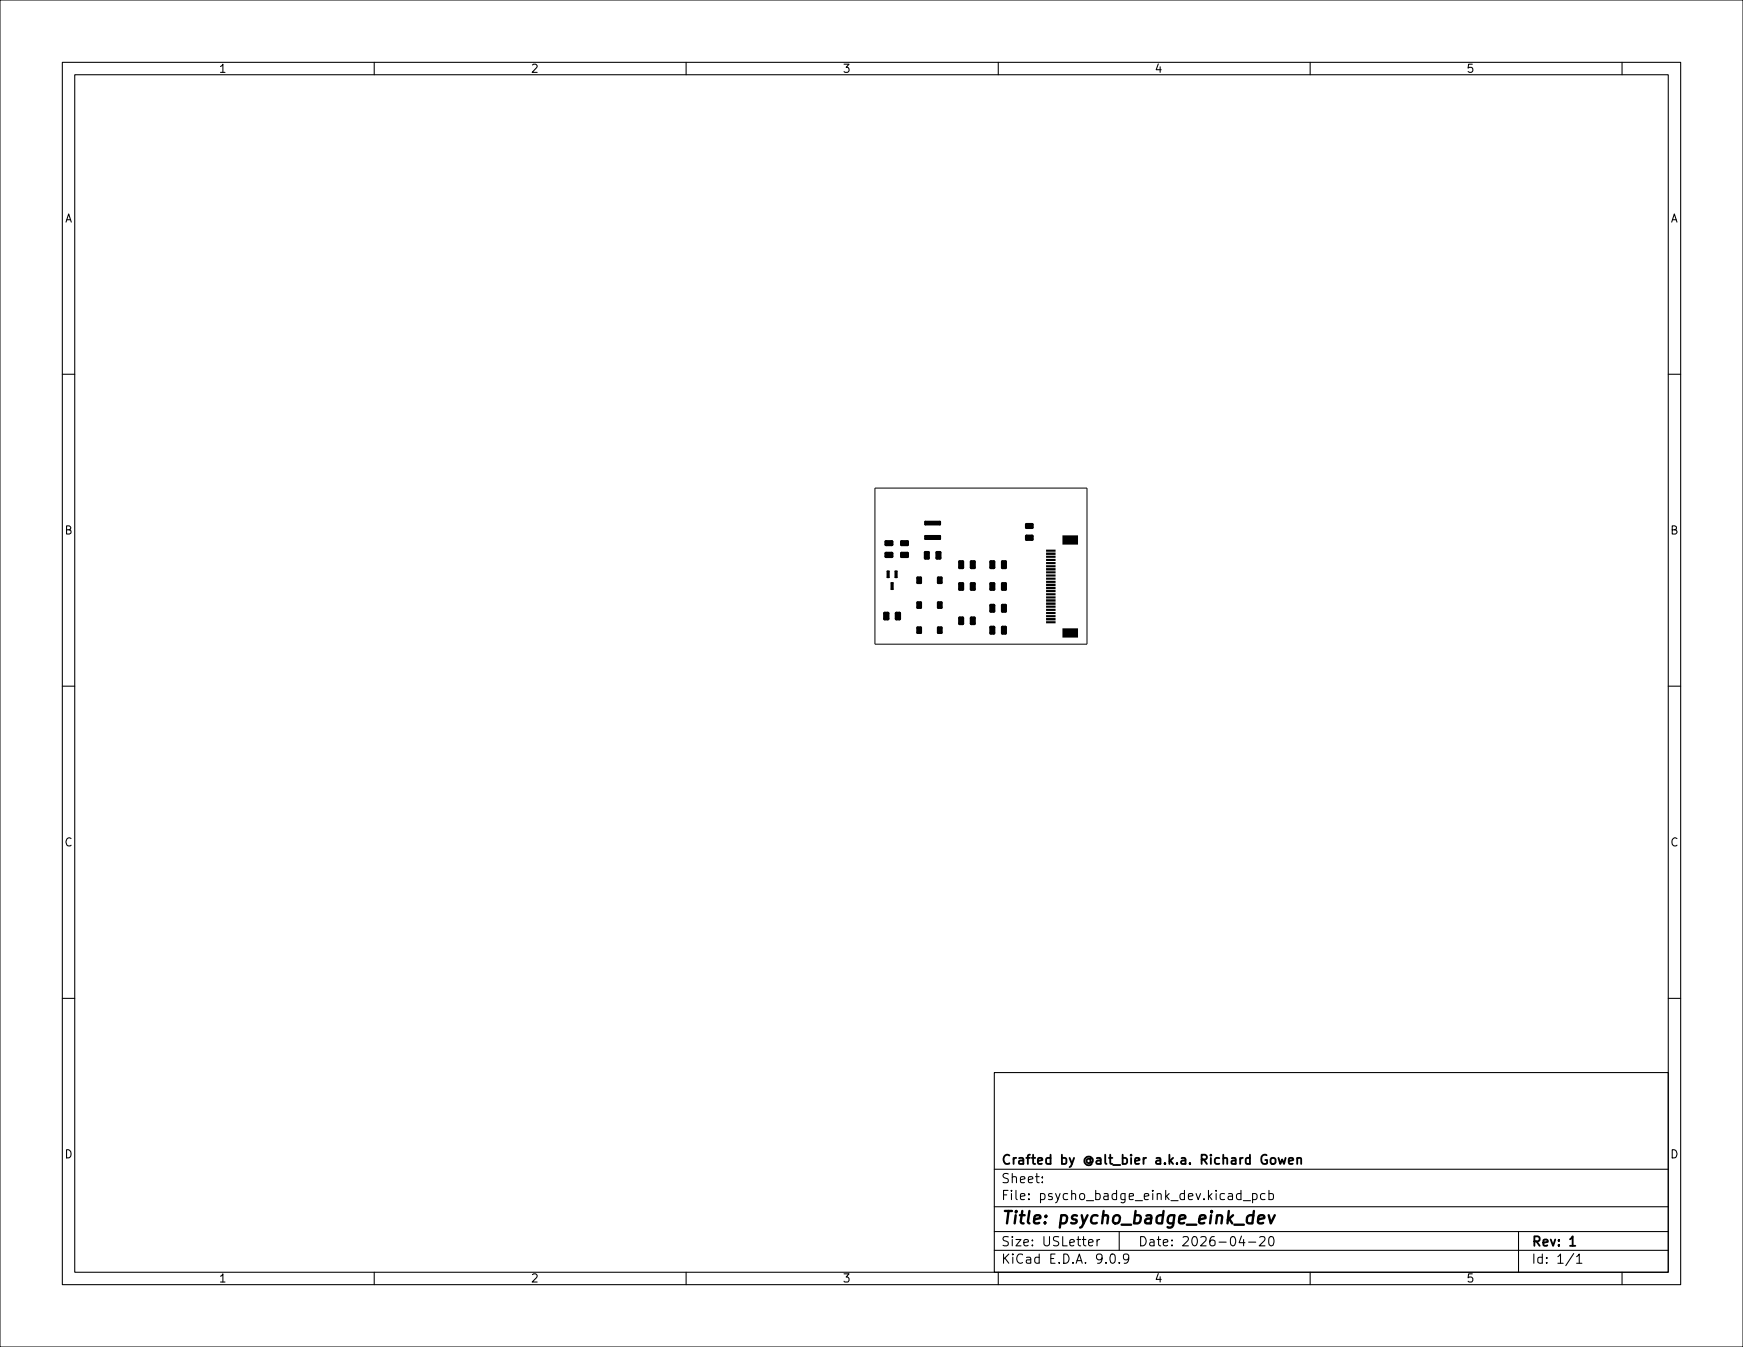
[picture p225: page 3]

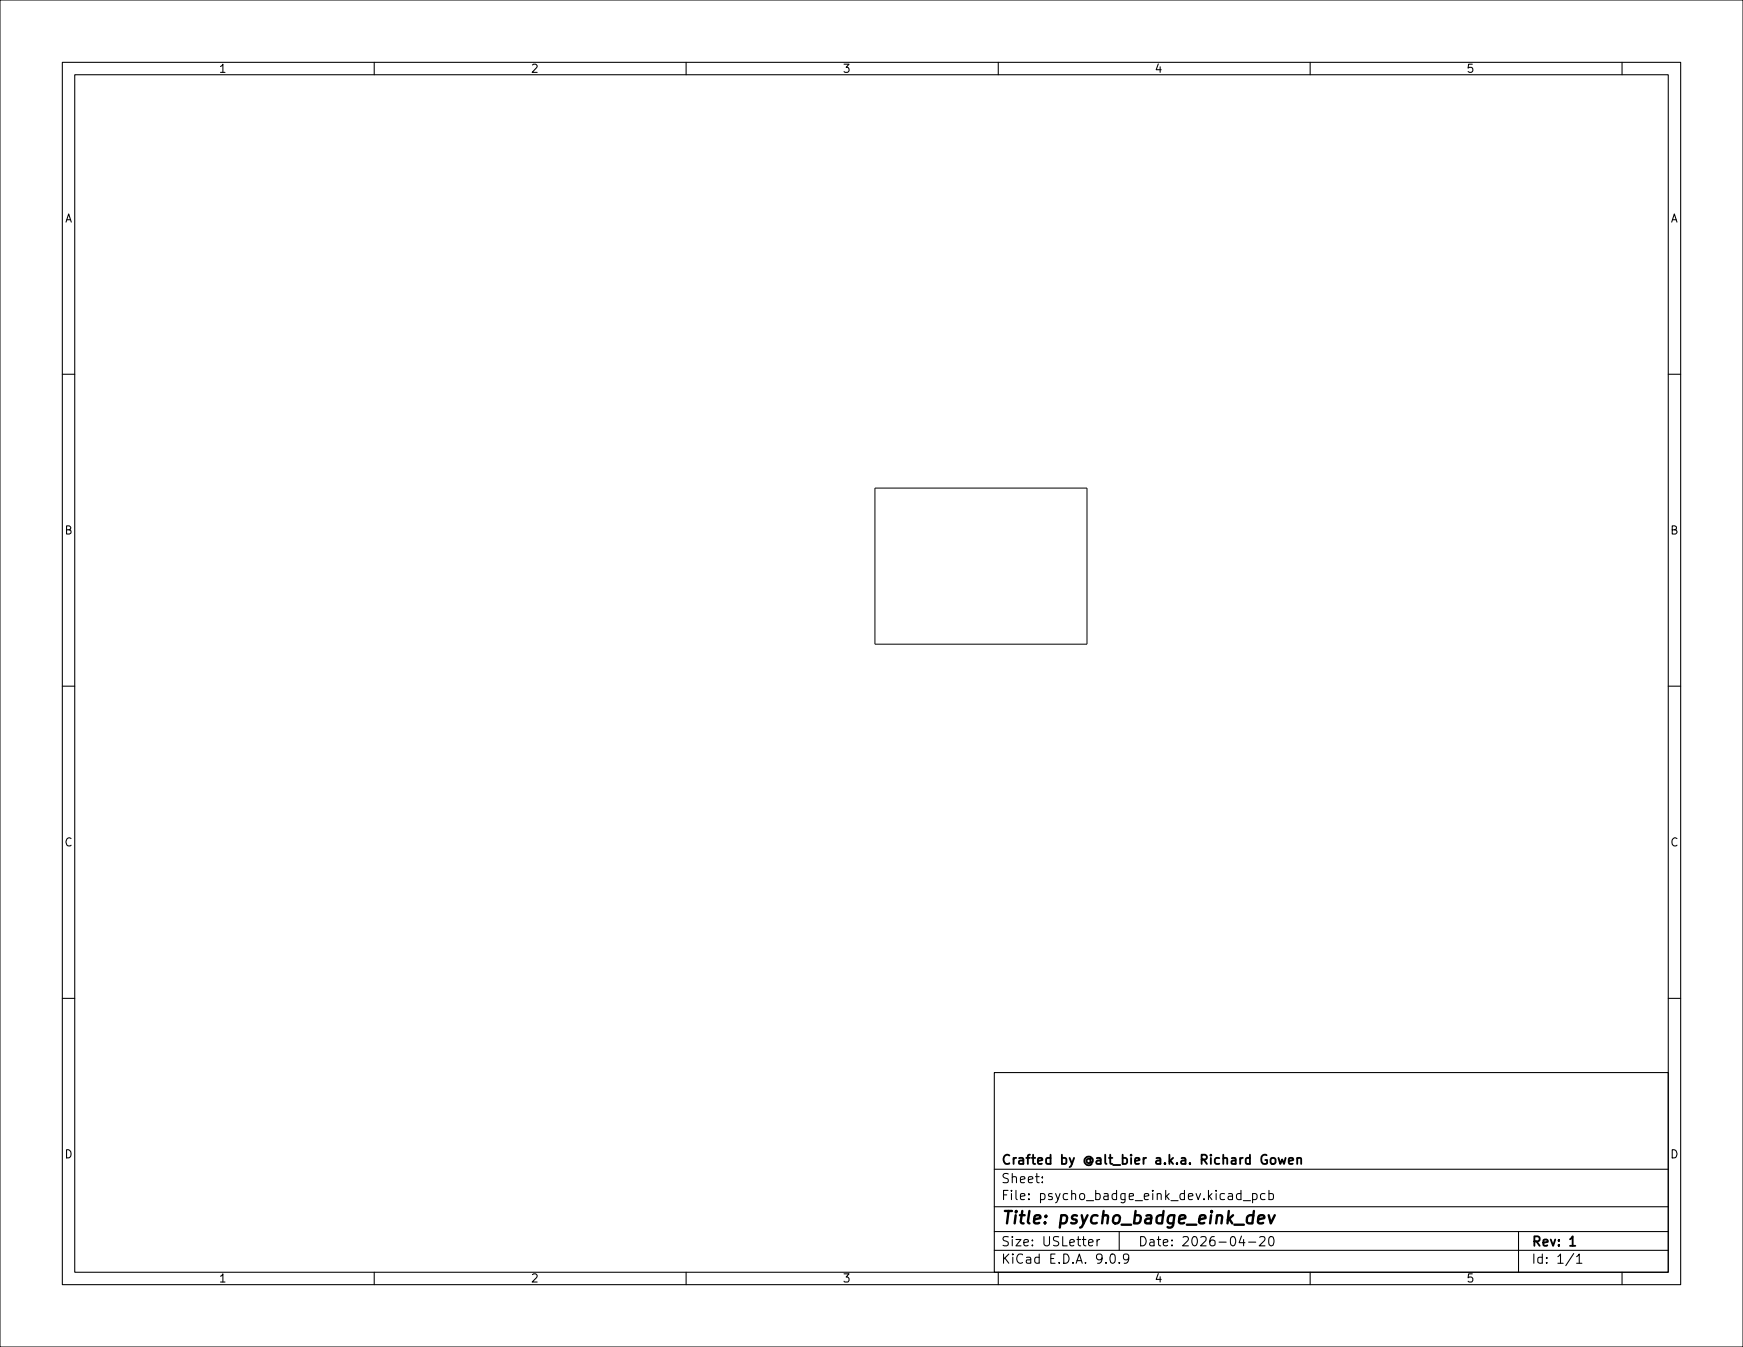
[picture p226: page 4]

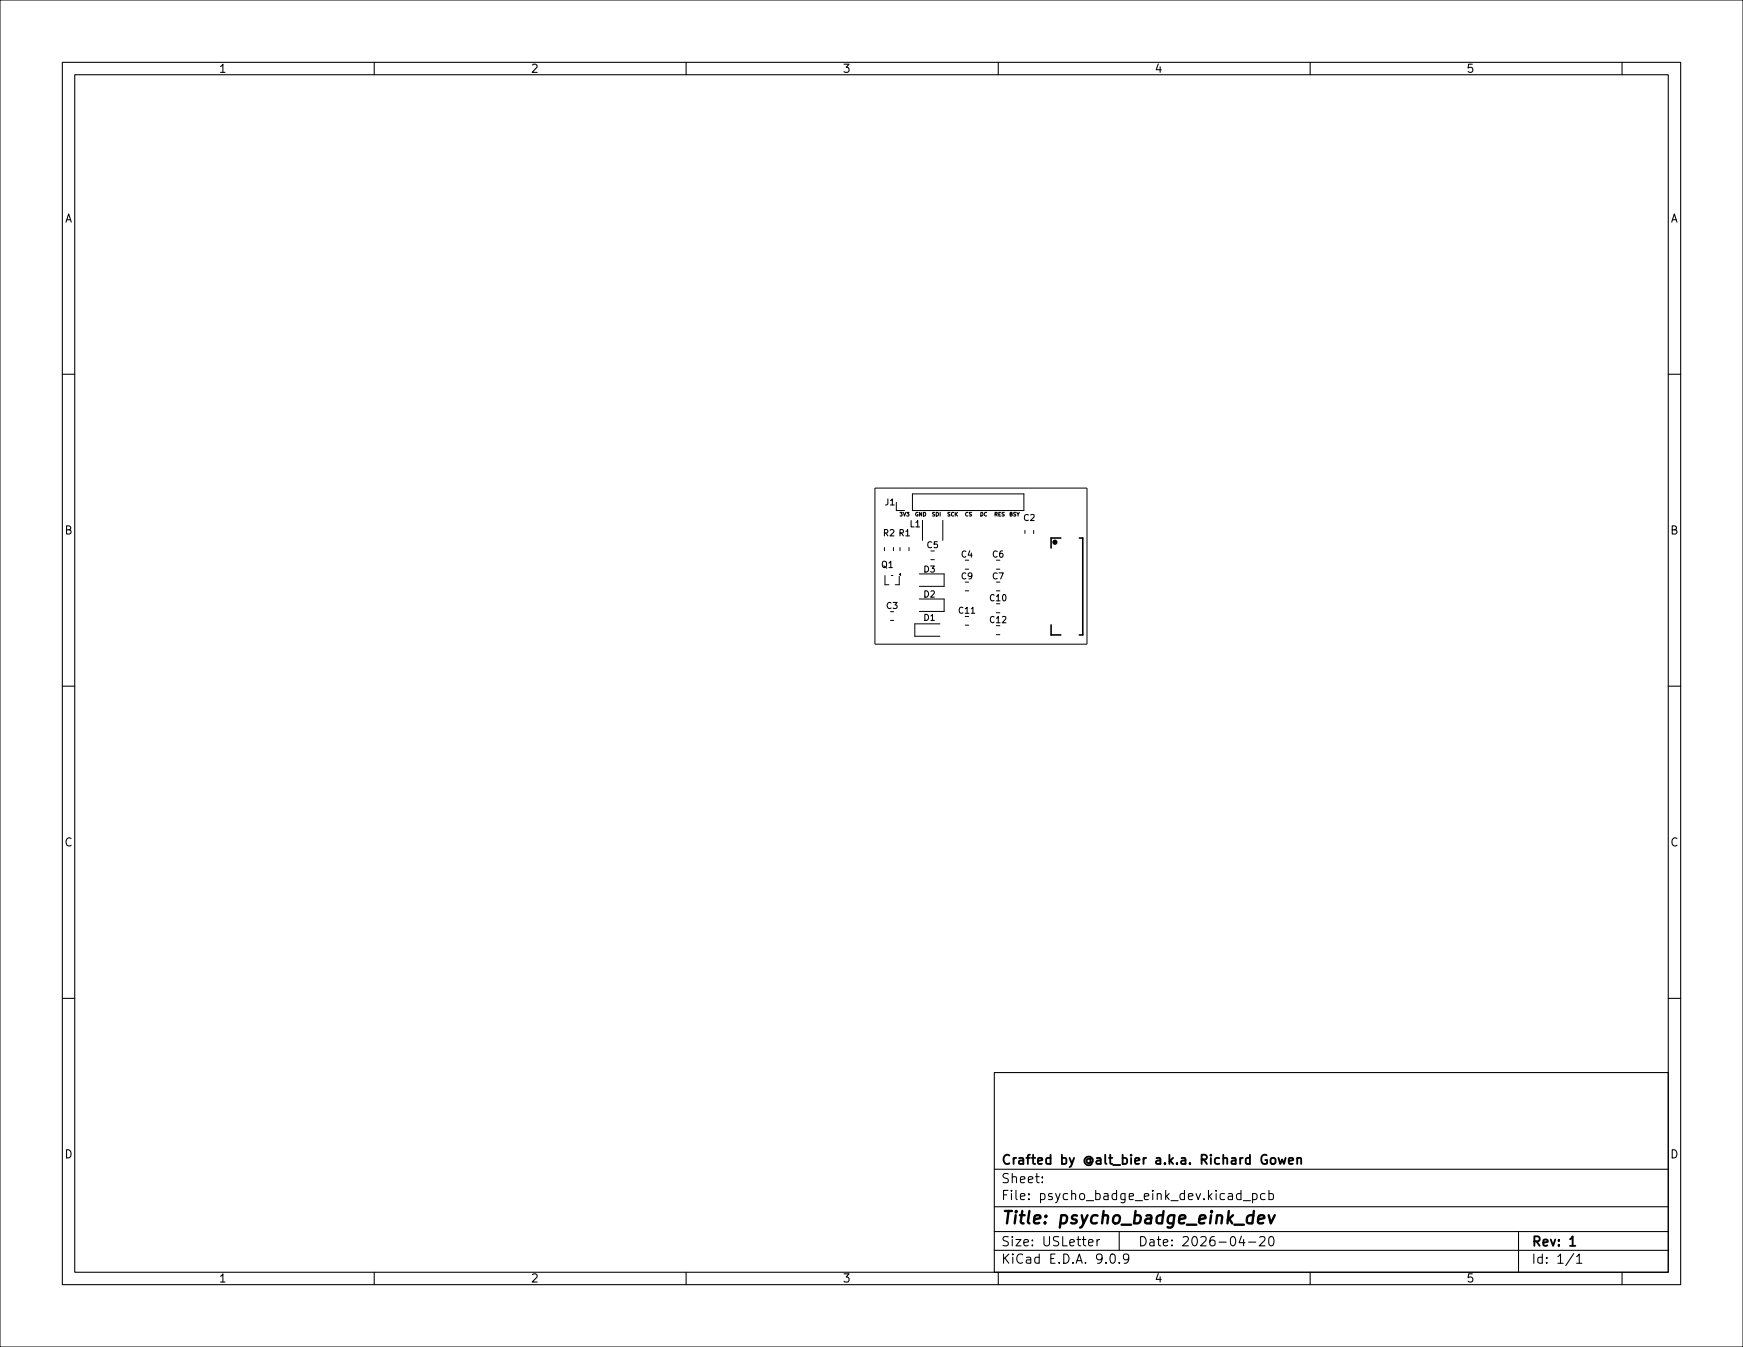
[picture p227: page 5]

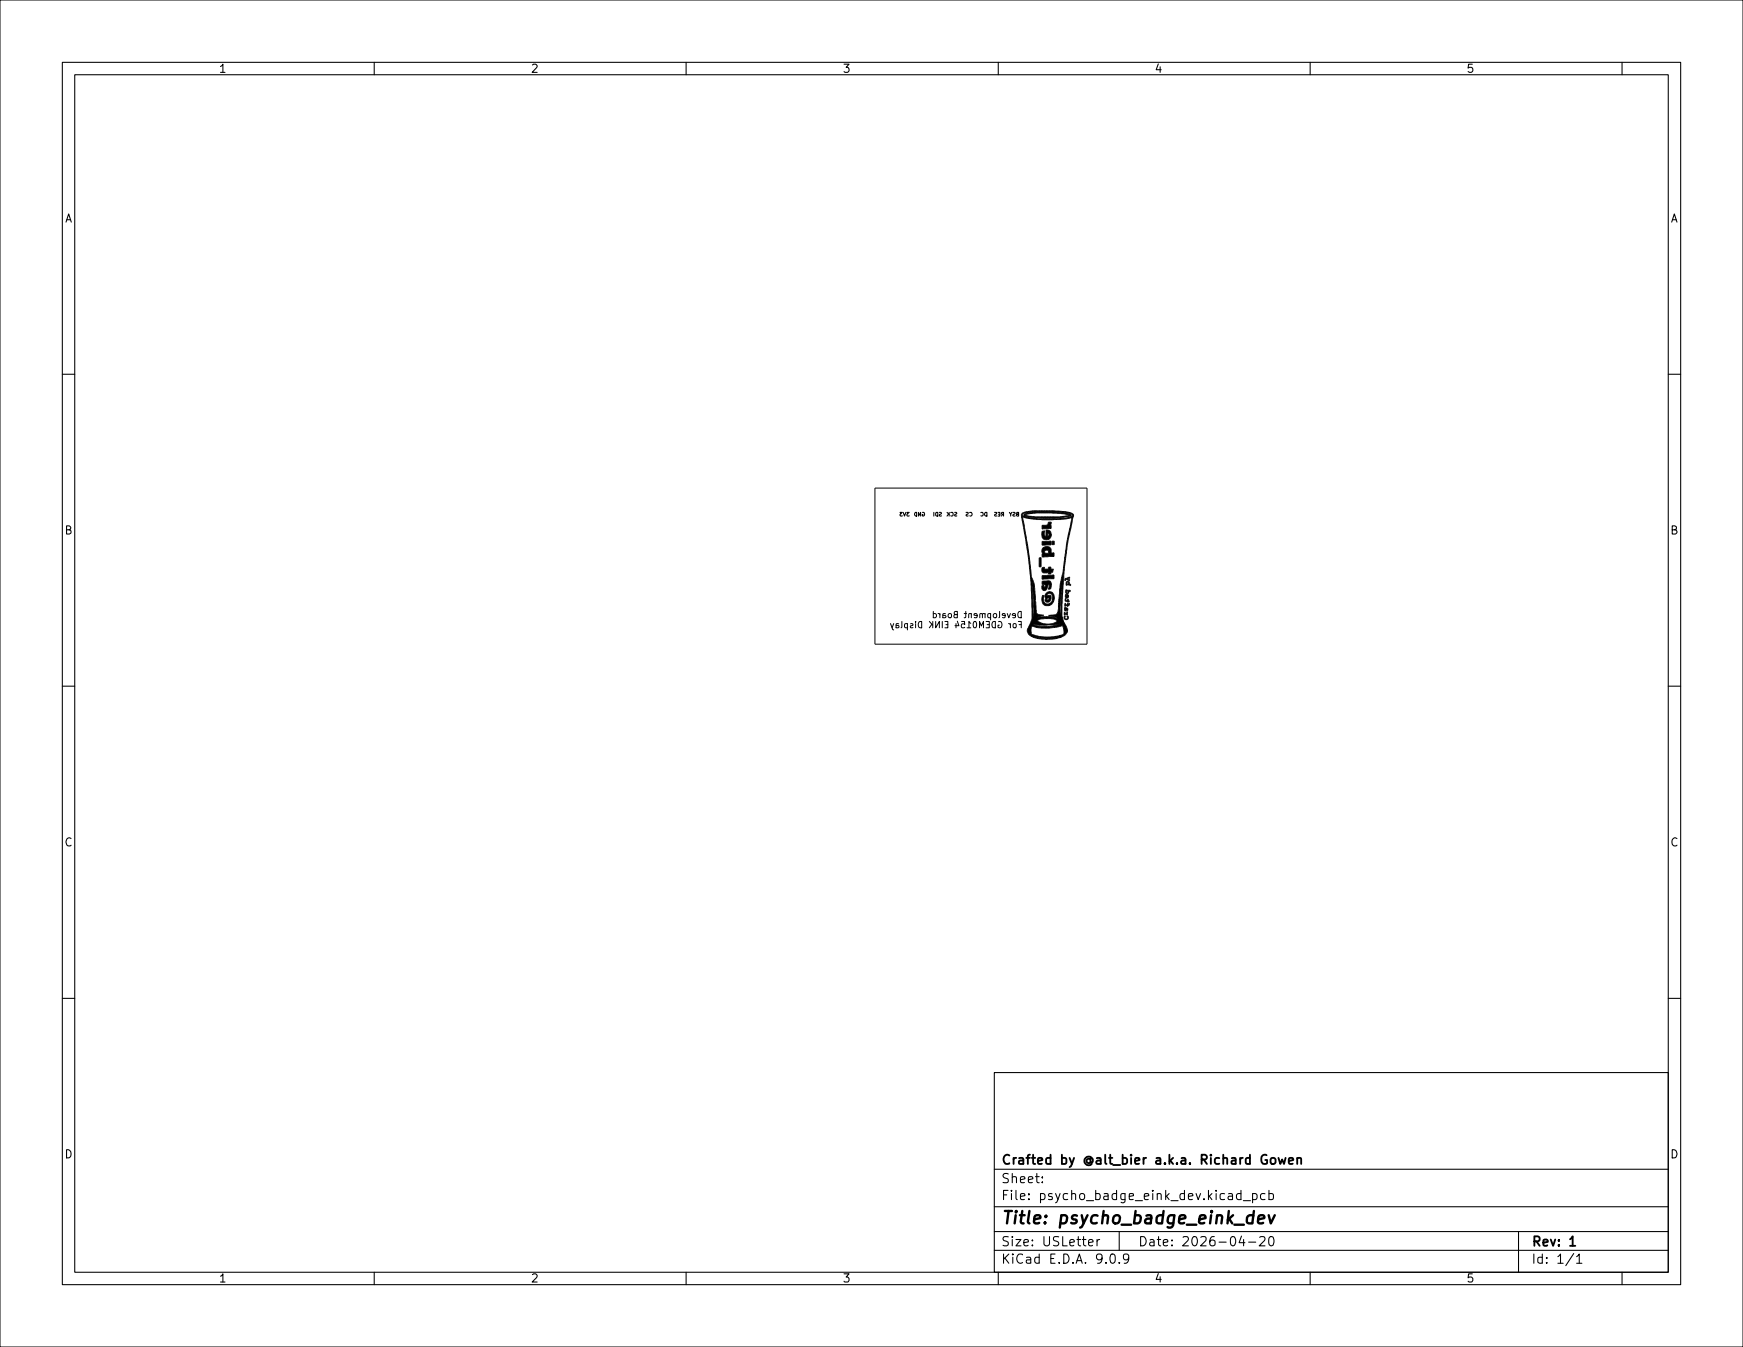
[picture p228: page 6]

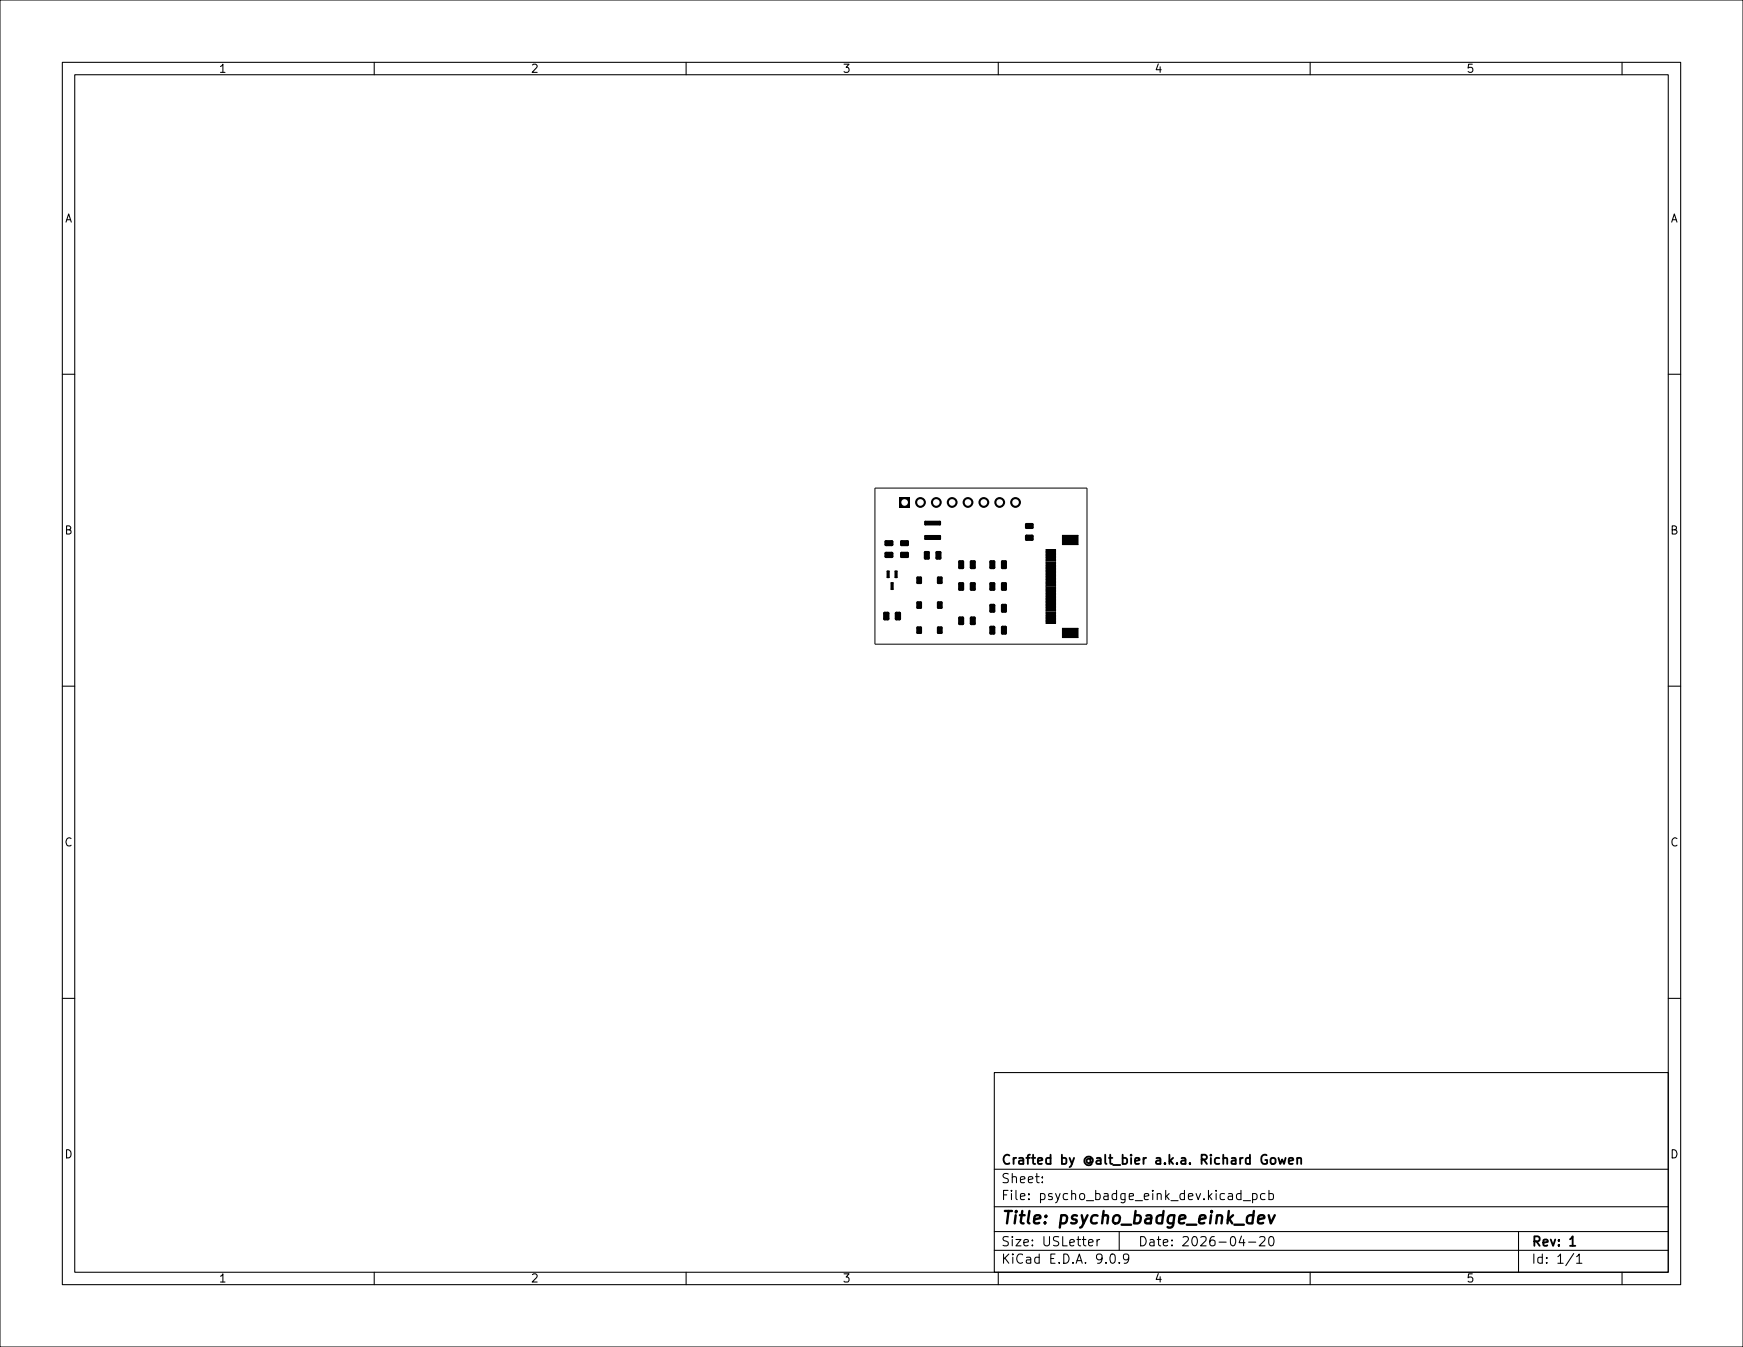
[picture p229: page 7]

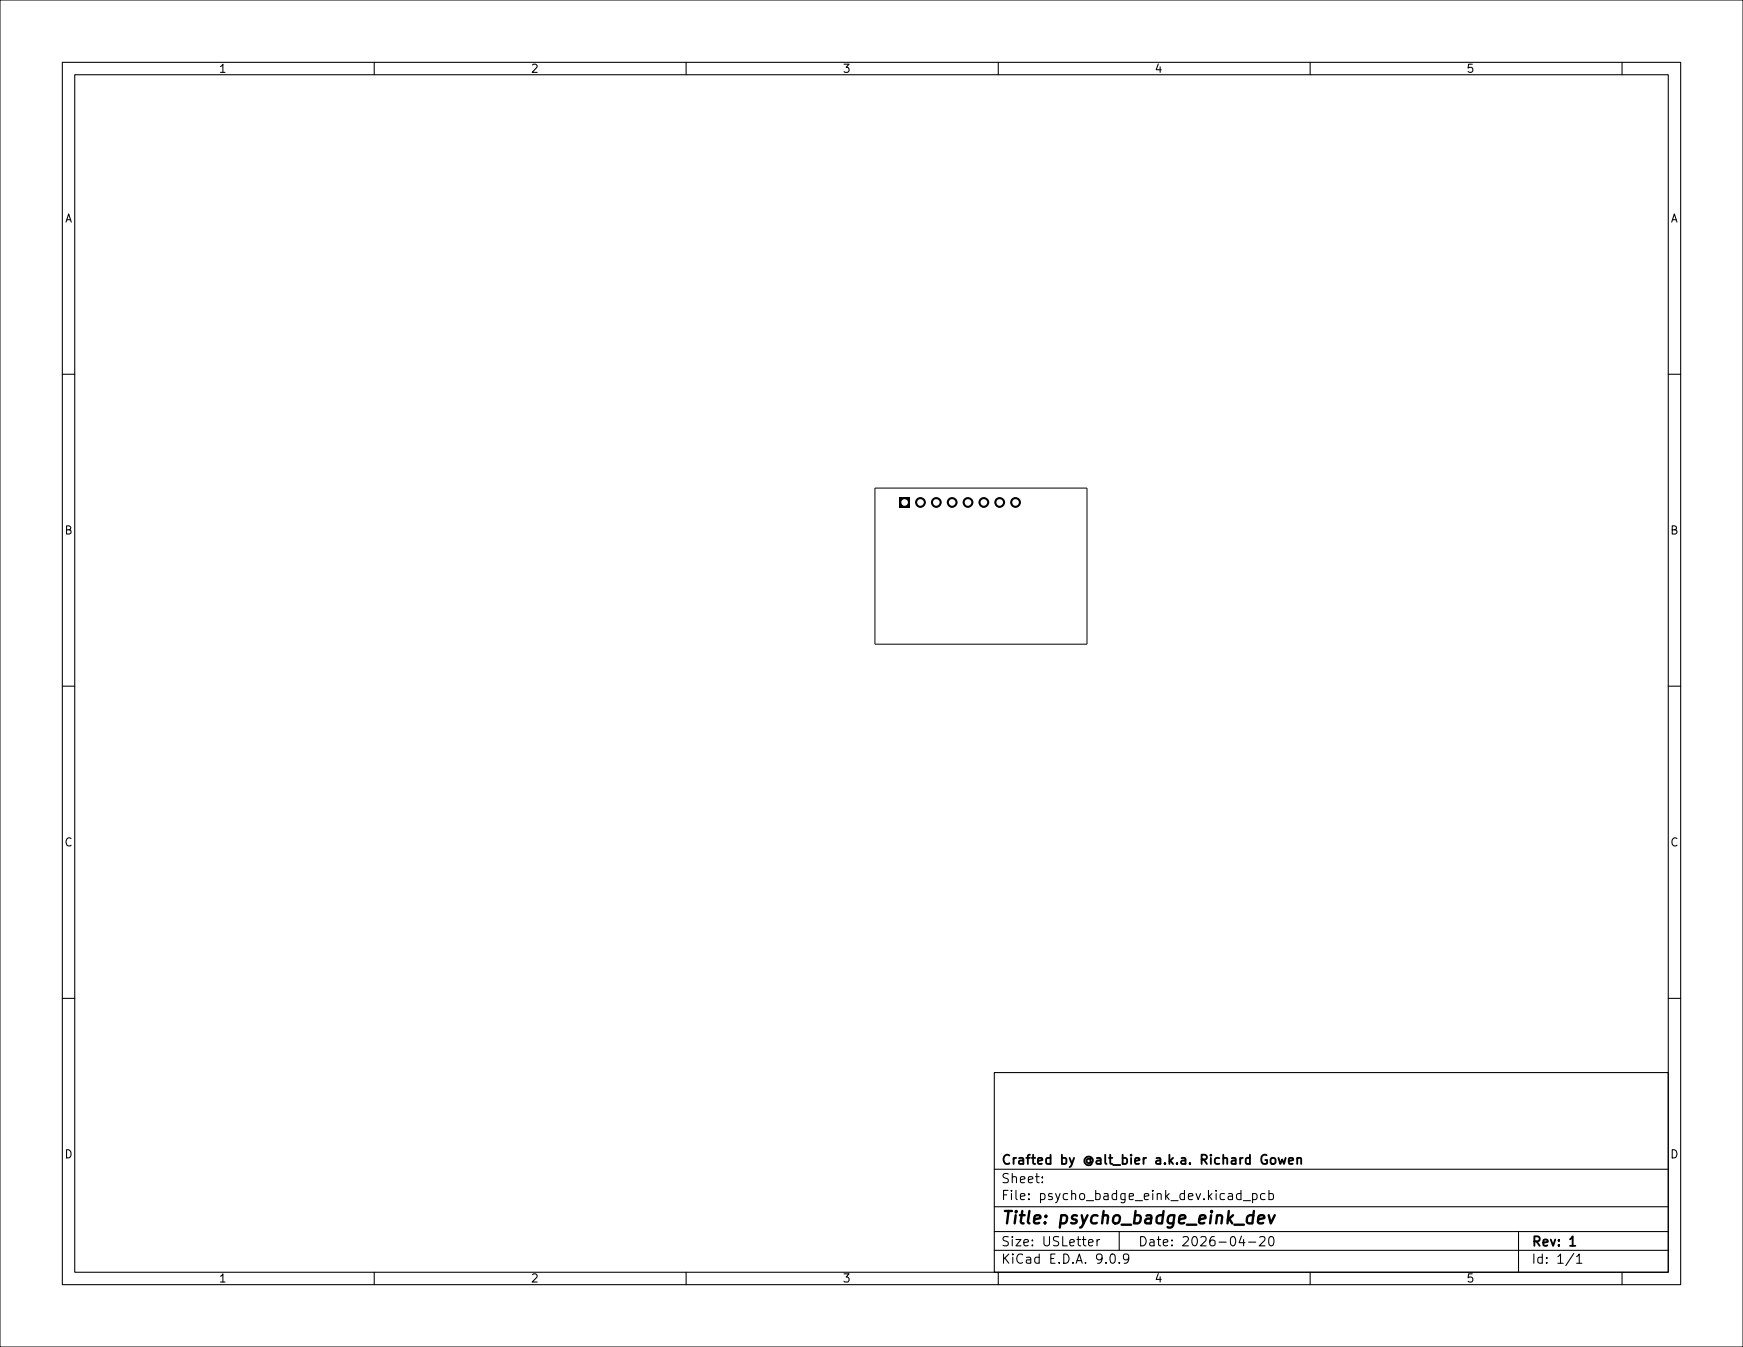
[picture p230: page 8]
