gowenrw/psycho_badge/eda/psycho_badge/snapshots/psycho_badge_pcb_rev1.pdf

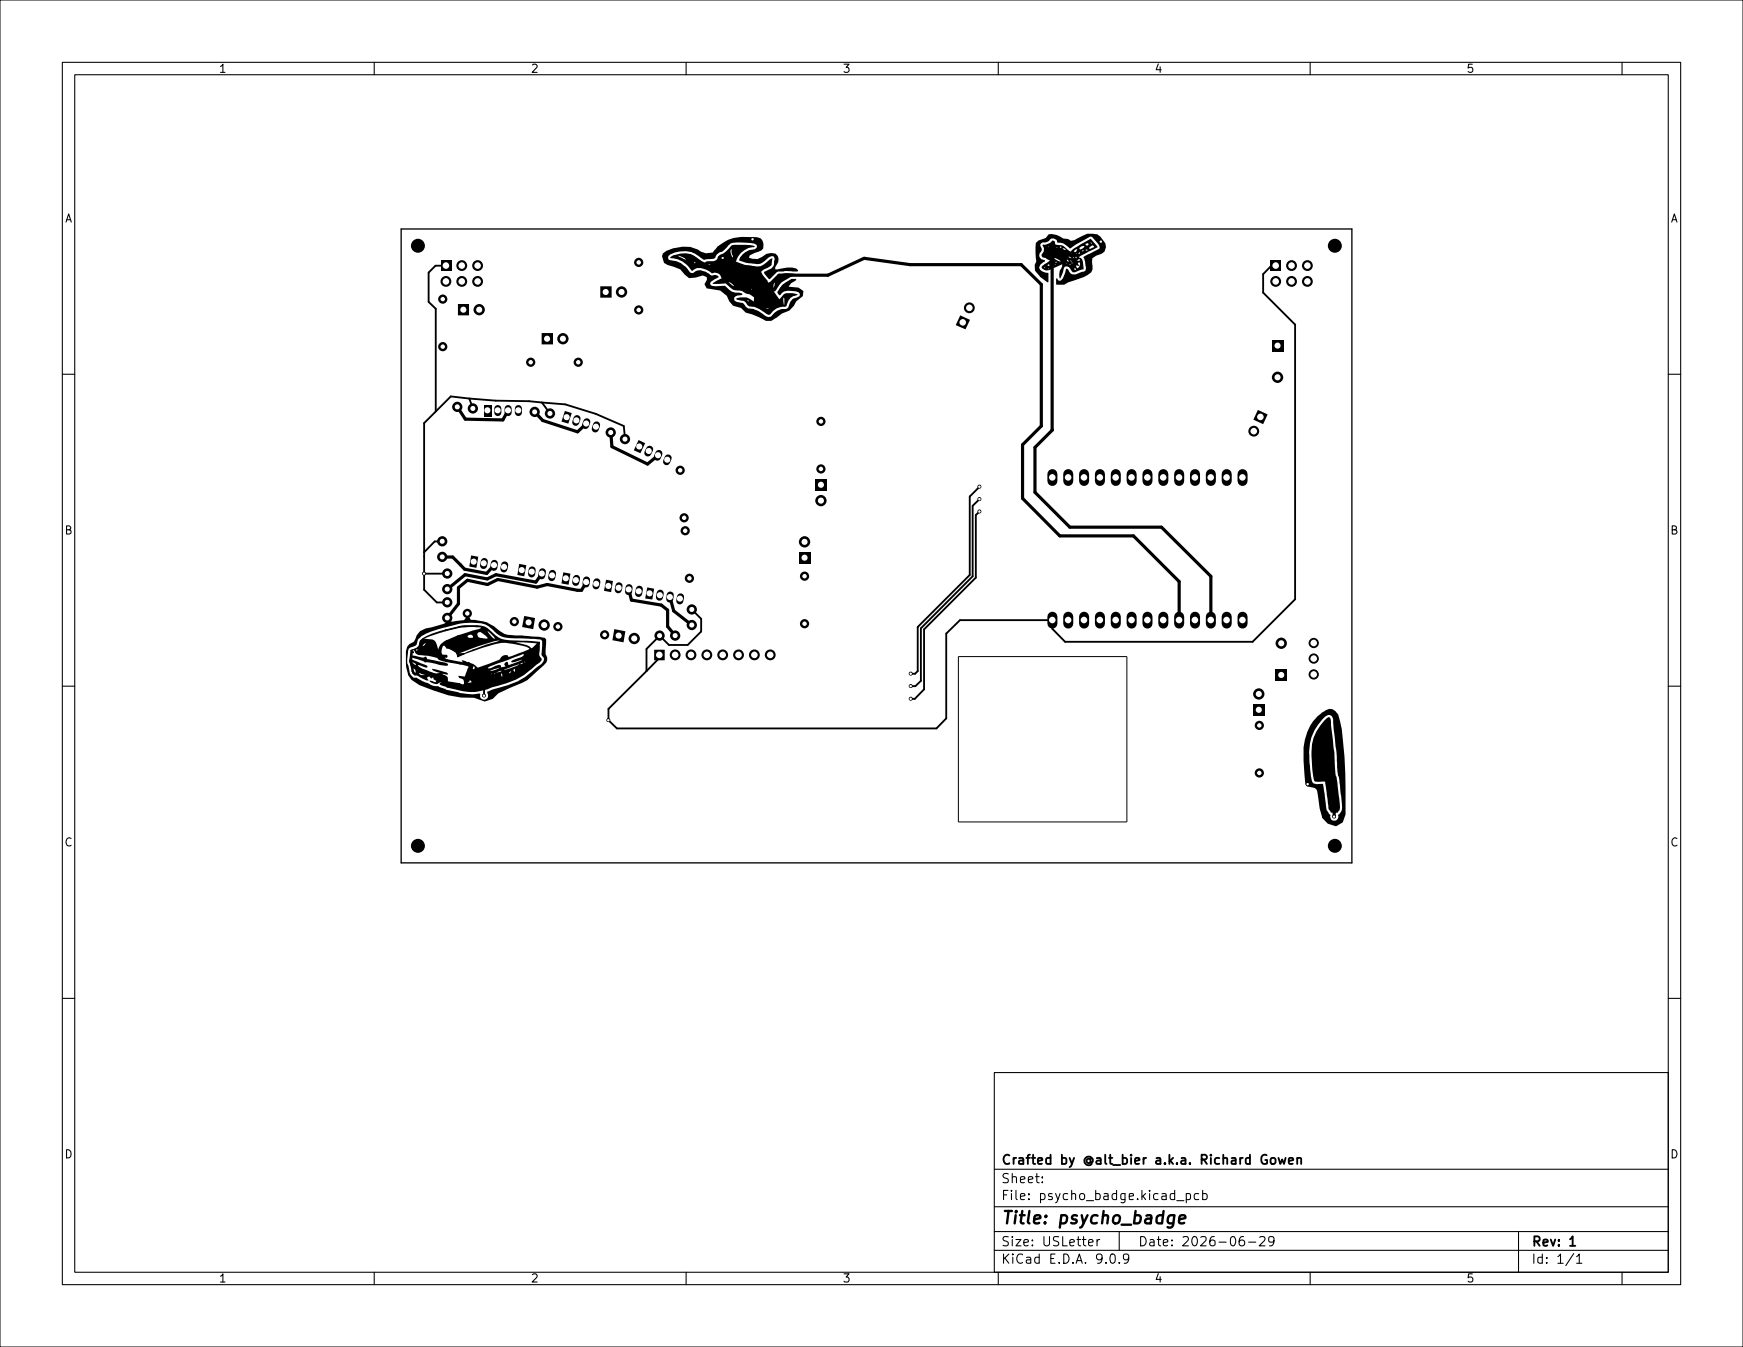
[picture p231: page 1]

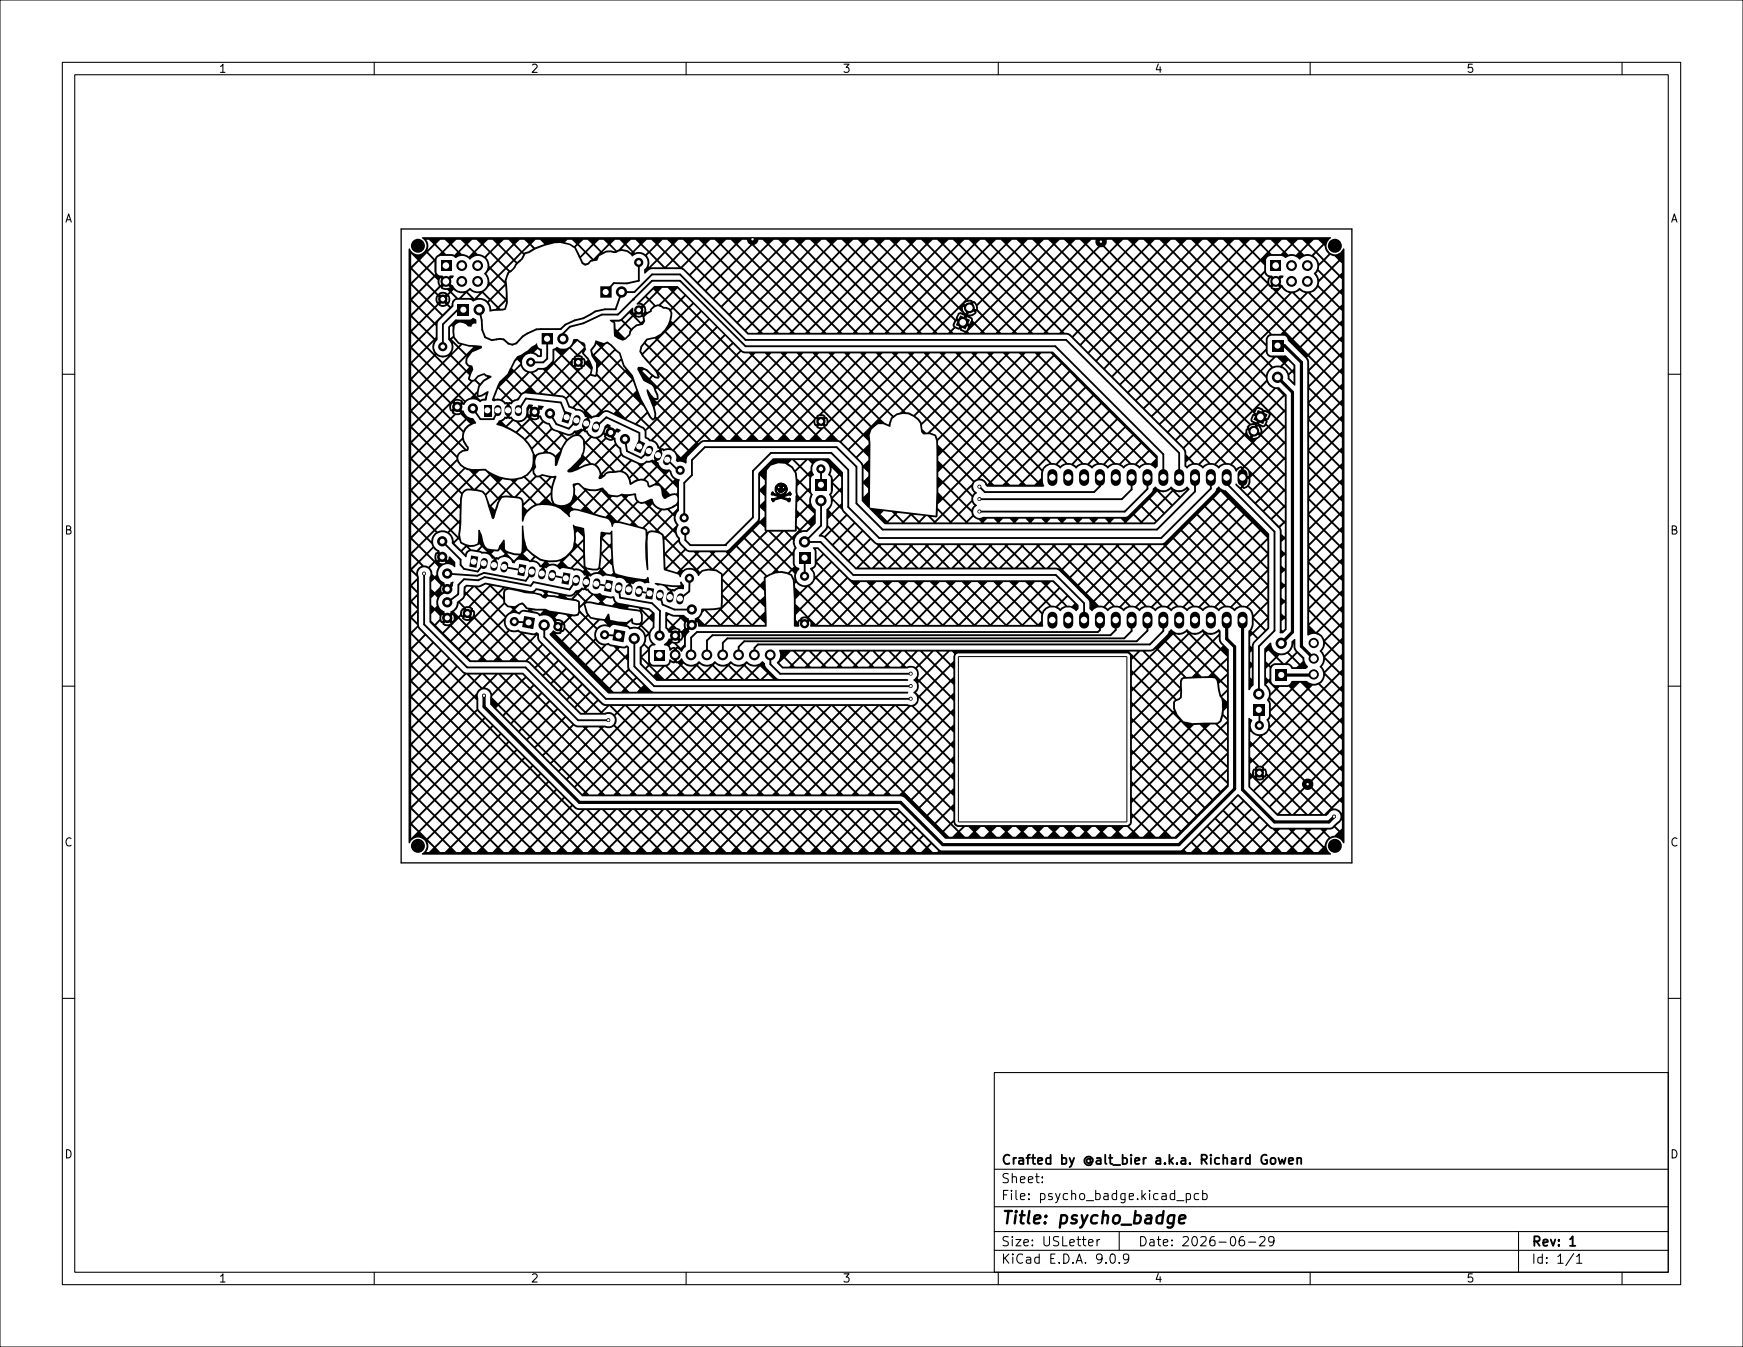
[picture p232: page 2]

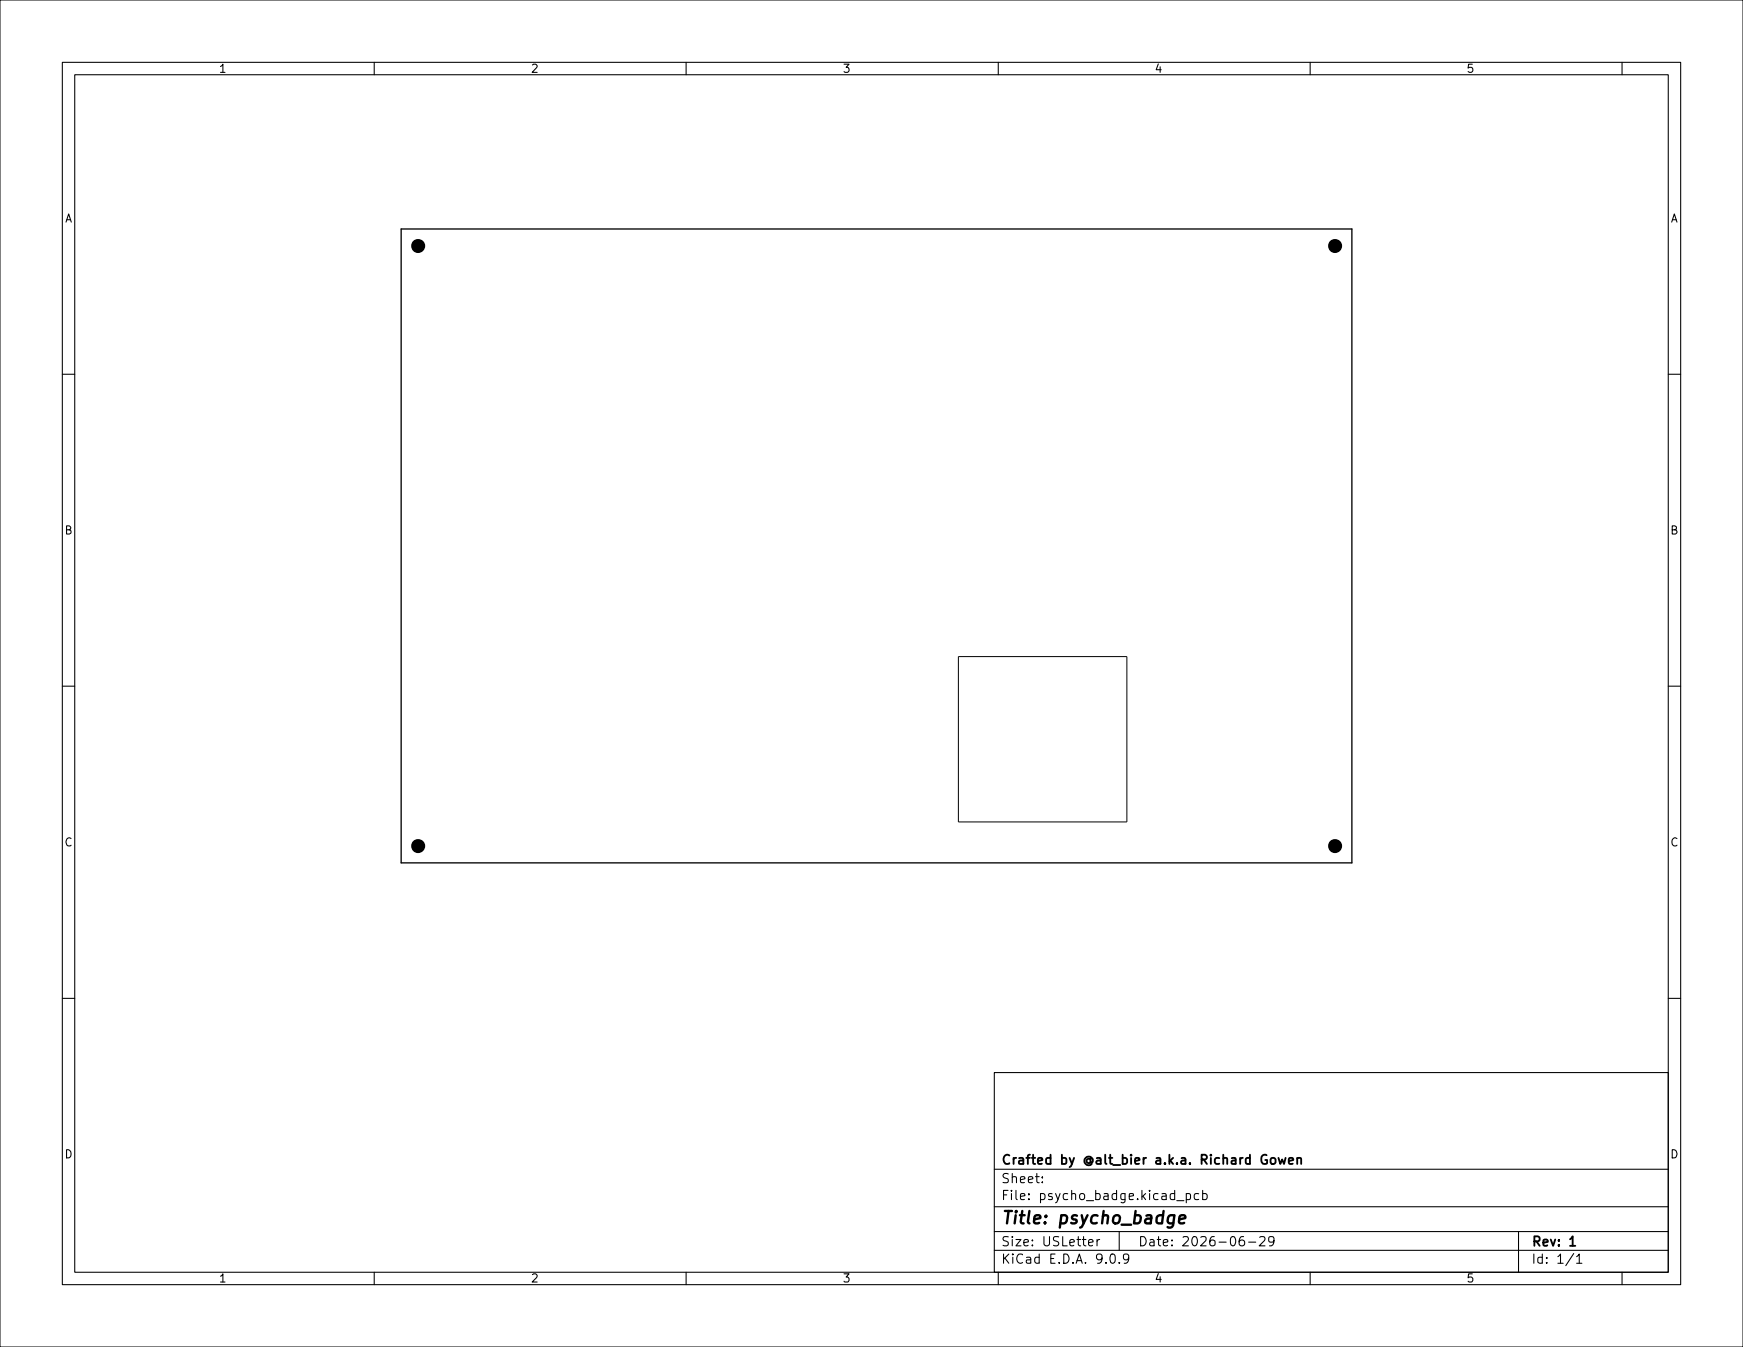
[picture p233: page 3]

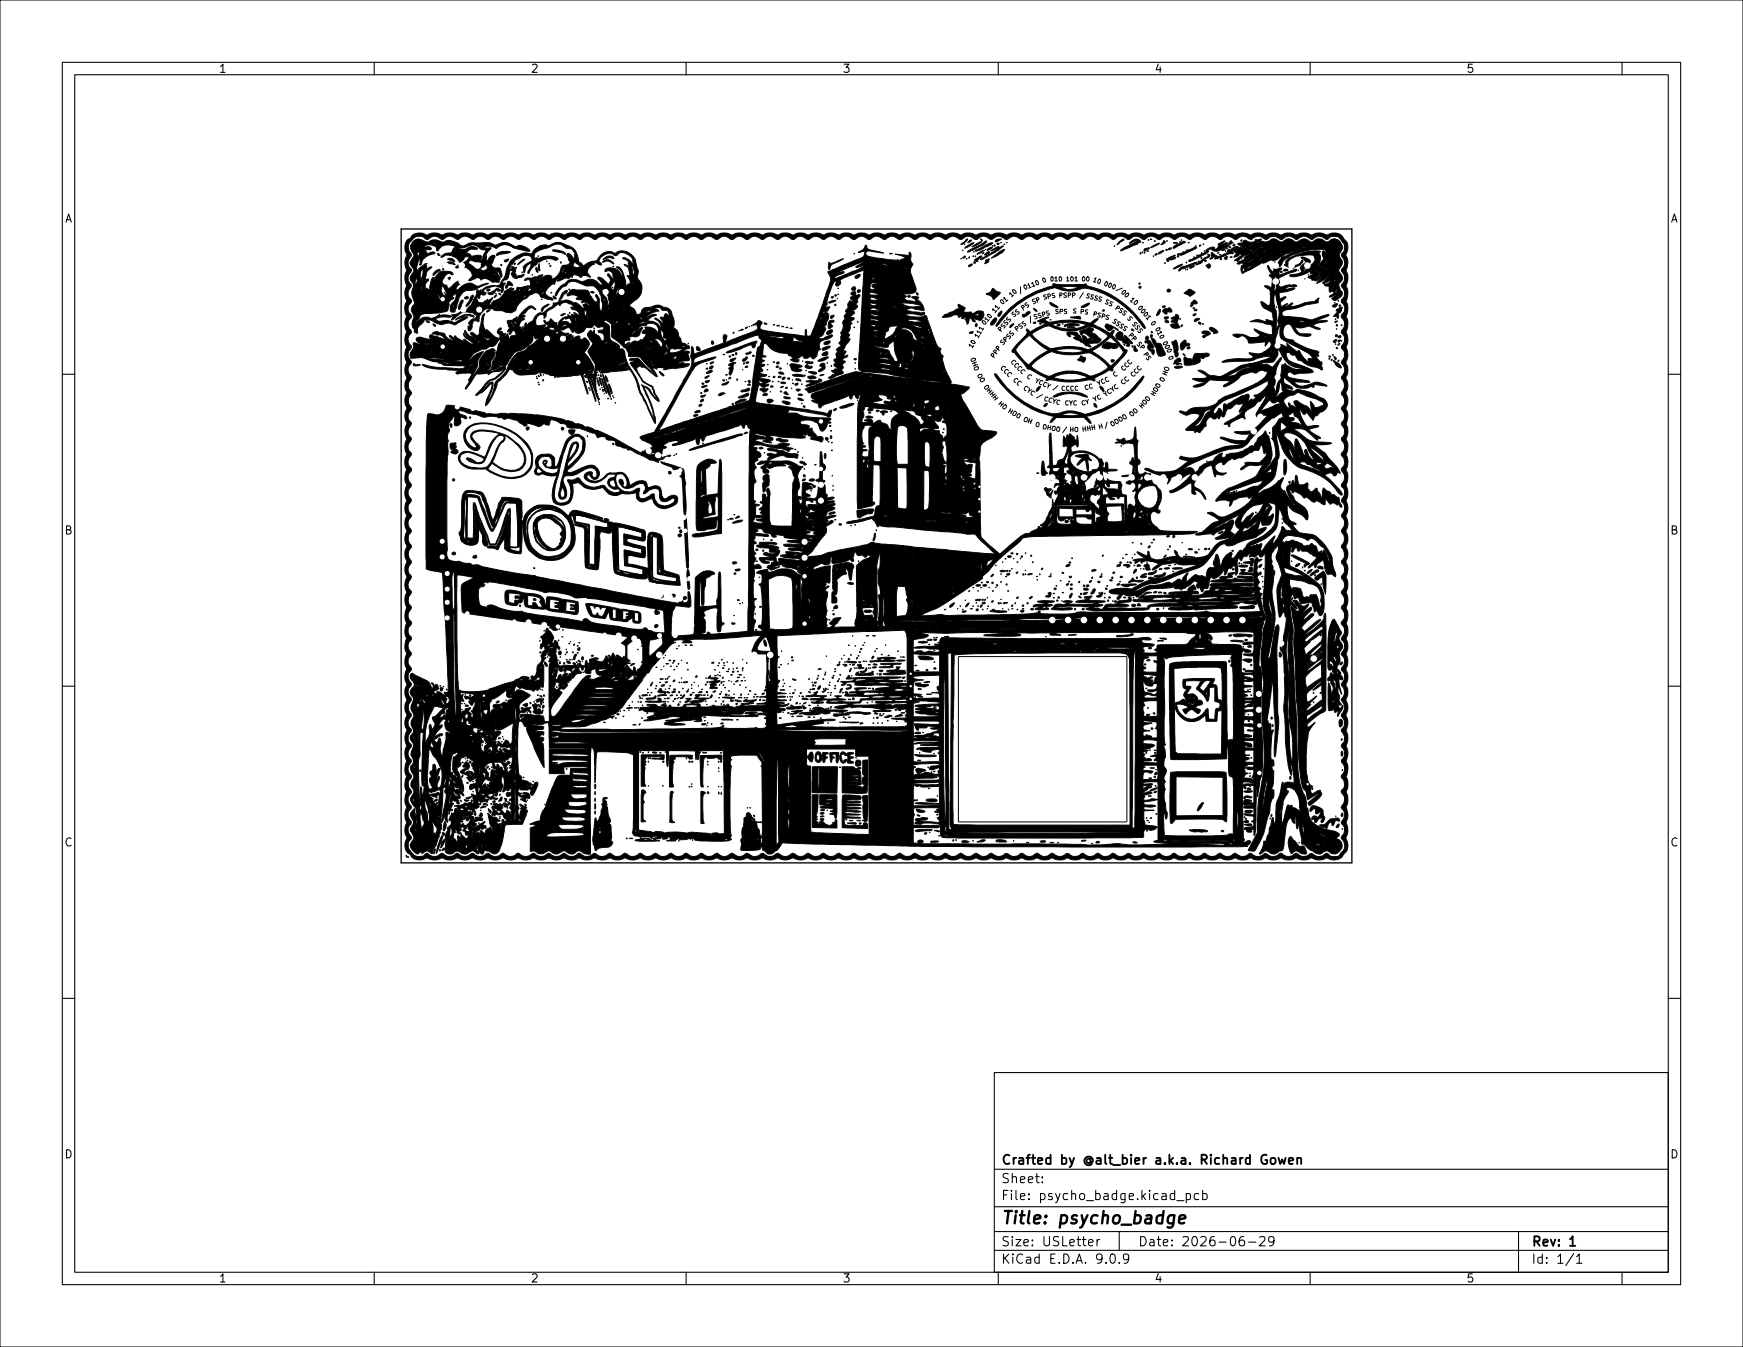
[picture p234: page 5]

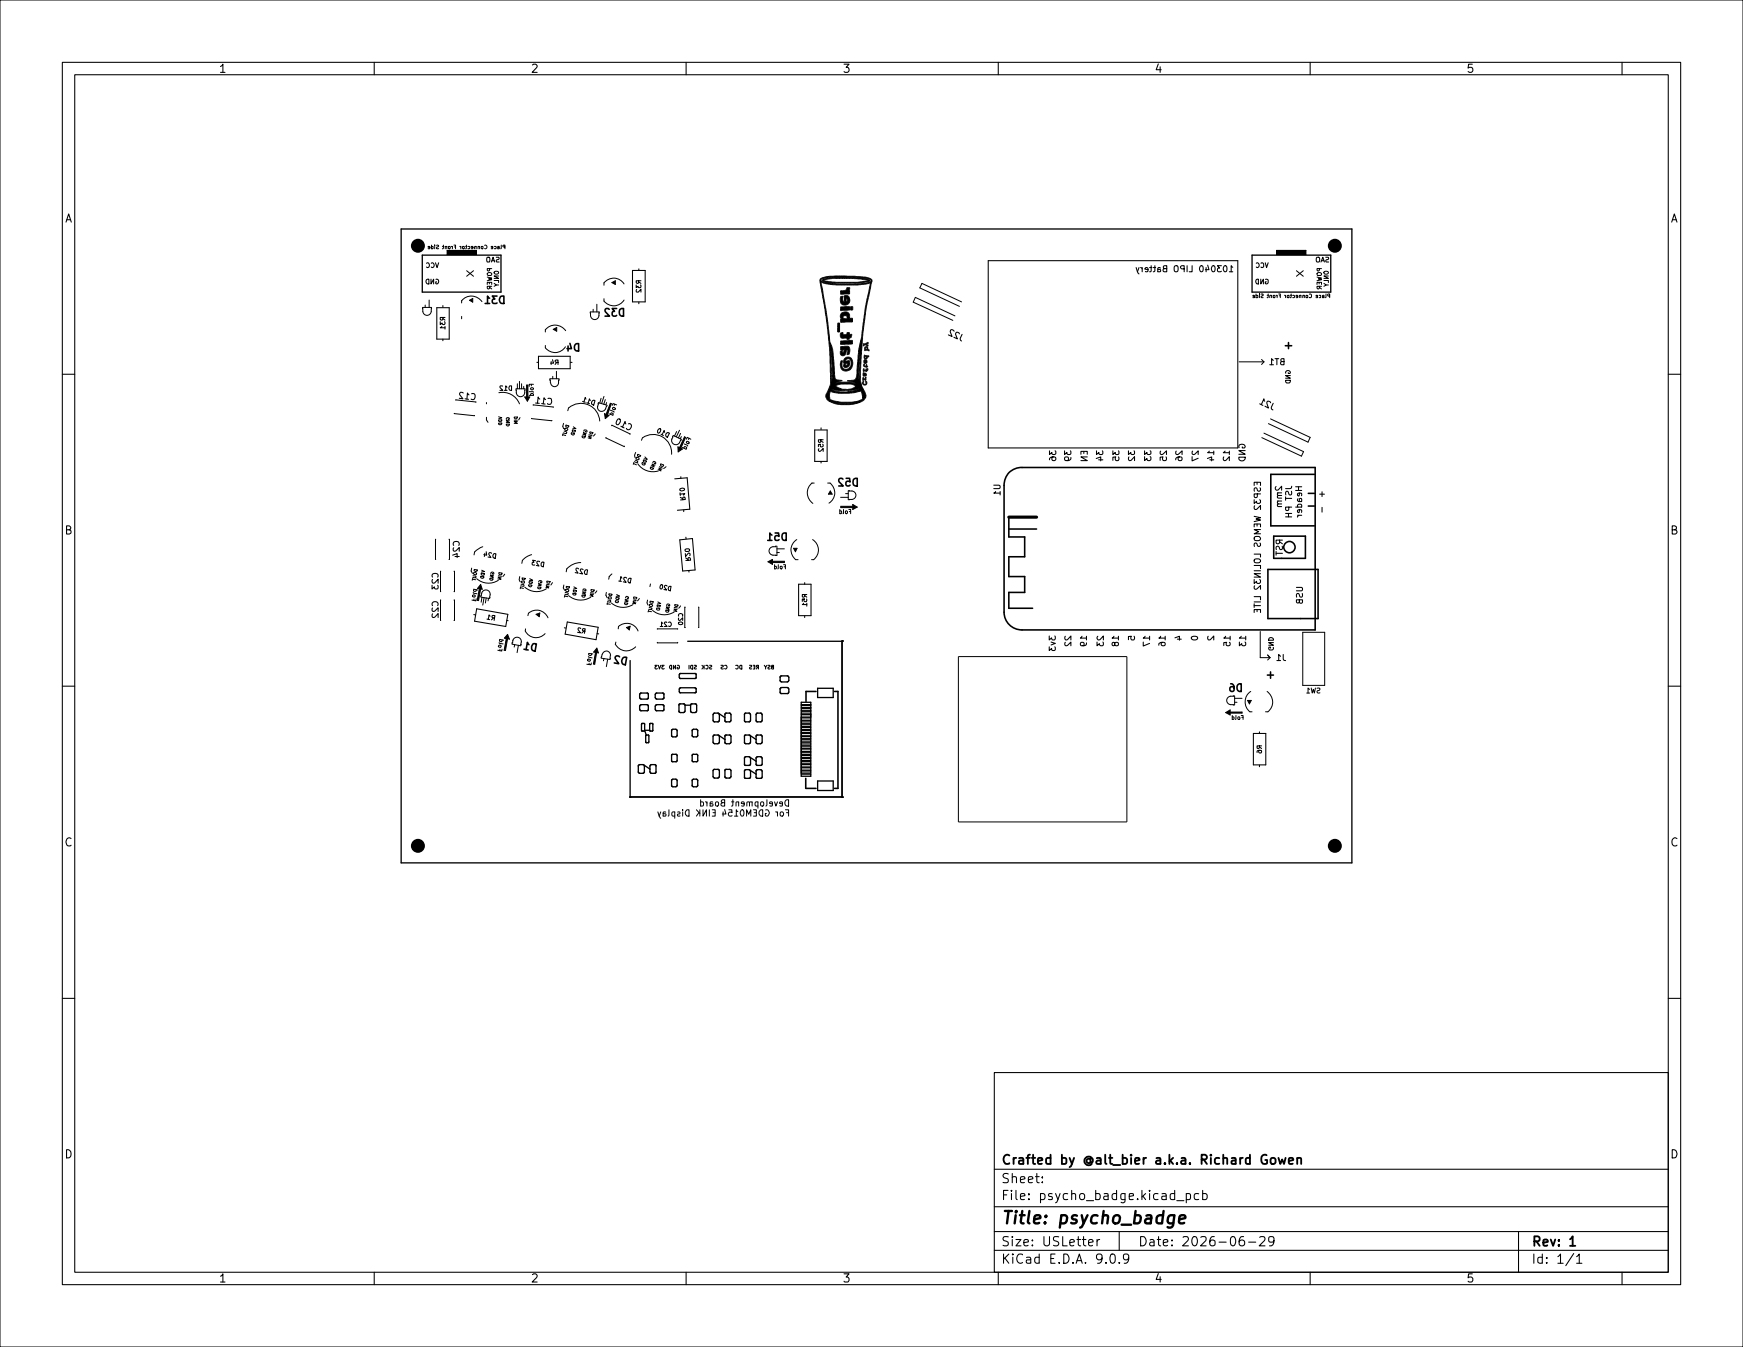
[picture p235: page 6]

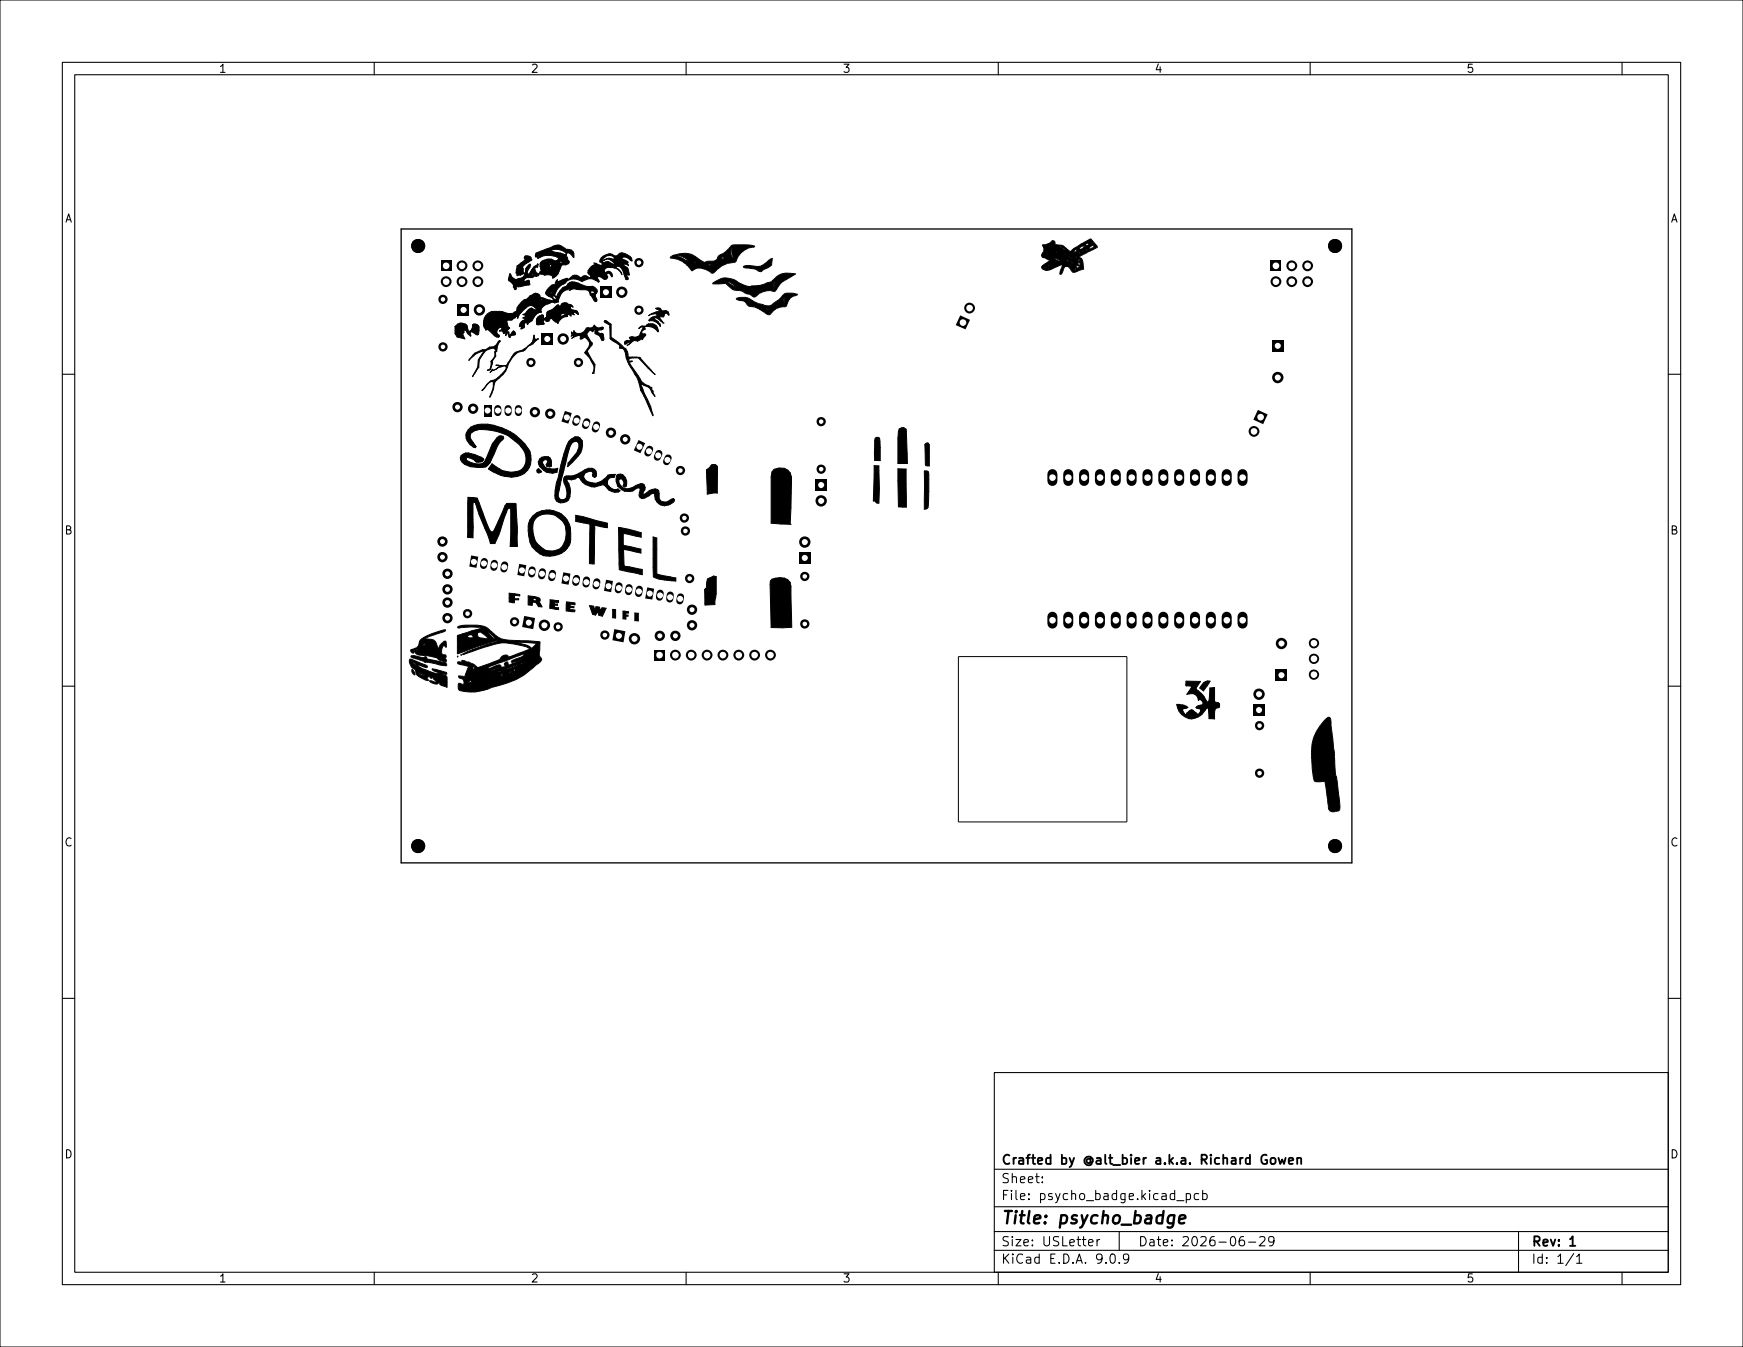
[picture p236: page 7]

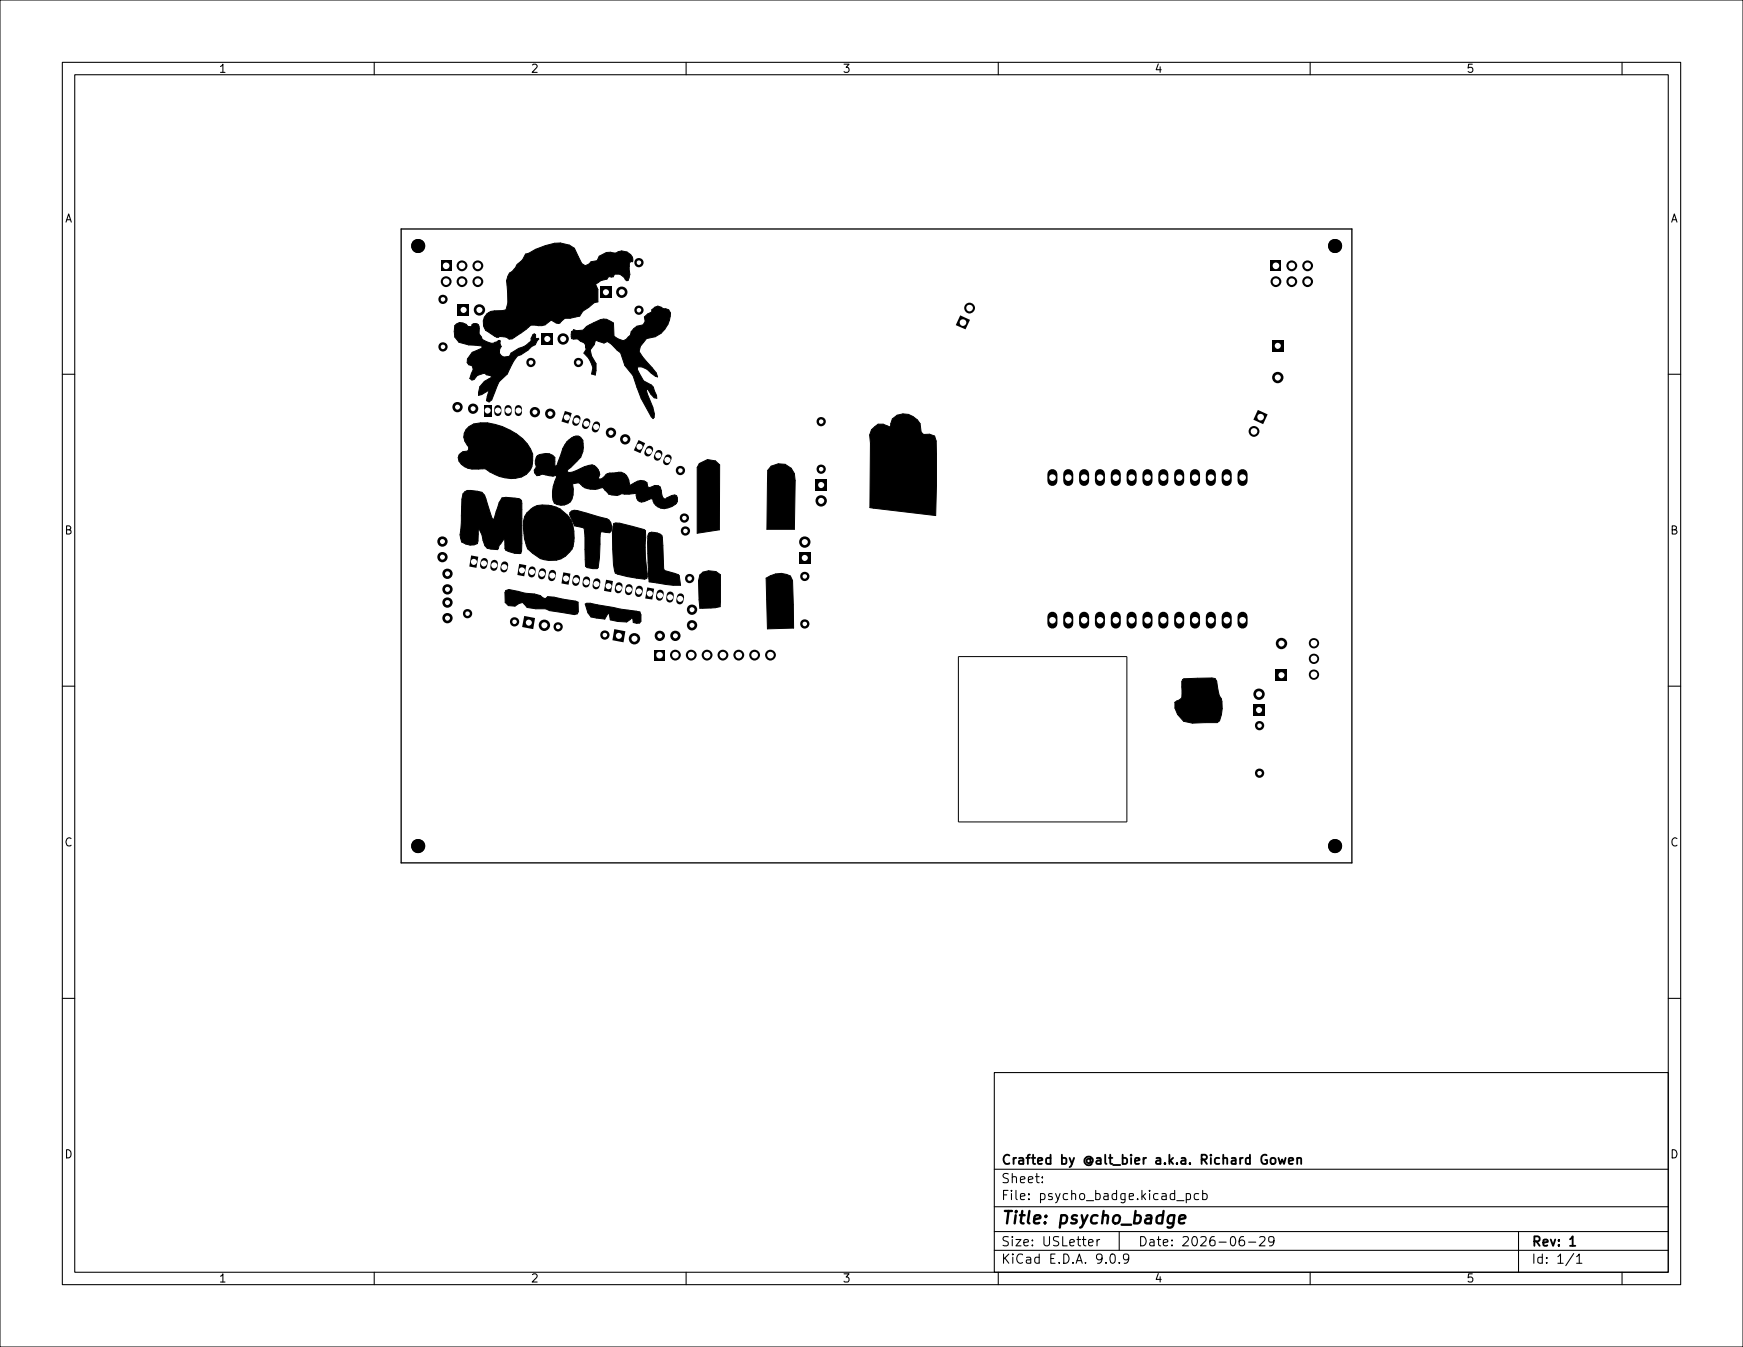
[picture p237: page 8]

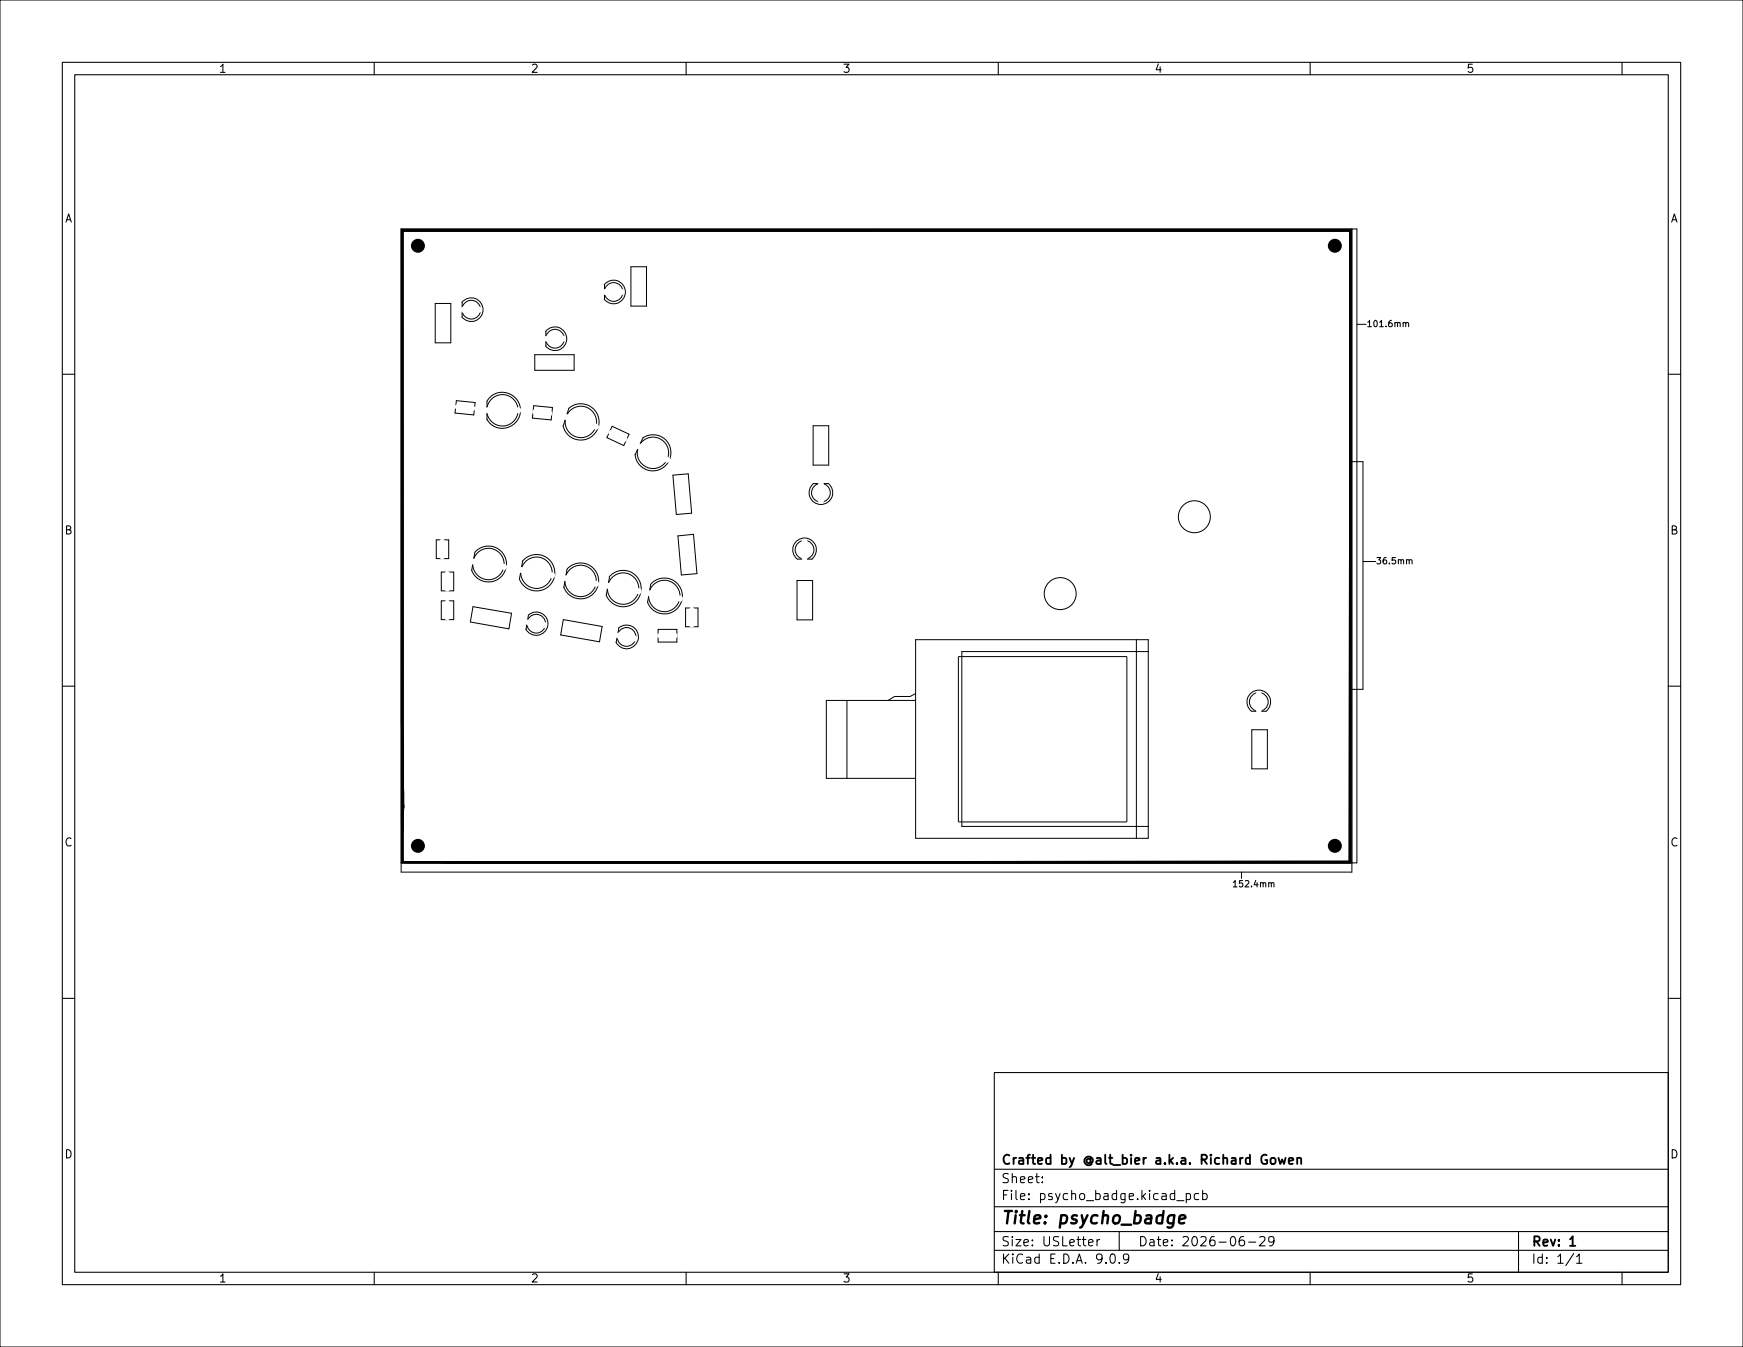
[picture p238: page 9]
