gowenrw/psycho_badge/eda/psycho_sao/snapshots/psycho_badge_sao_2_pcb_rev1.pdf

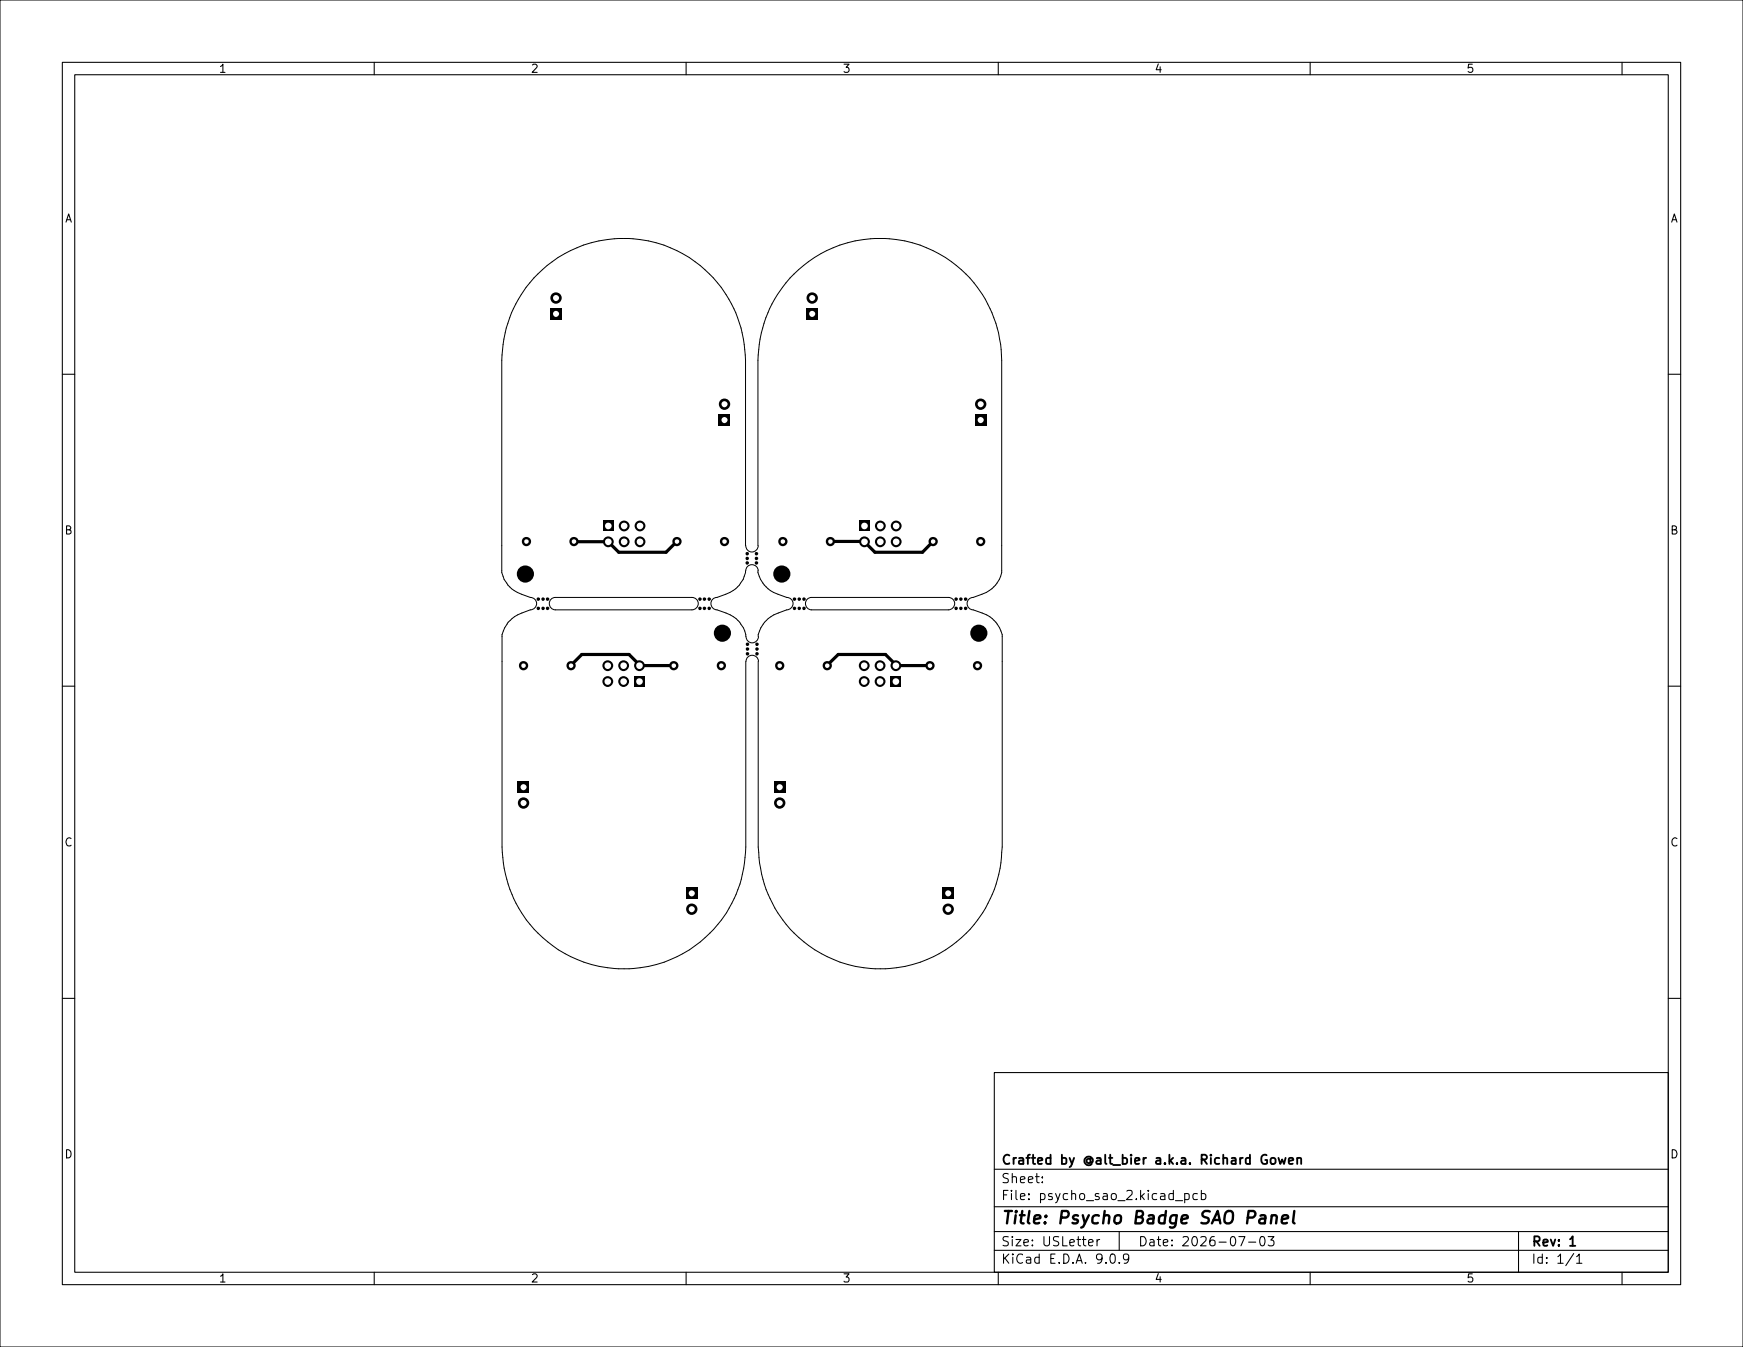
[picture p239: page 1]

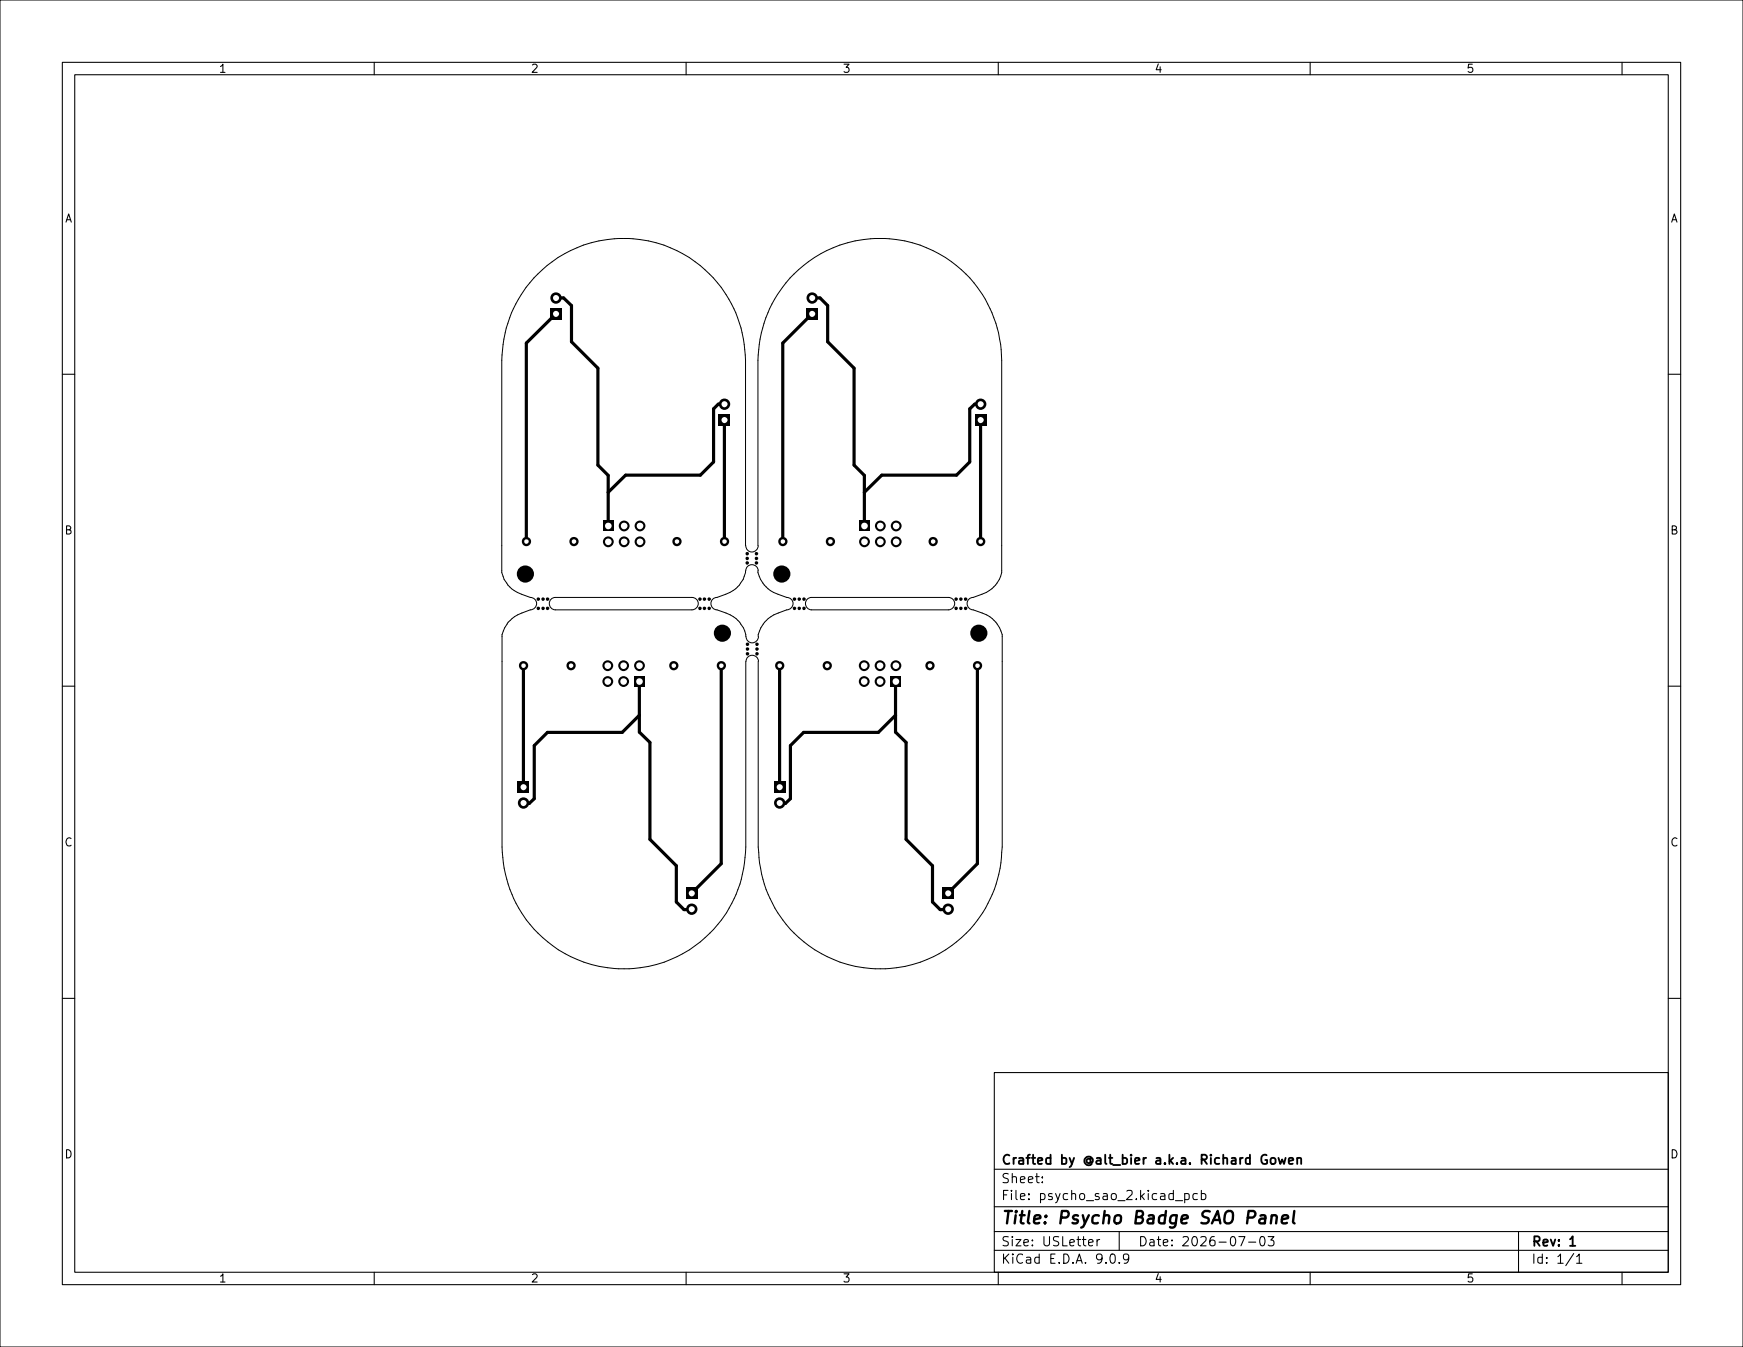
[picture p240: page 2]

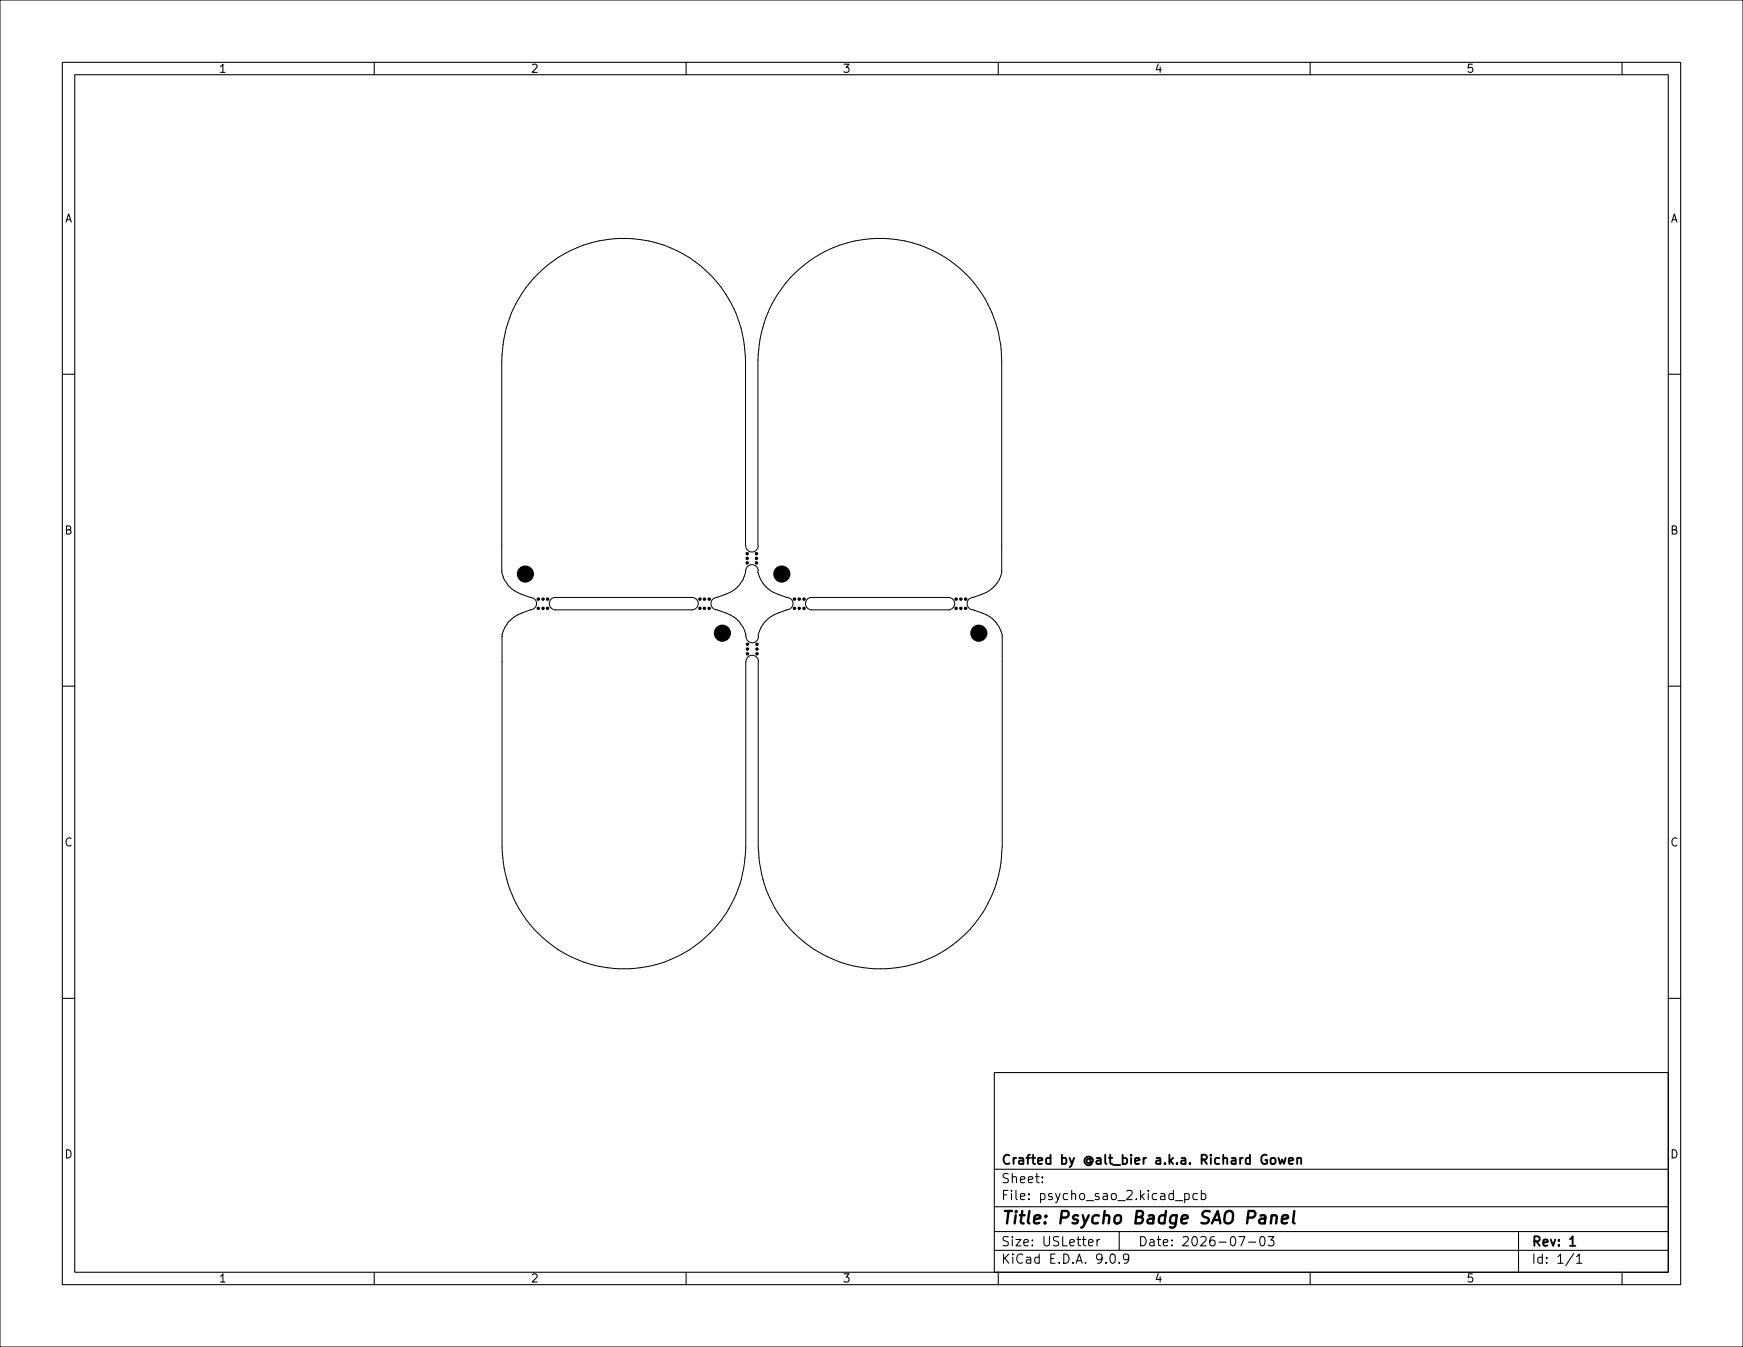
[picture p241: page 3]

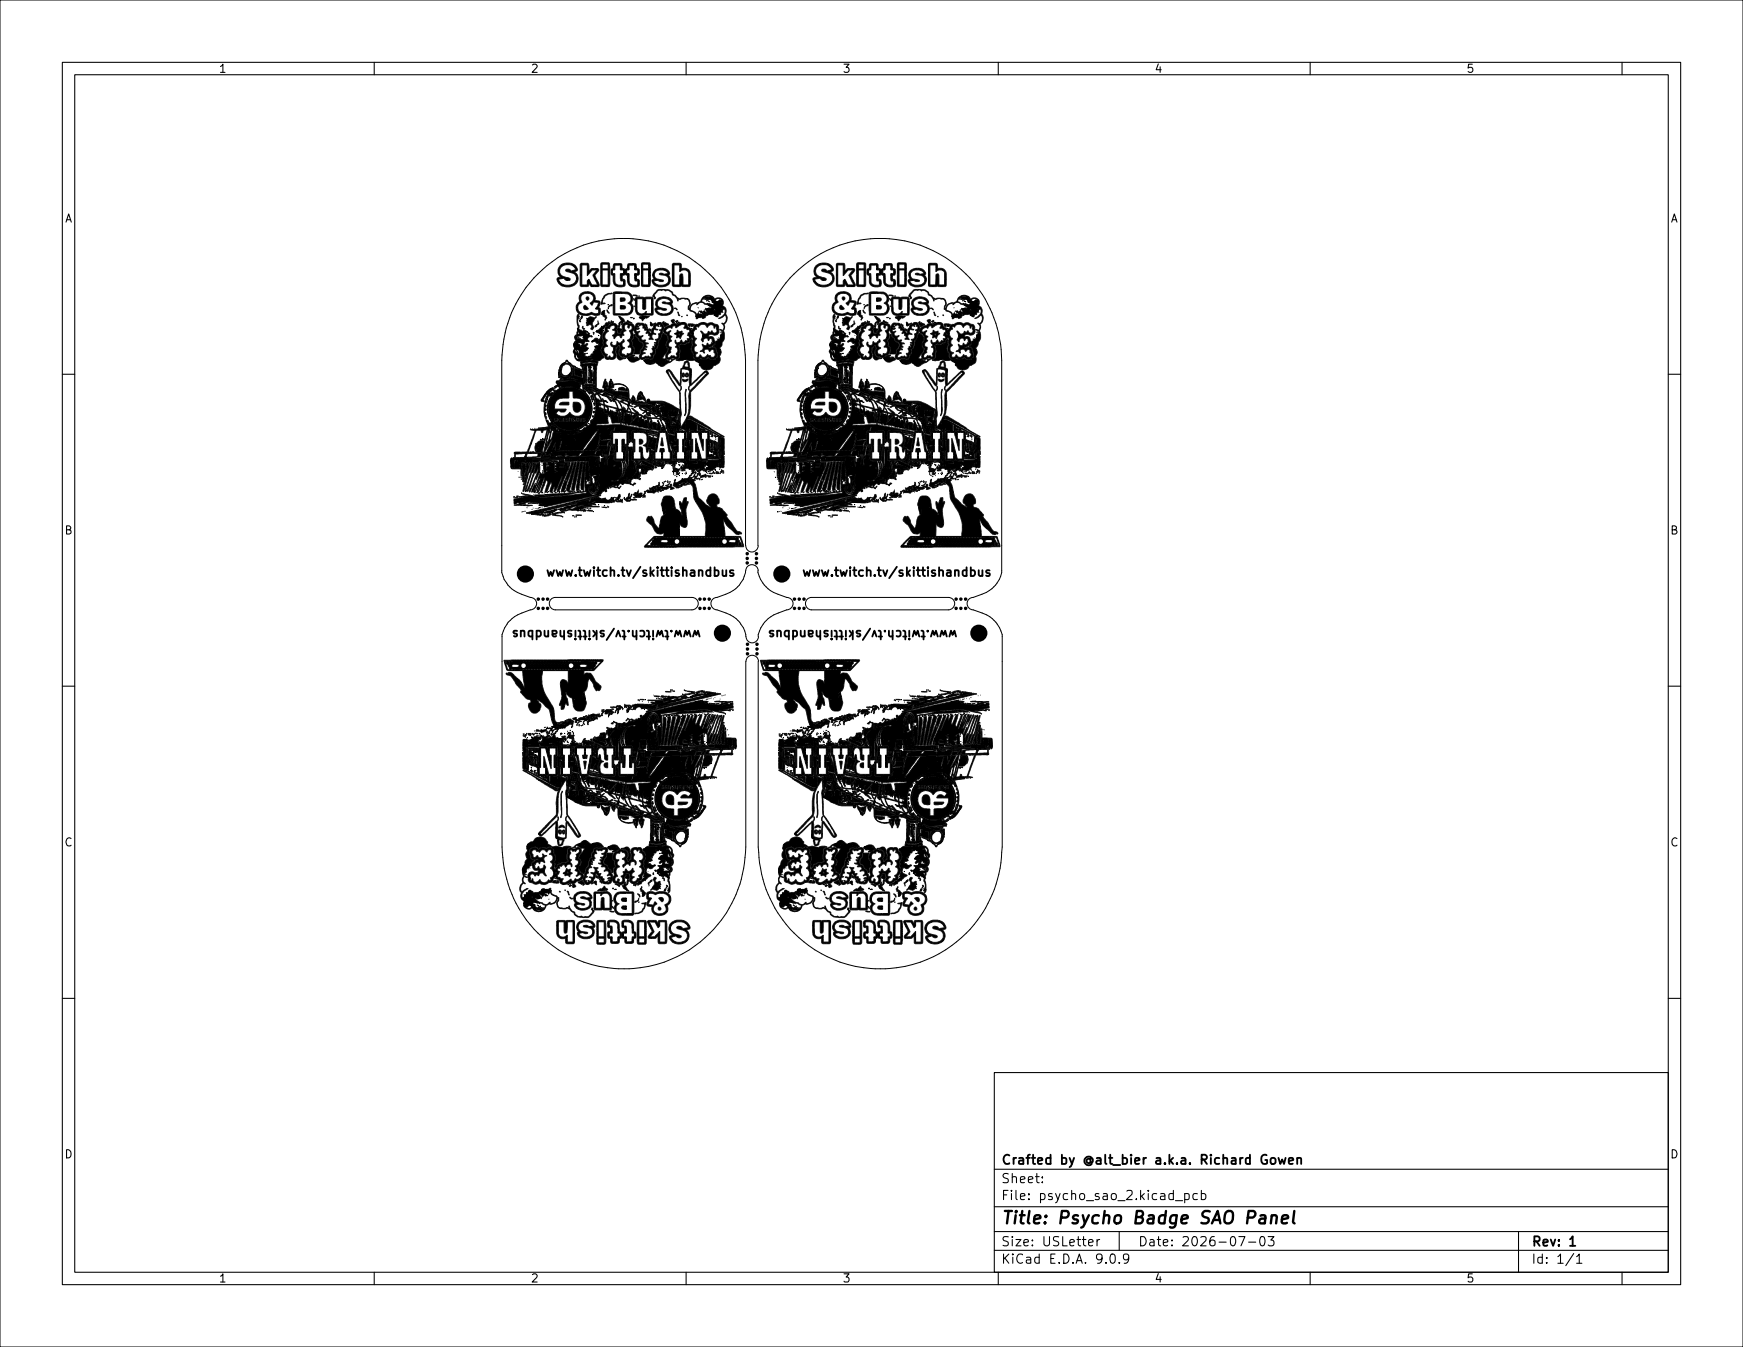
[picture p242: page 5]

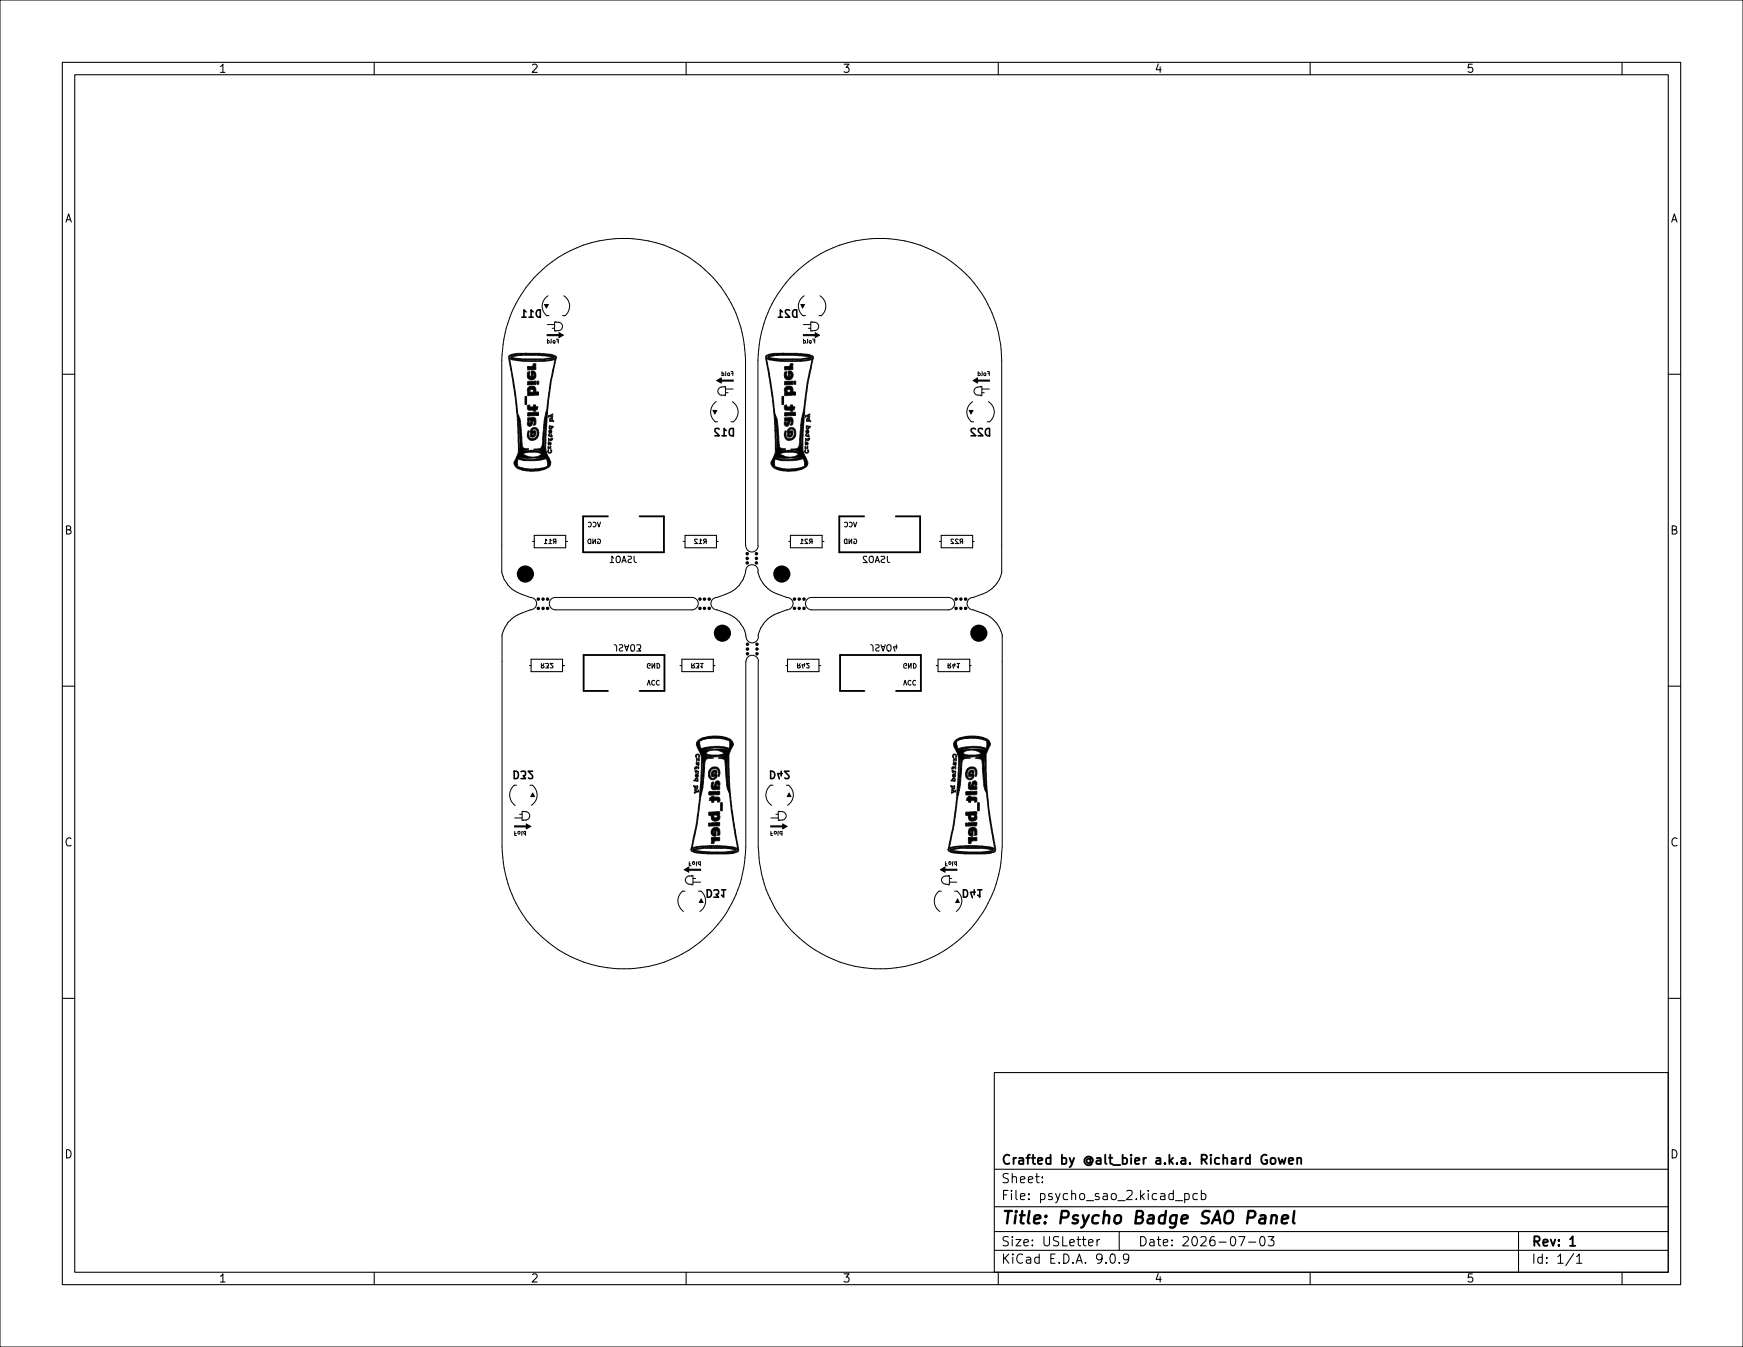
[picture p243: page 6]

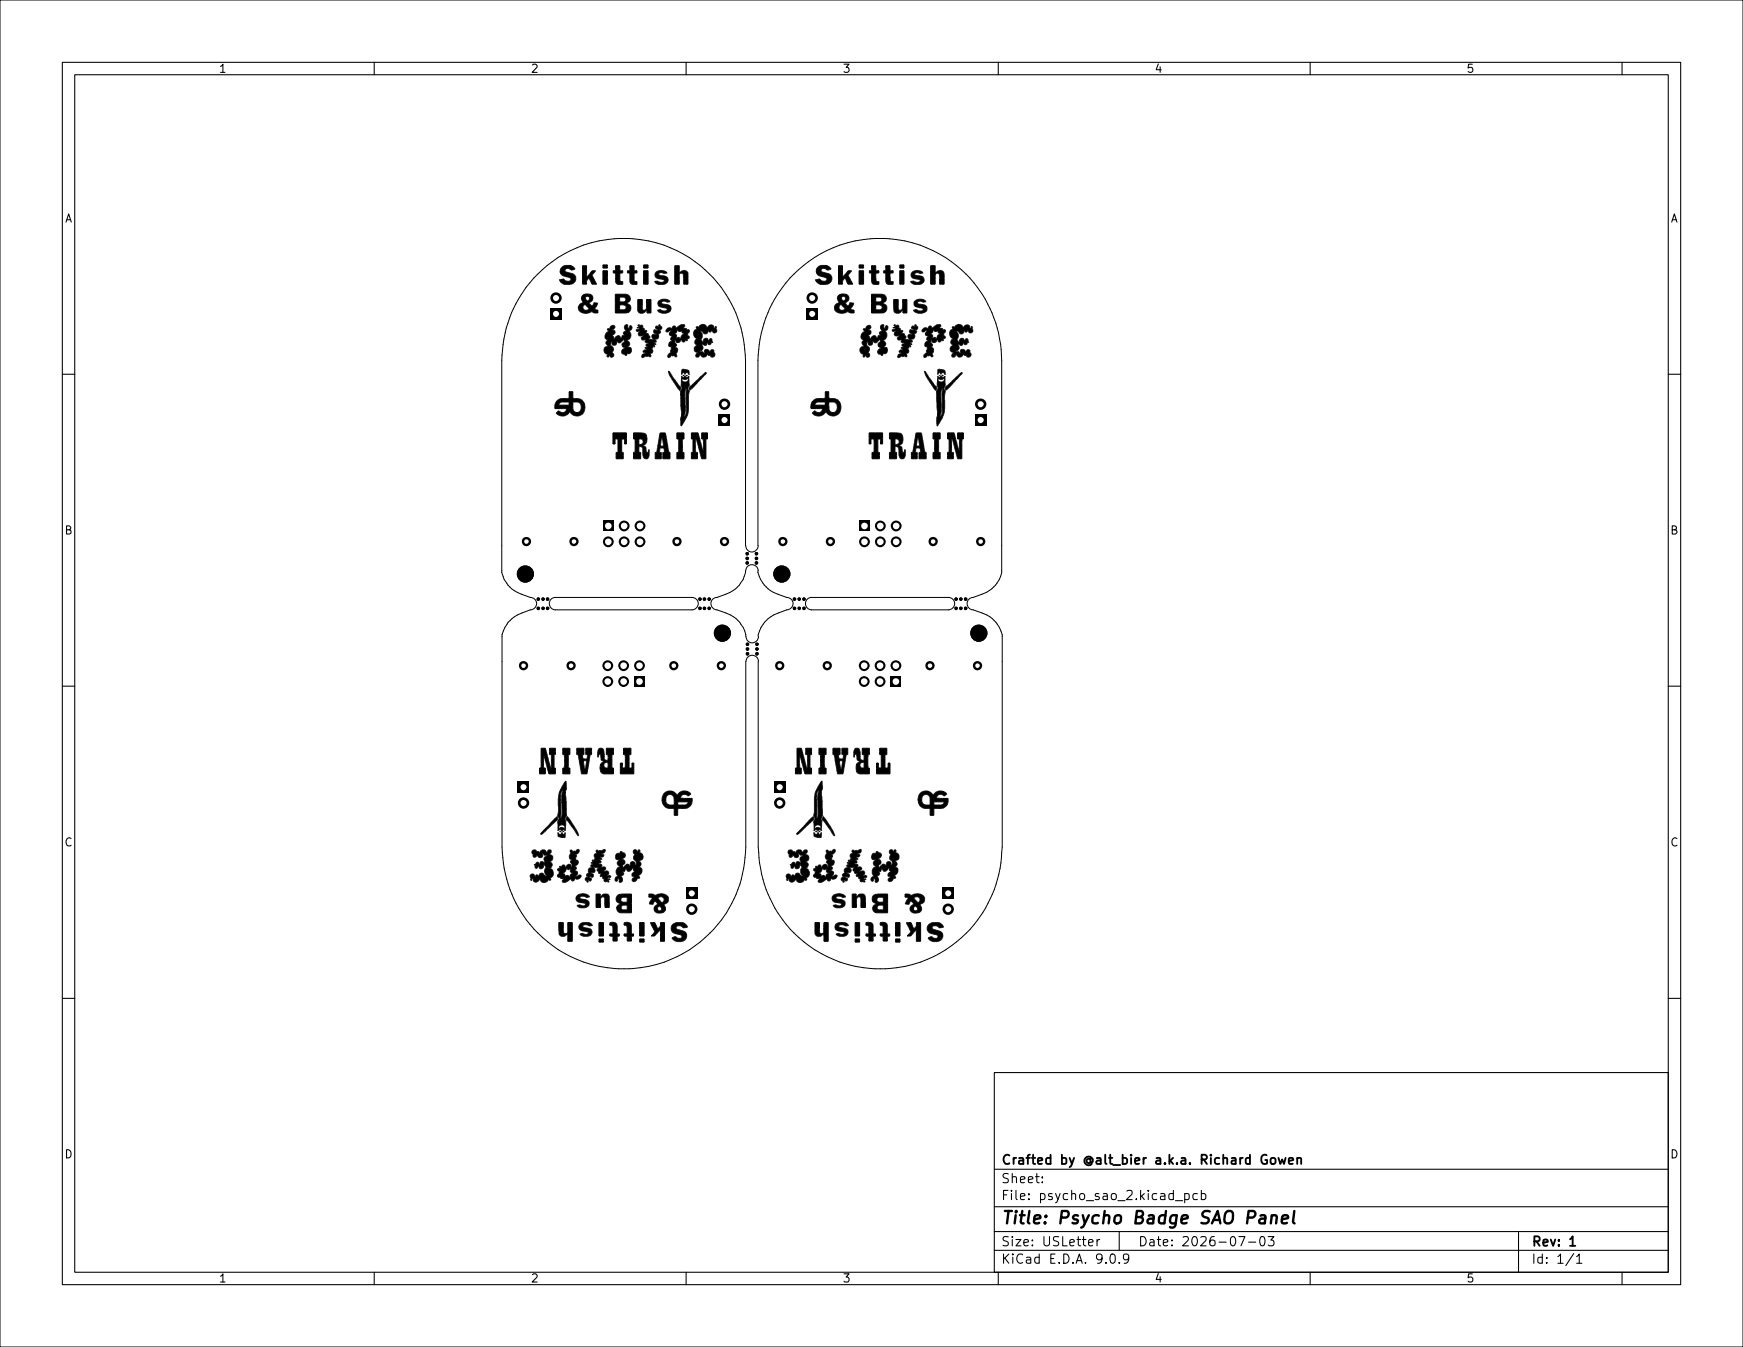
[picture p244: page 7]

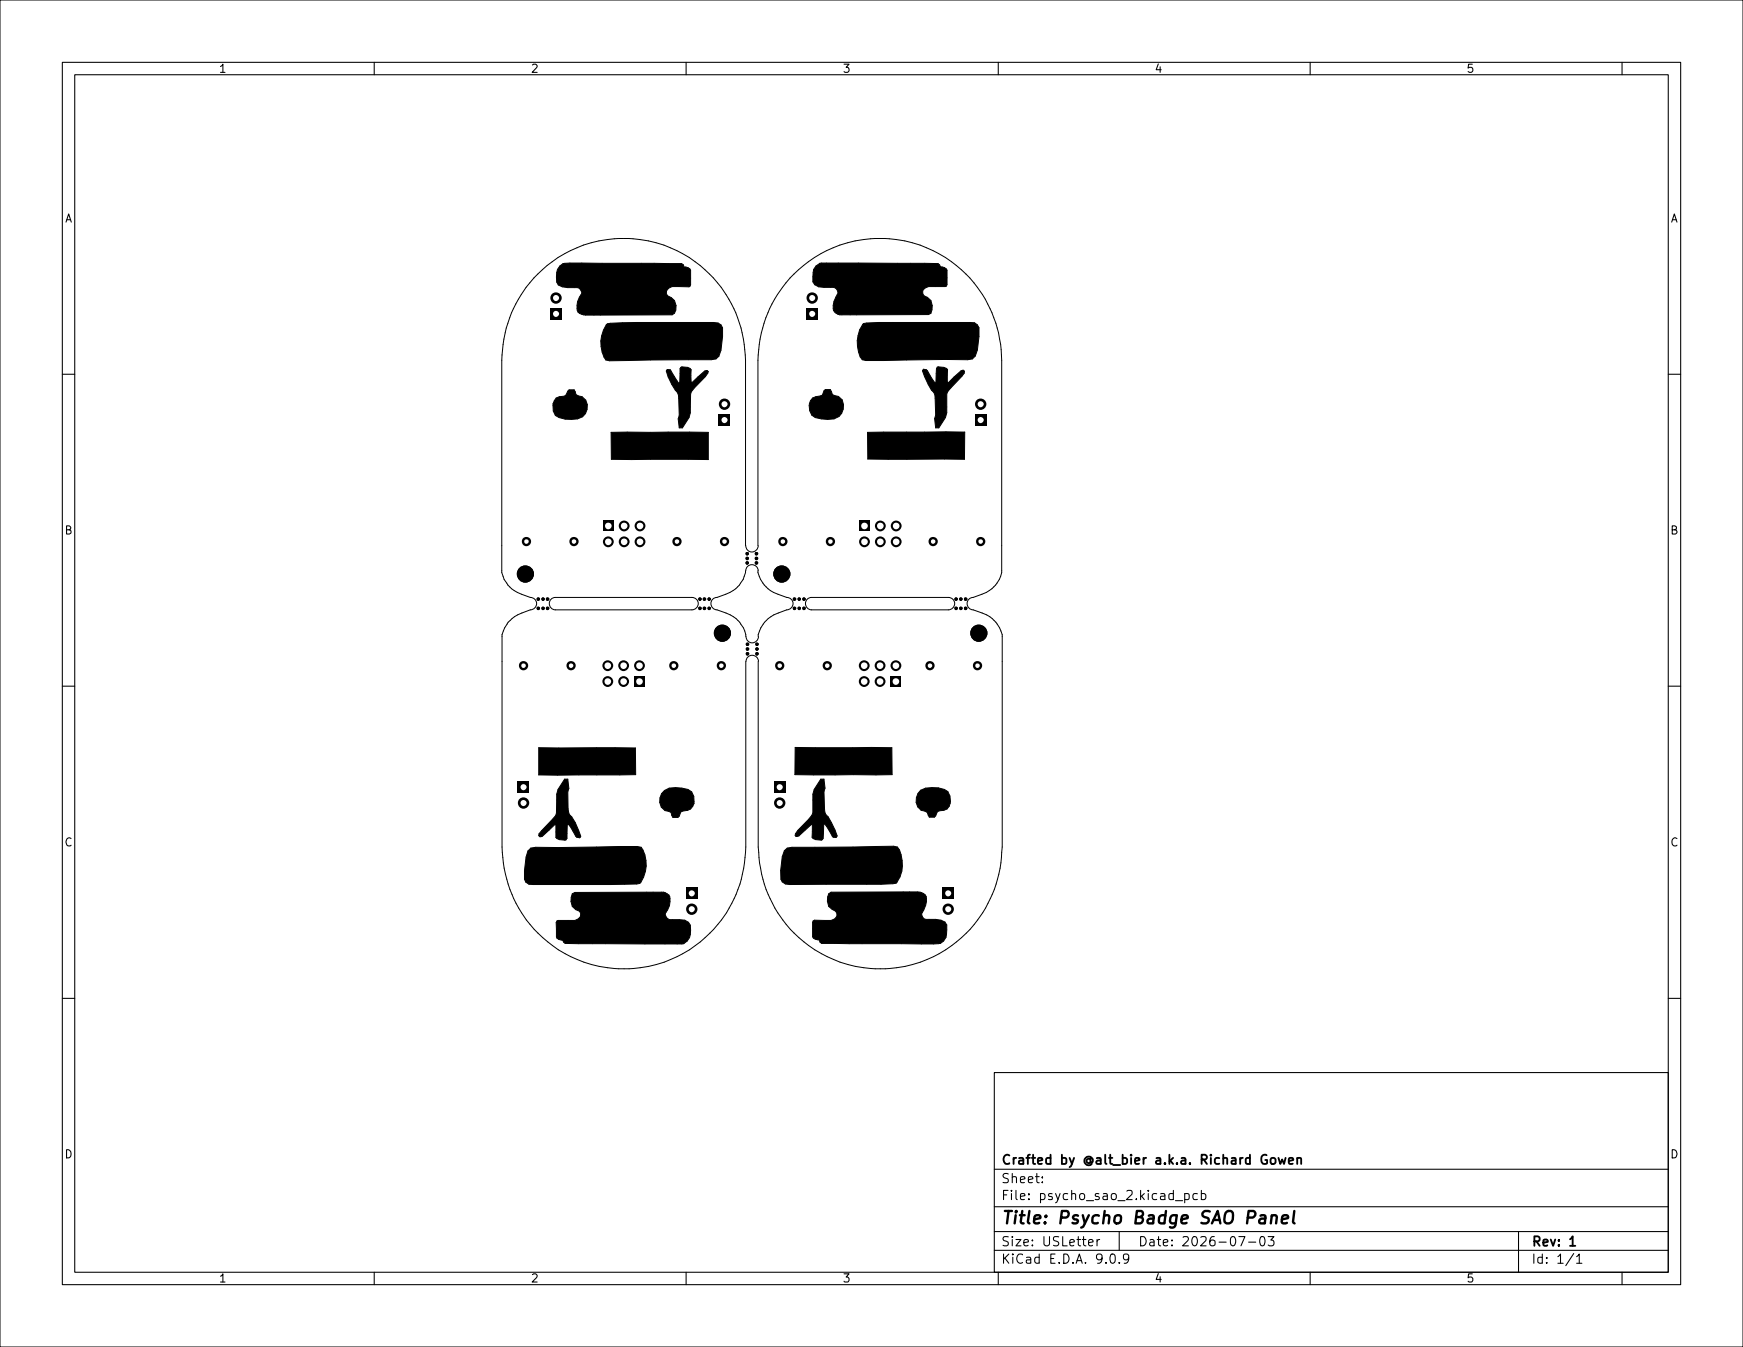
[picture p245: page 8]

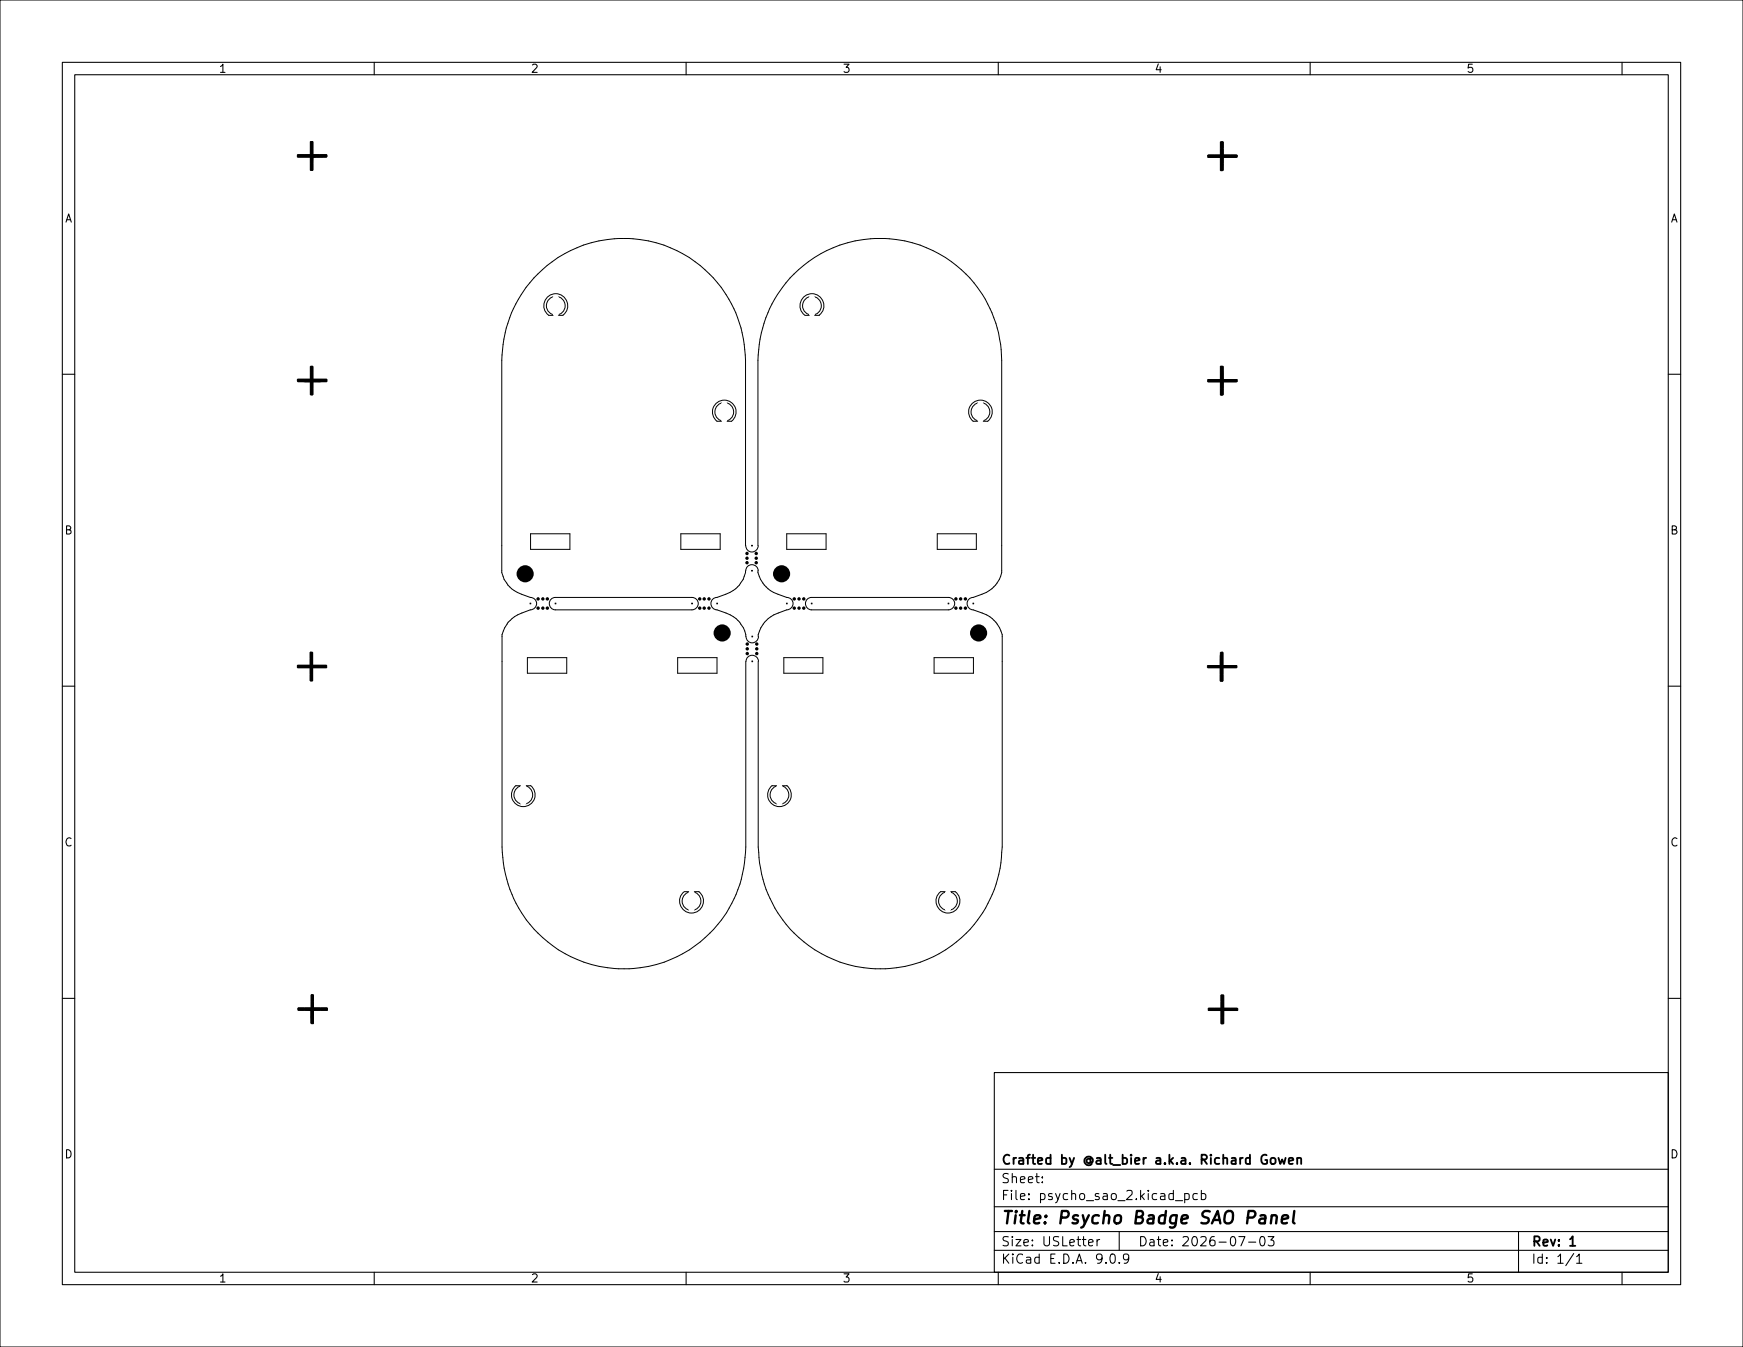
[picture p246: page 9]
