gowenrw/psycho_badge/eda/psycho_sao/snapshots/psycho_badge_sao_pcb_rev1.pdf

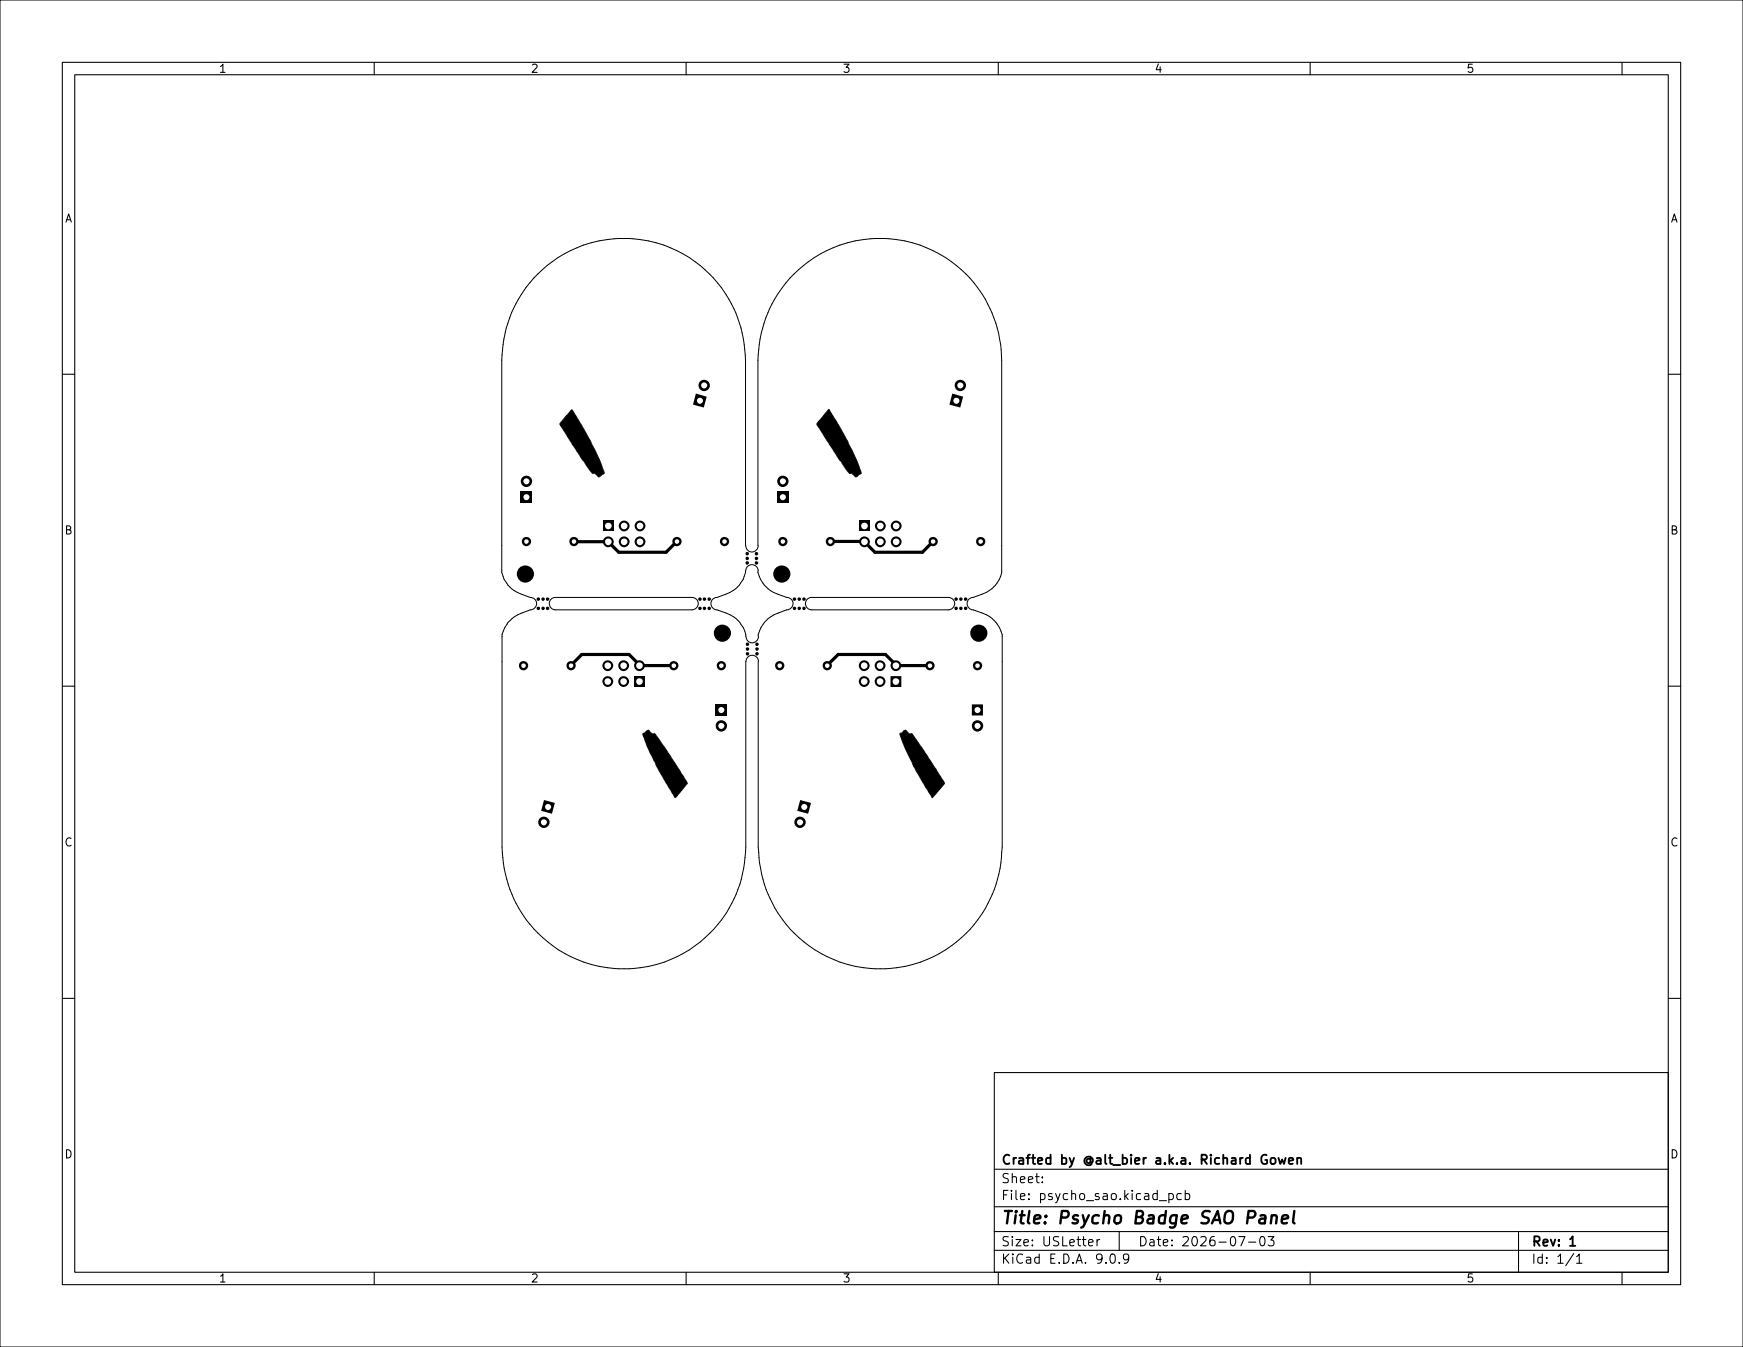
[picture p247: page 1]

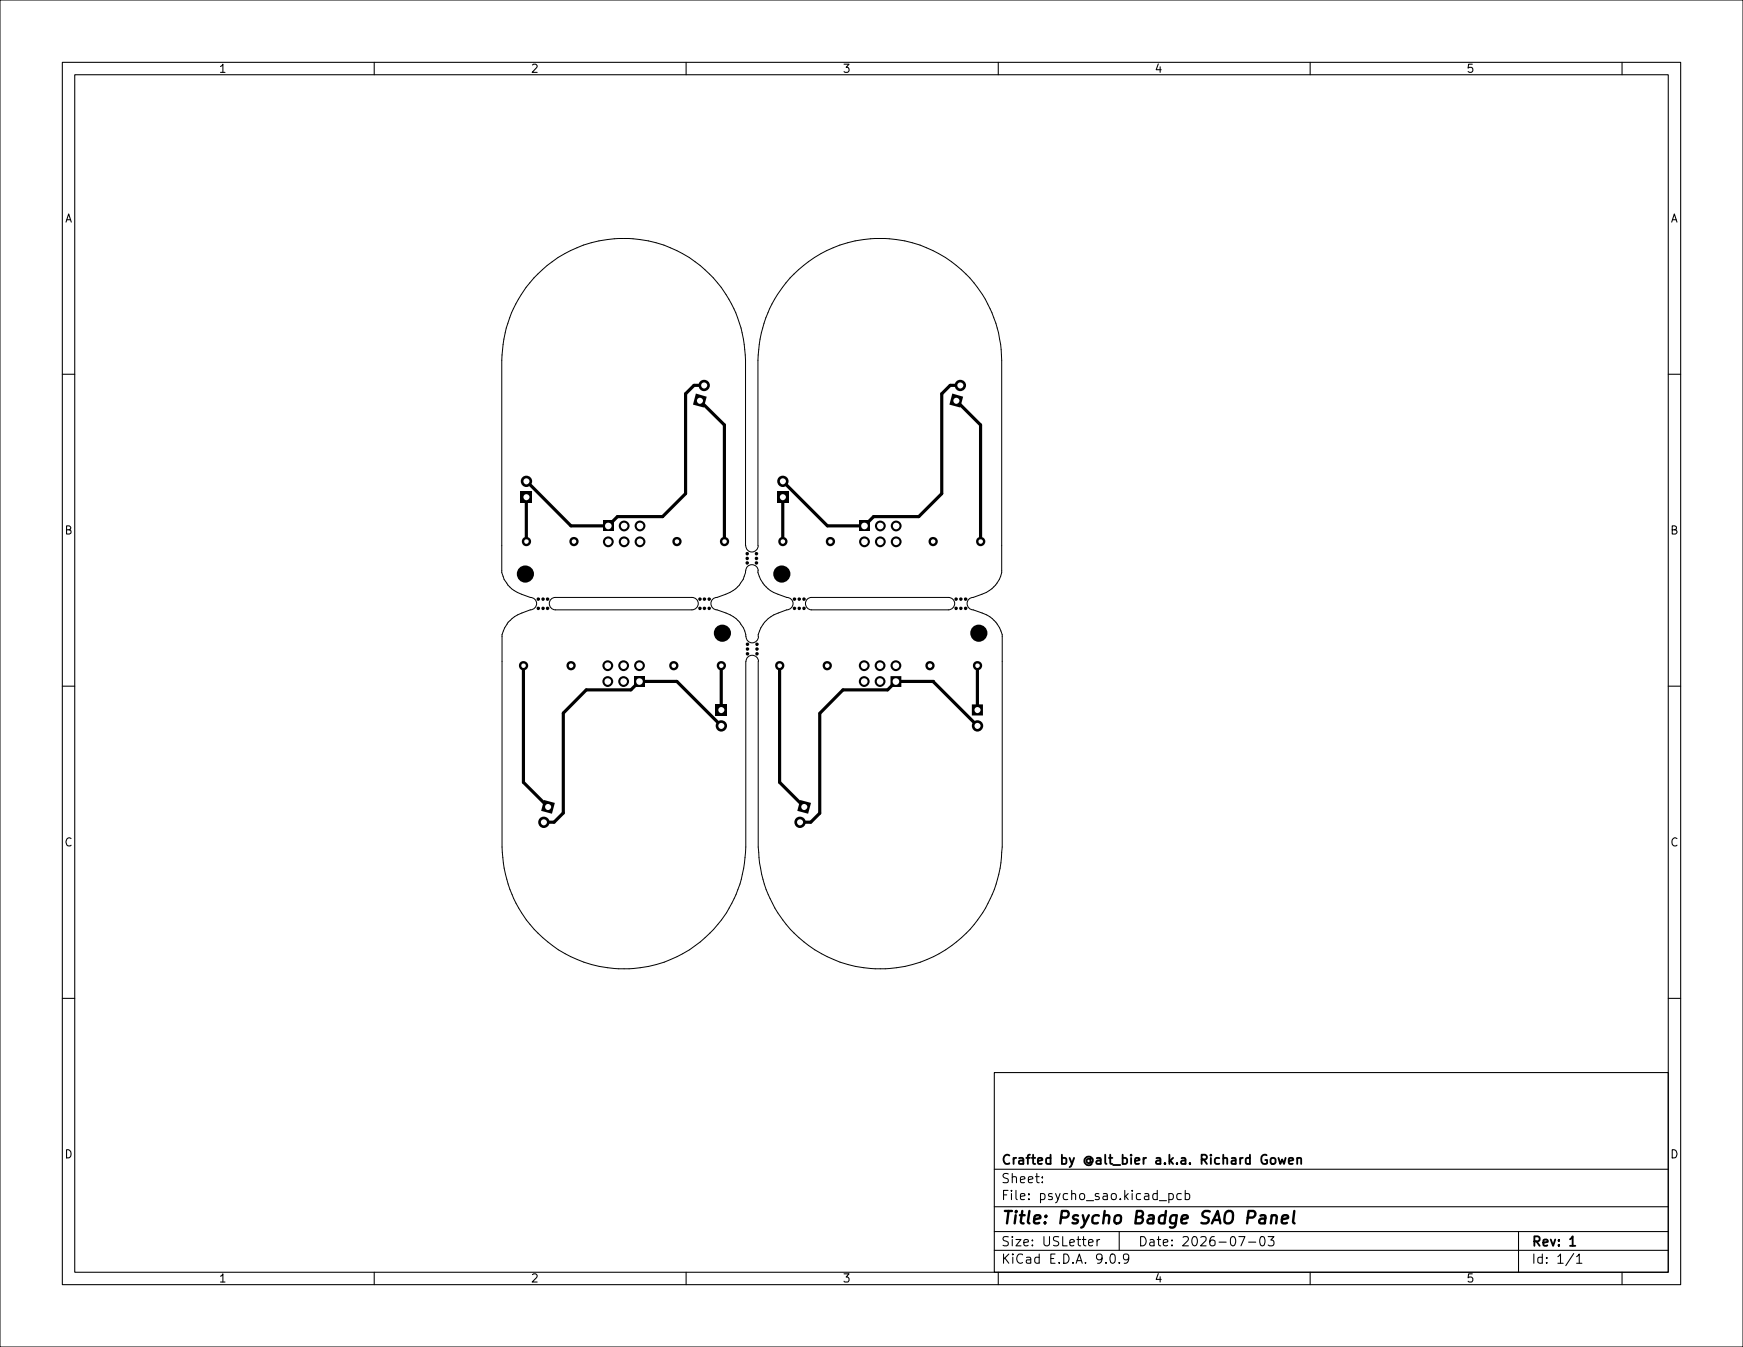
[picture p248: page 2]

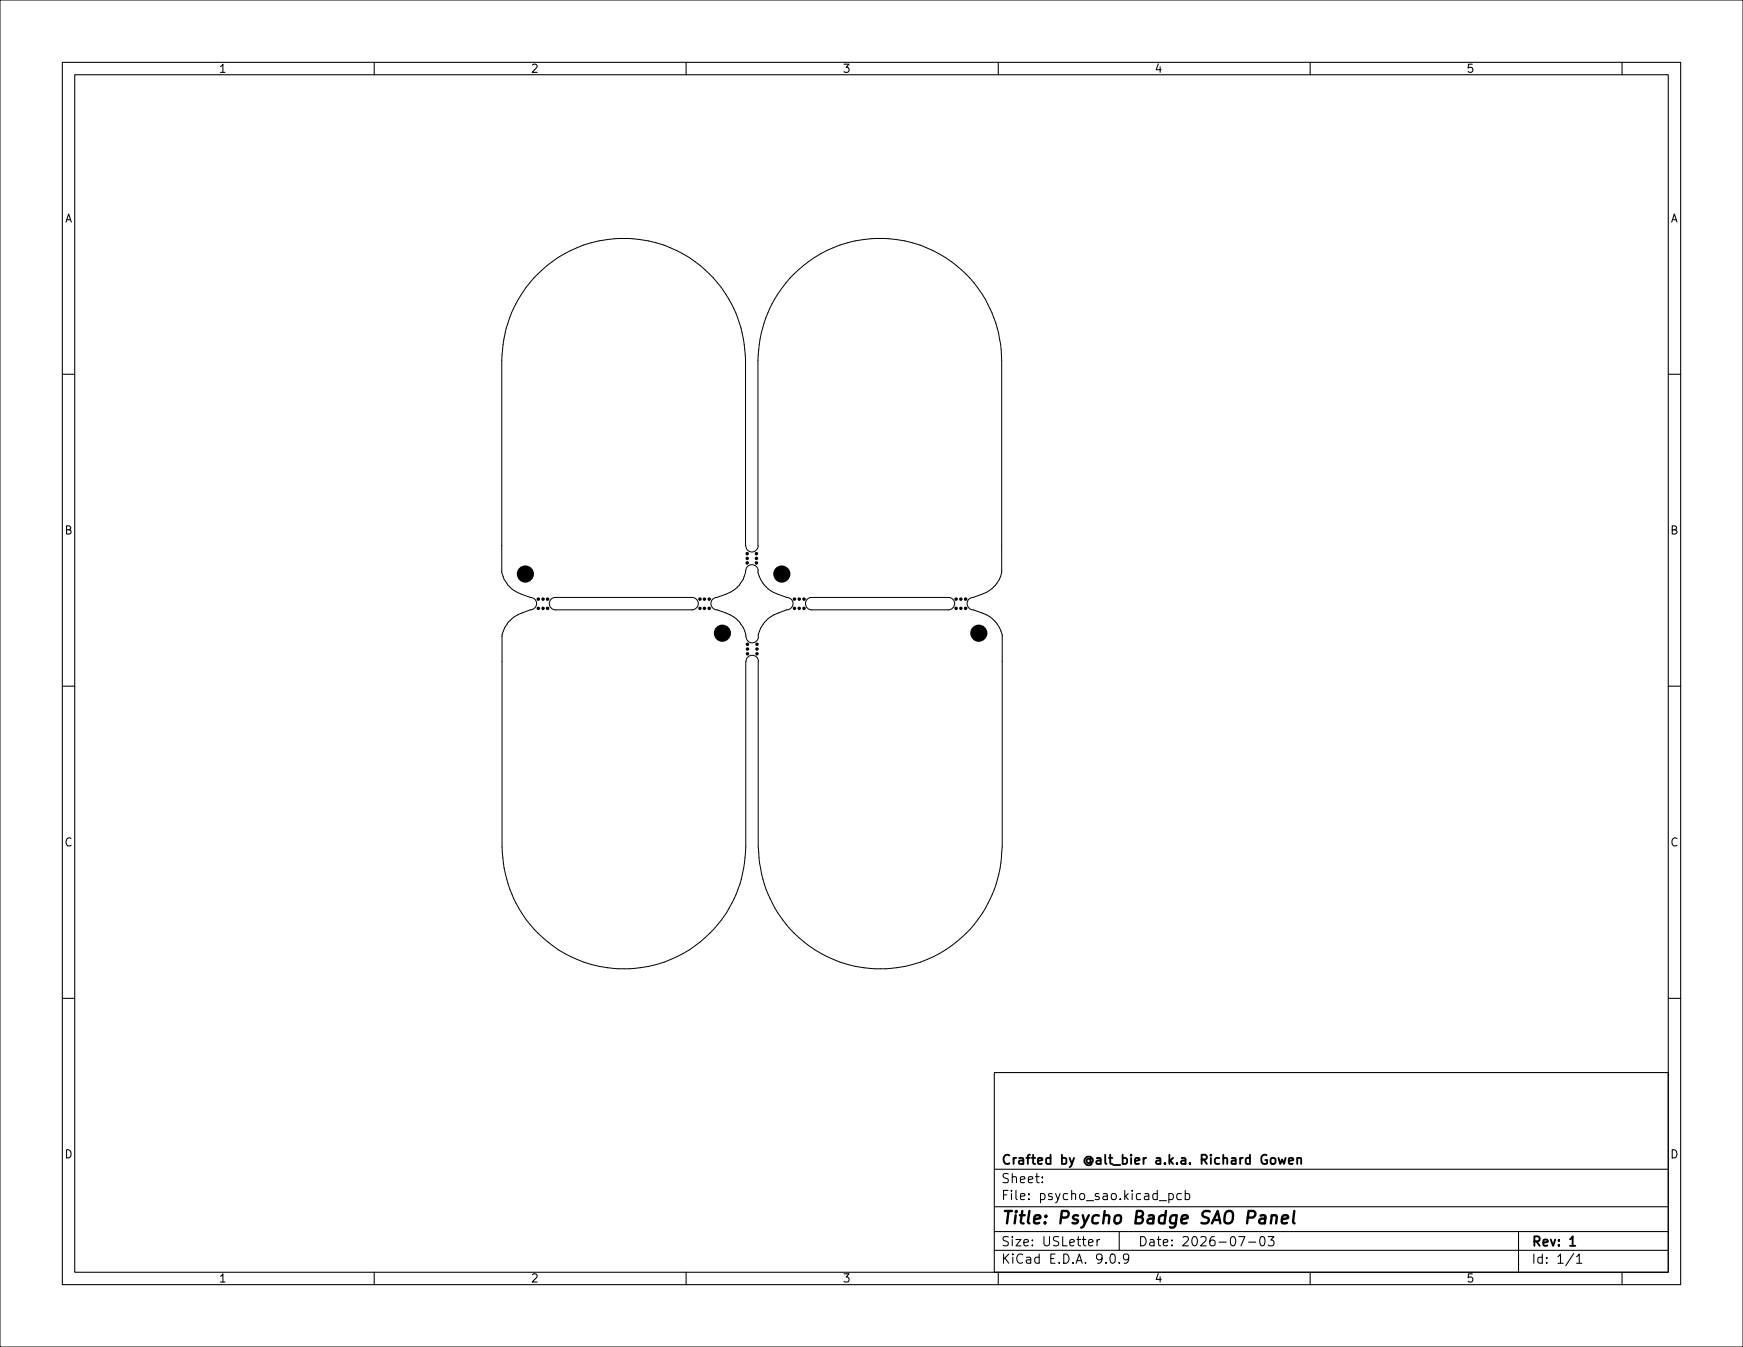
[picture p249: page 3]

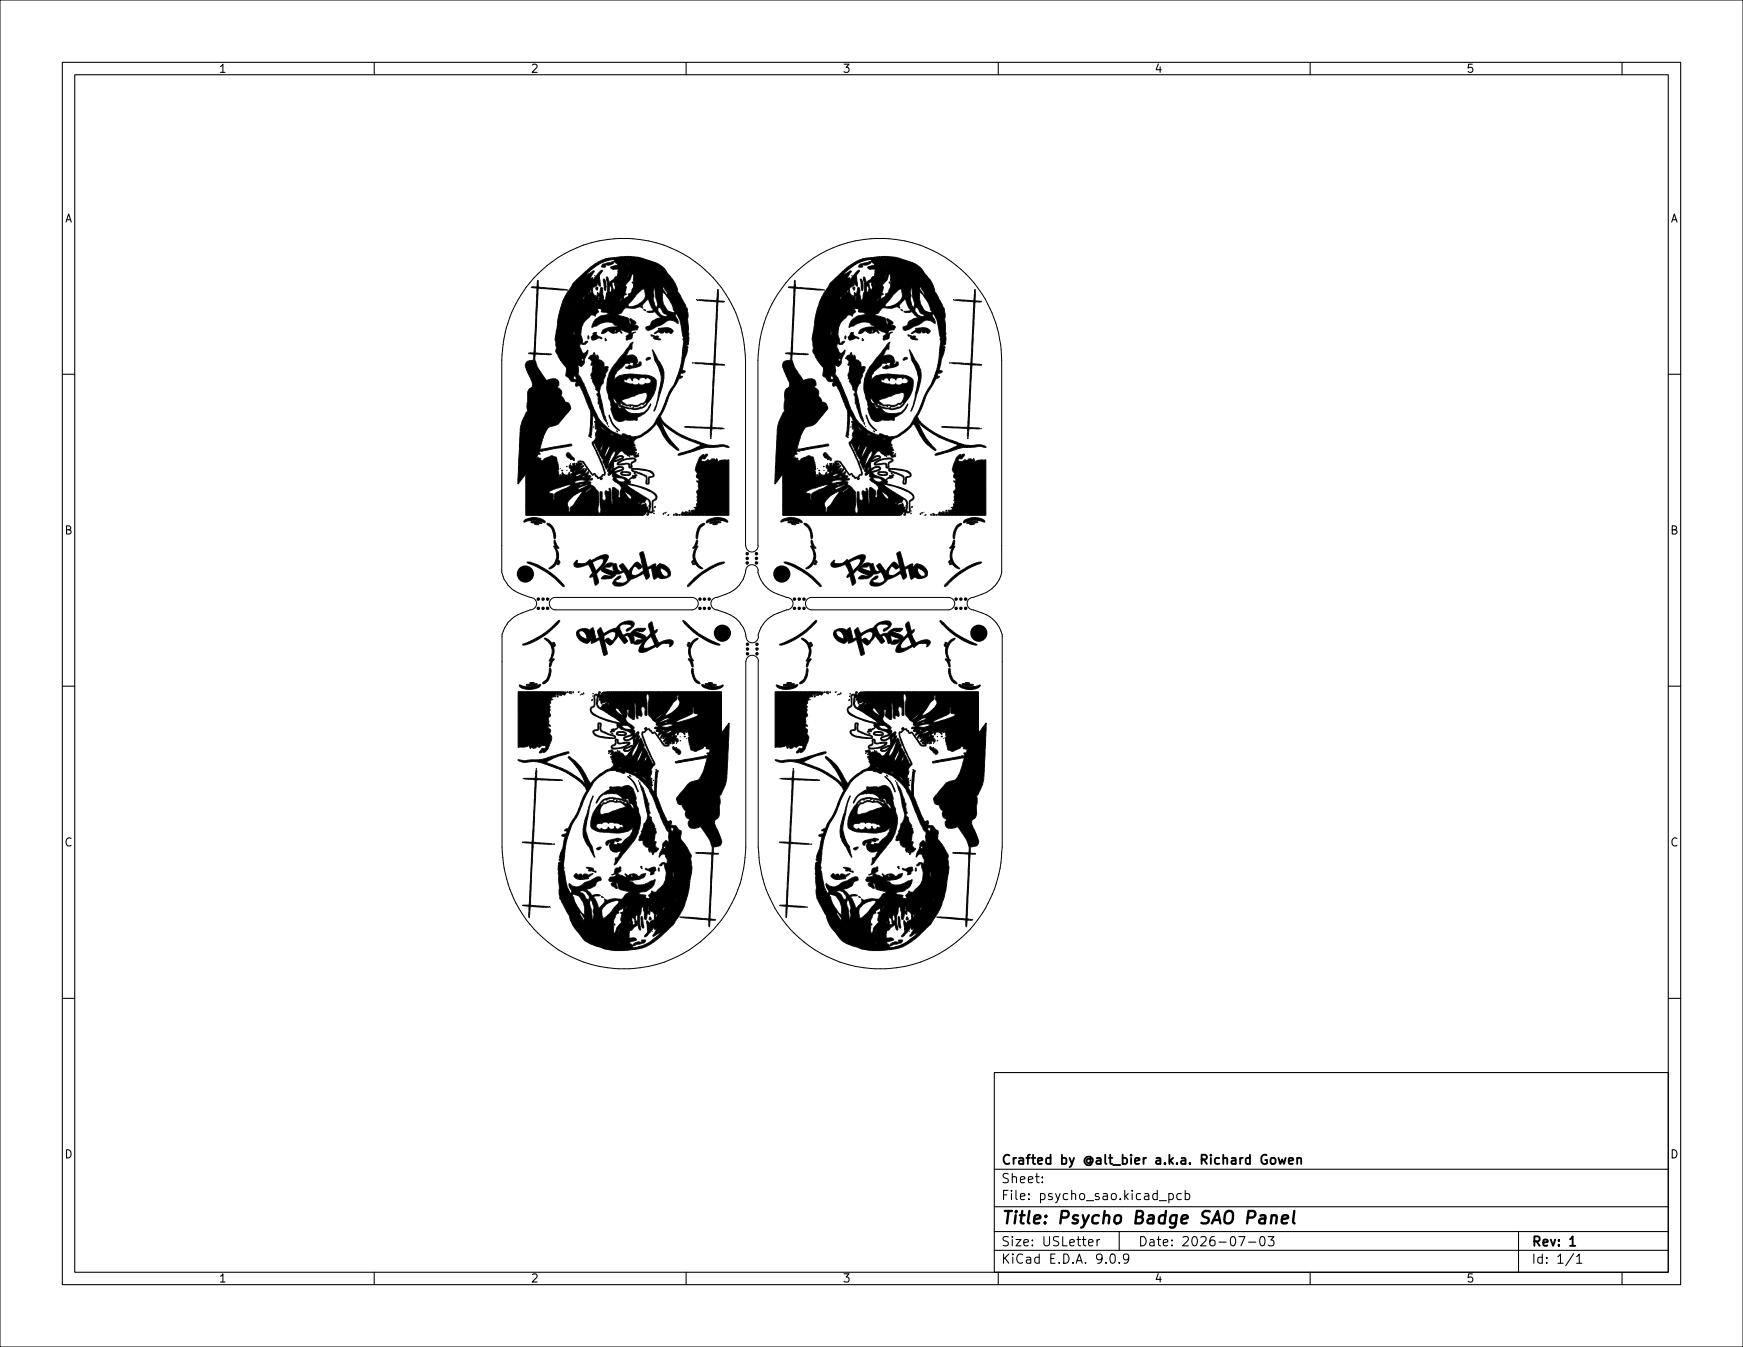
[picture p250: page 5]

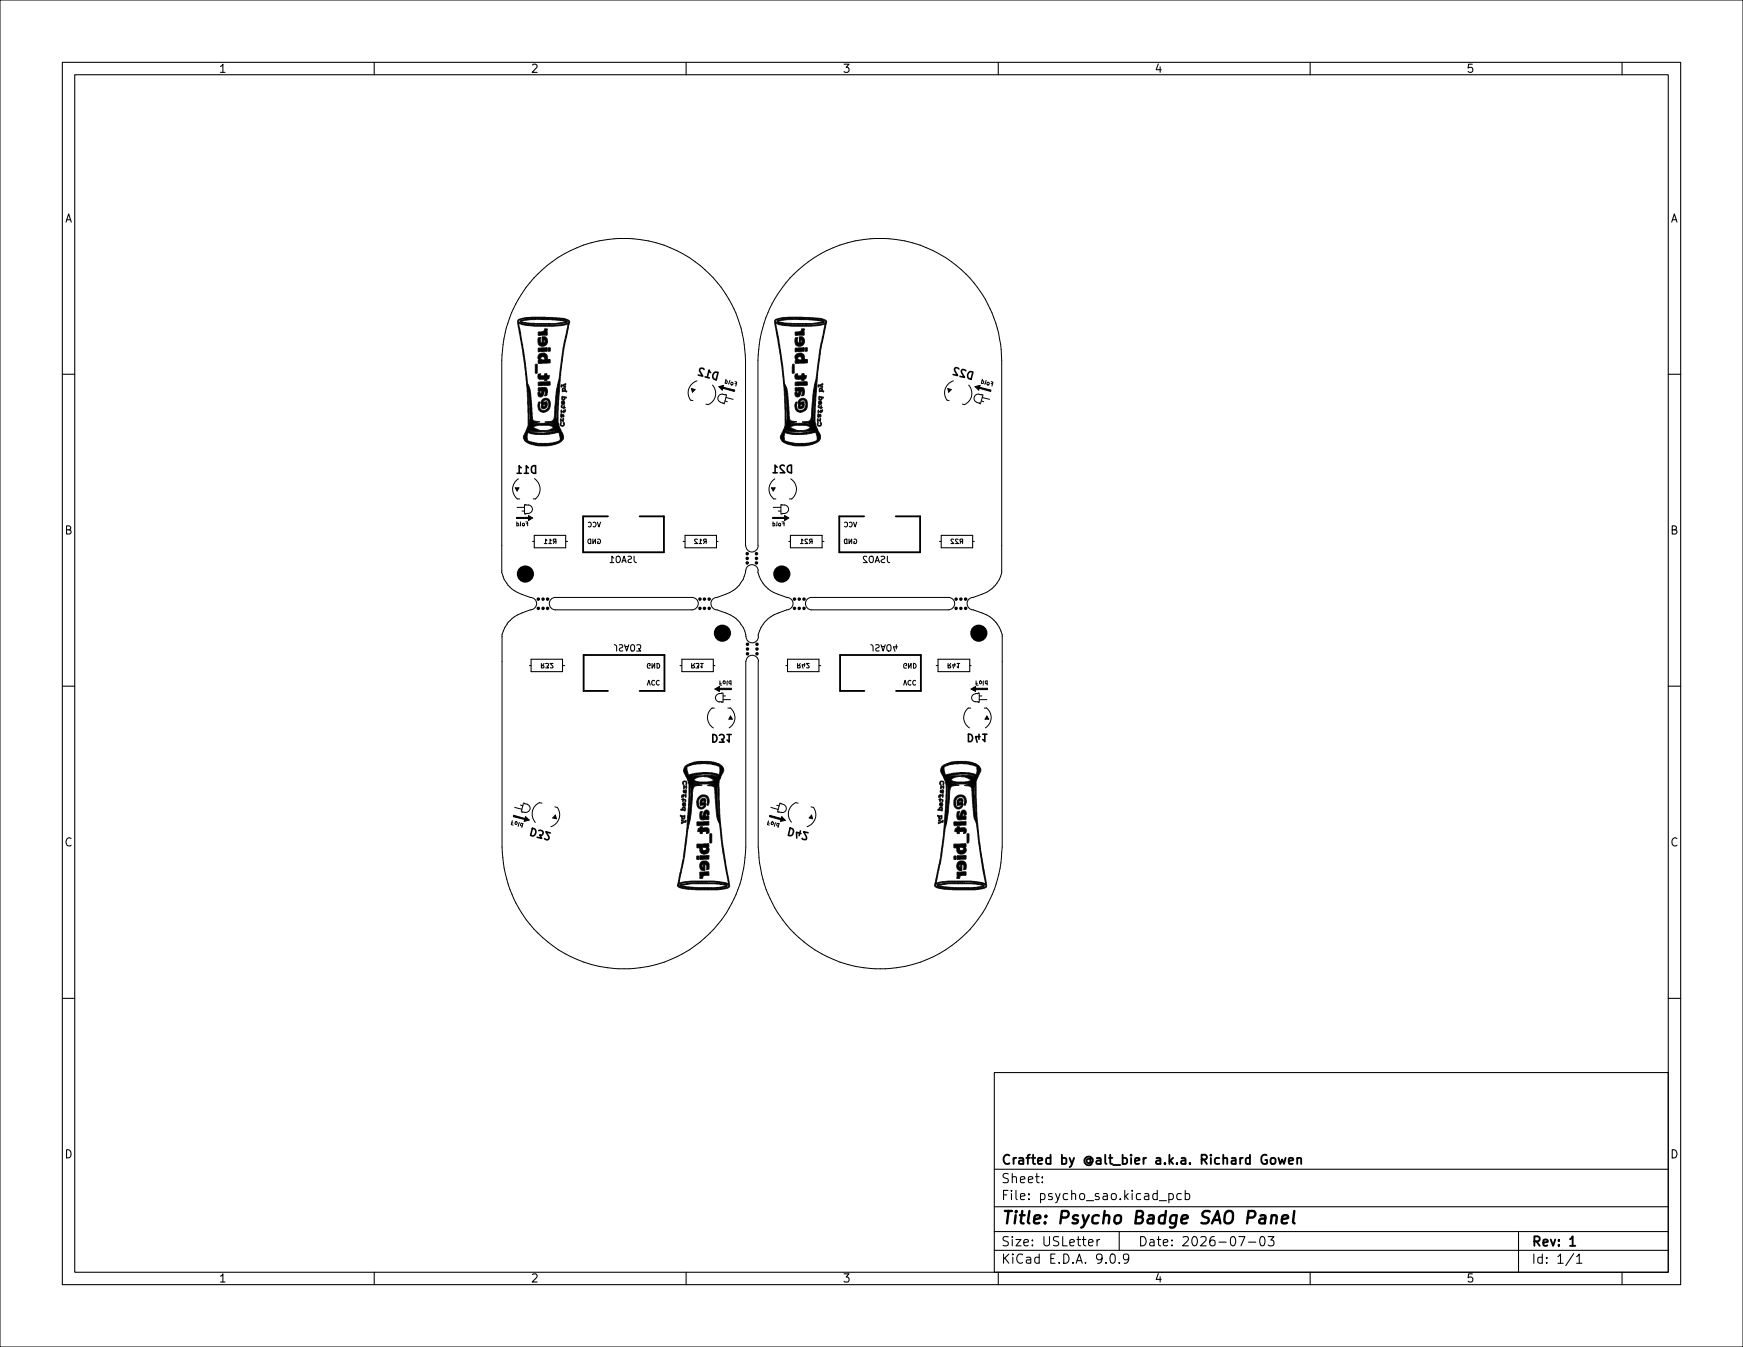
[picture p251: page 6]

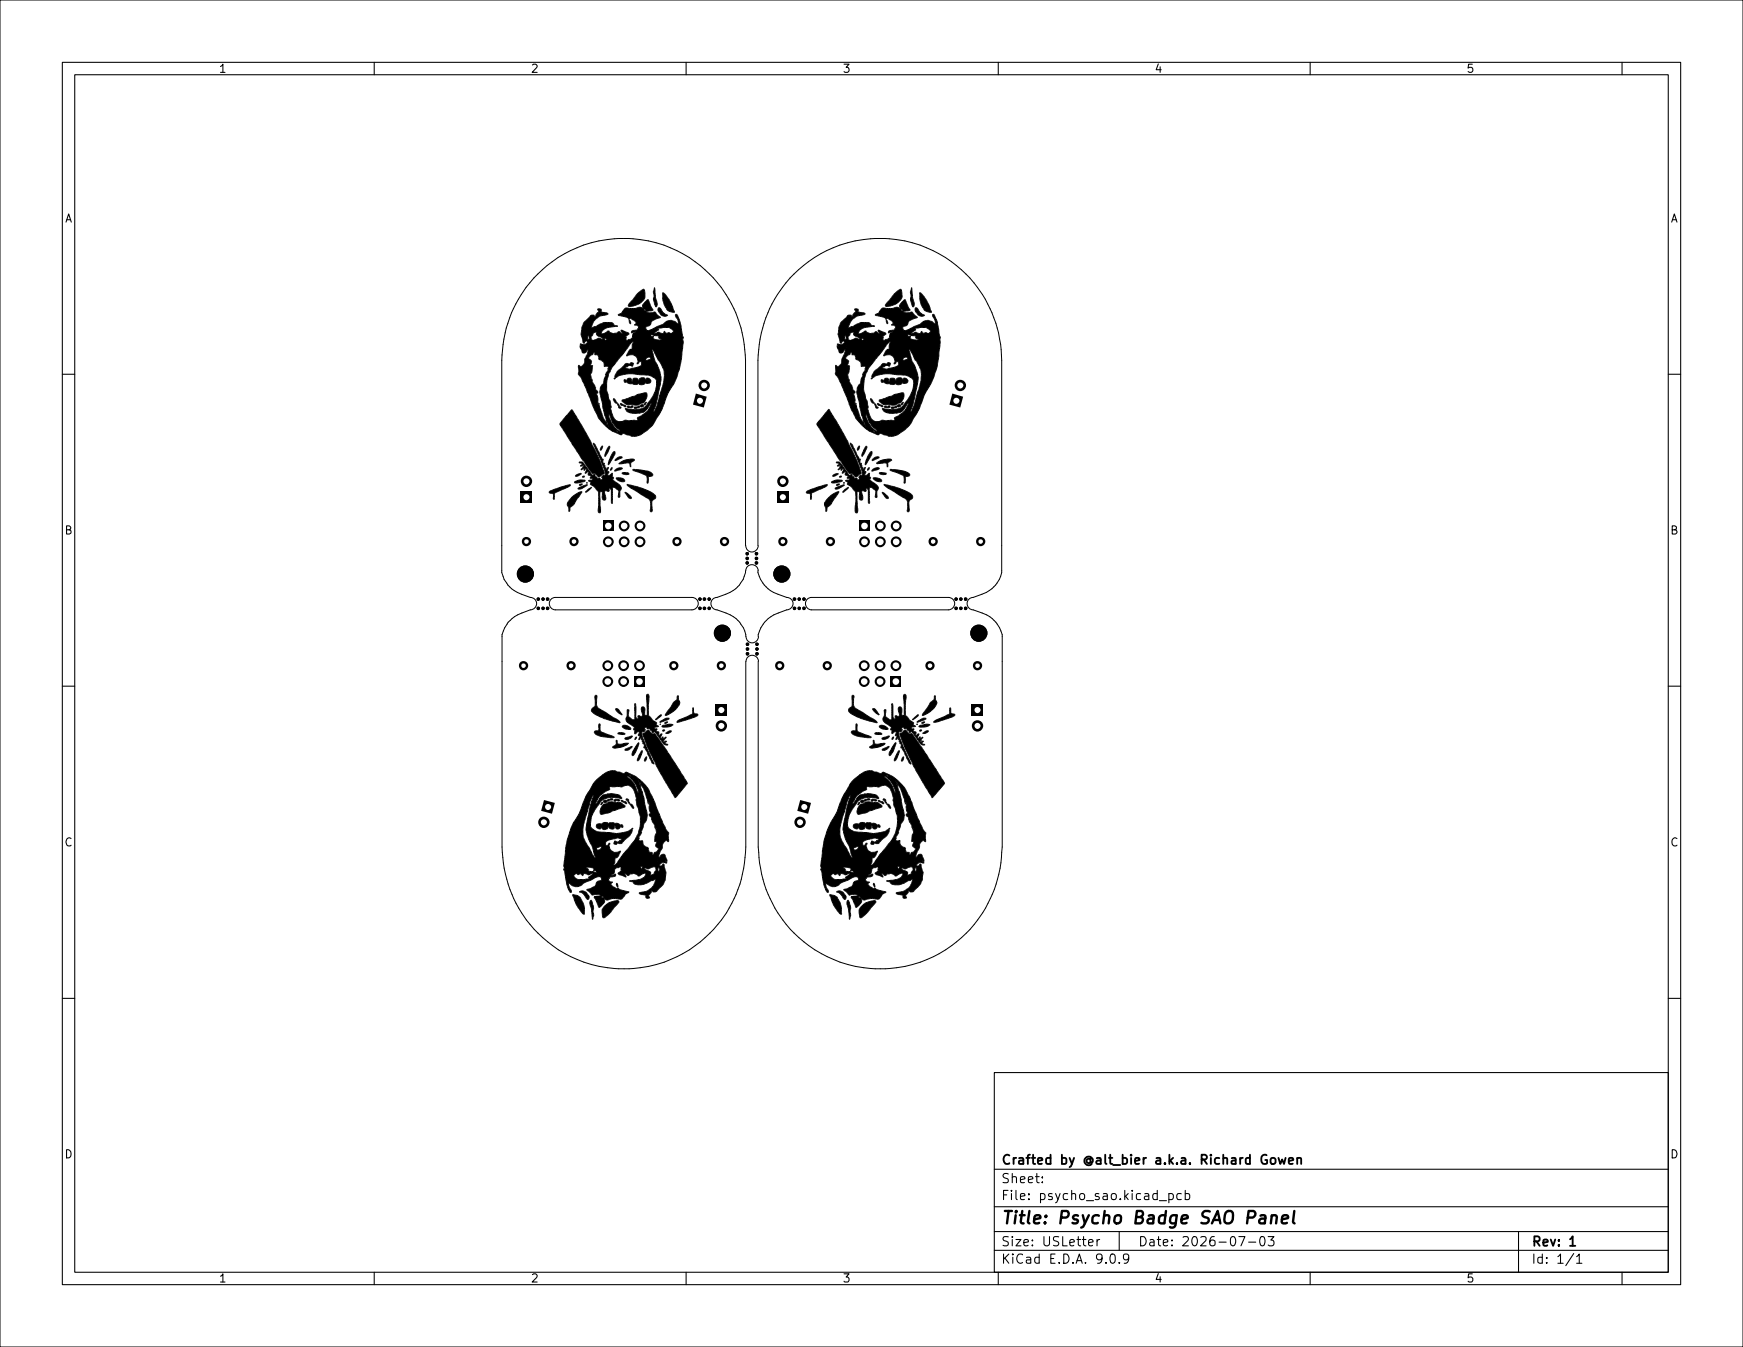
[picture p252: page 7]

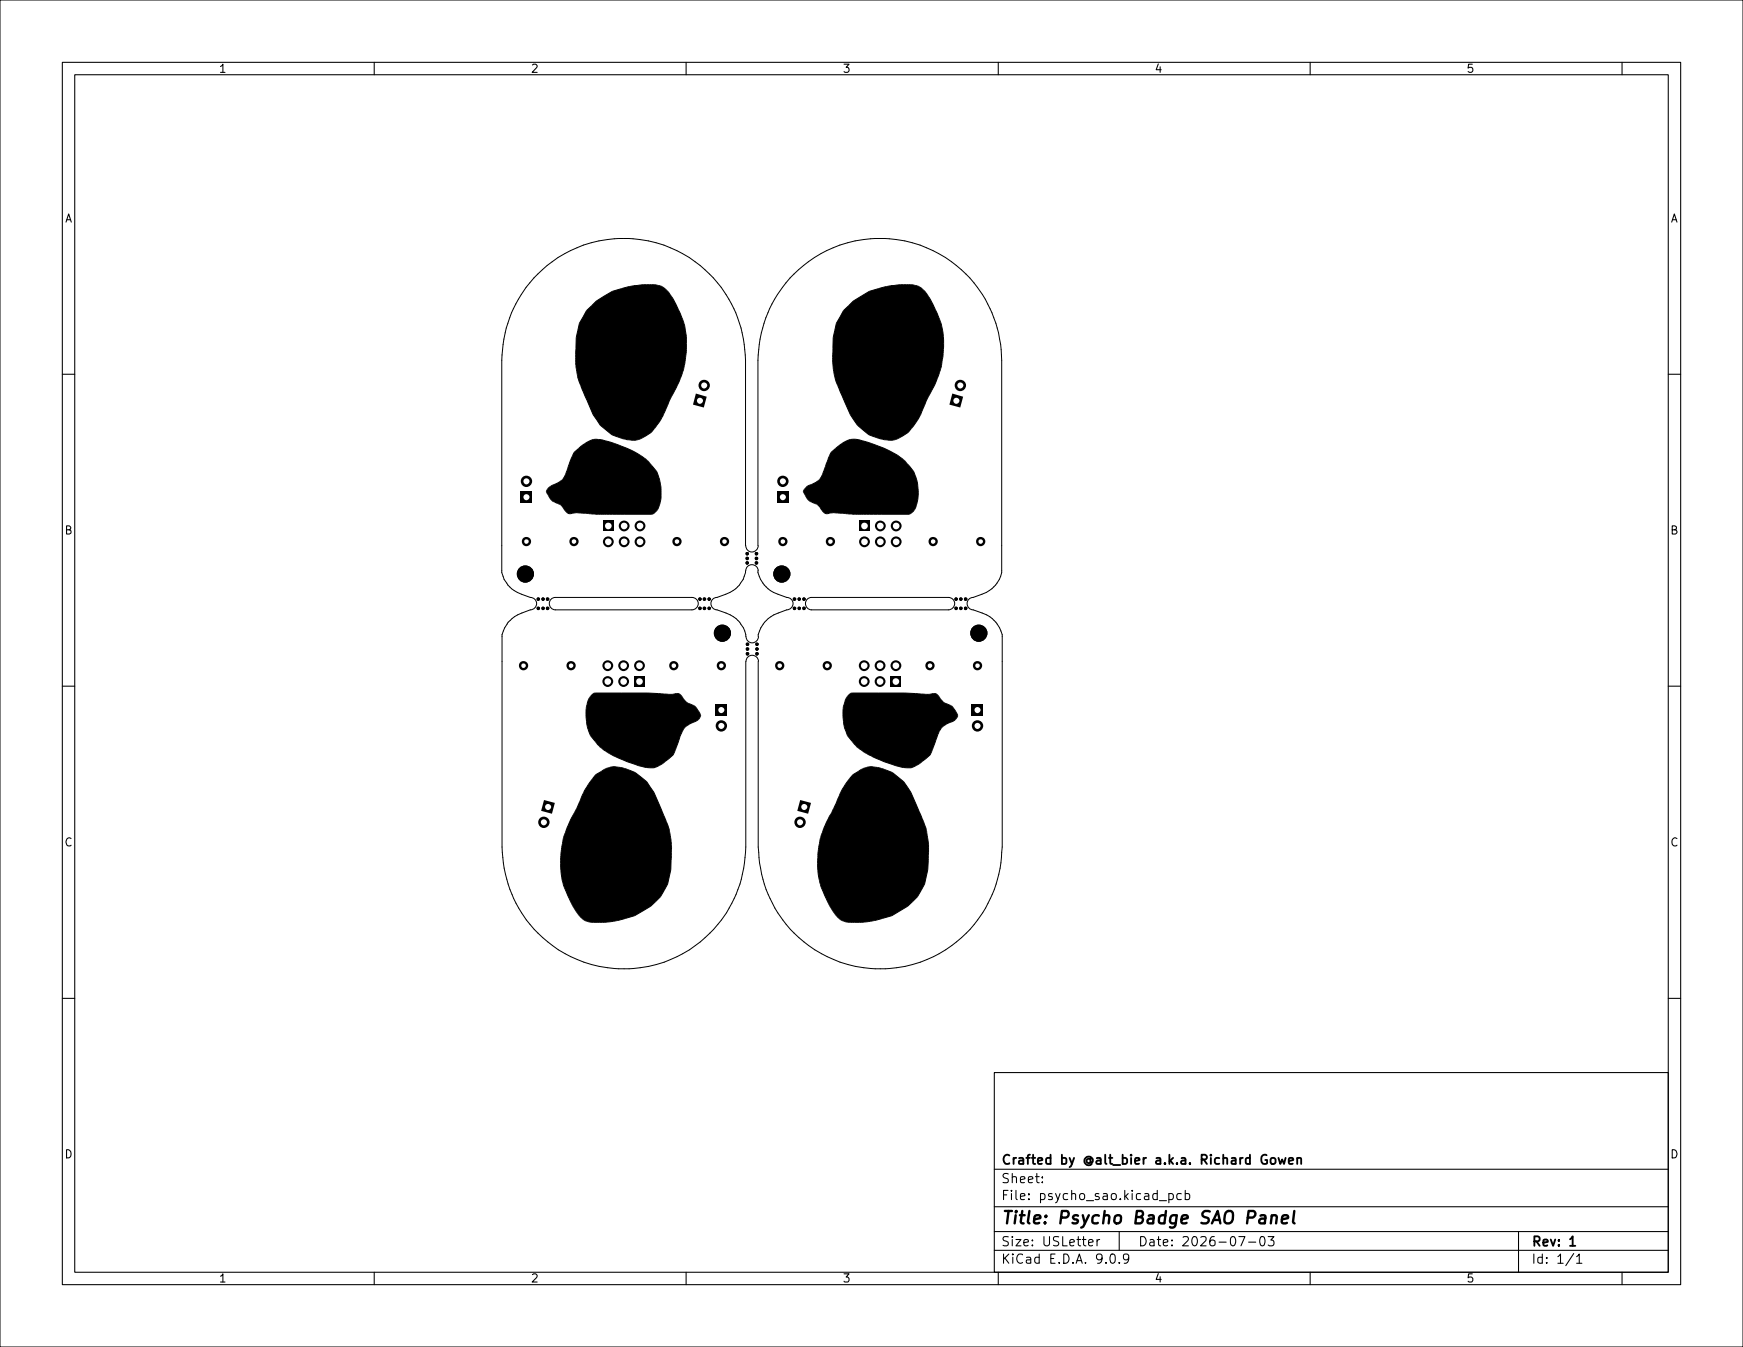
[picture p253: page 8]

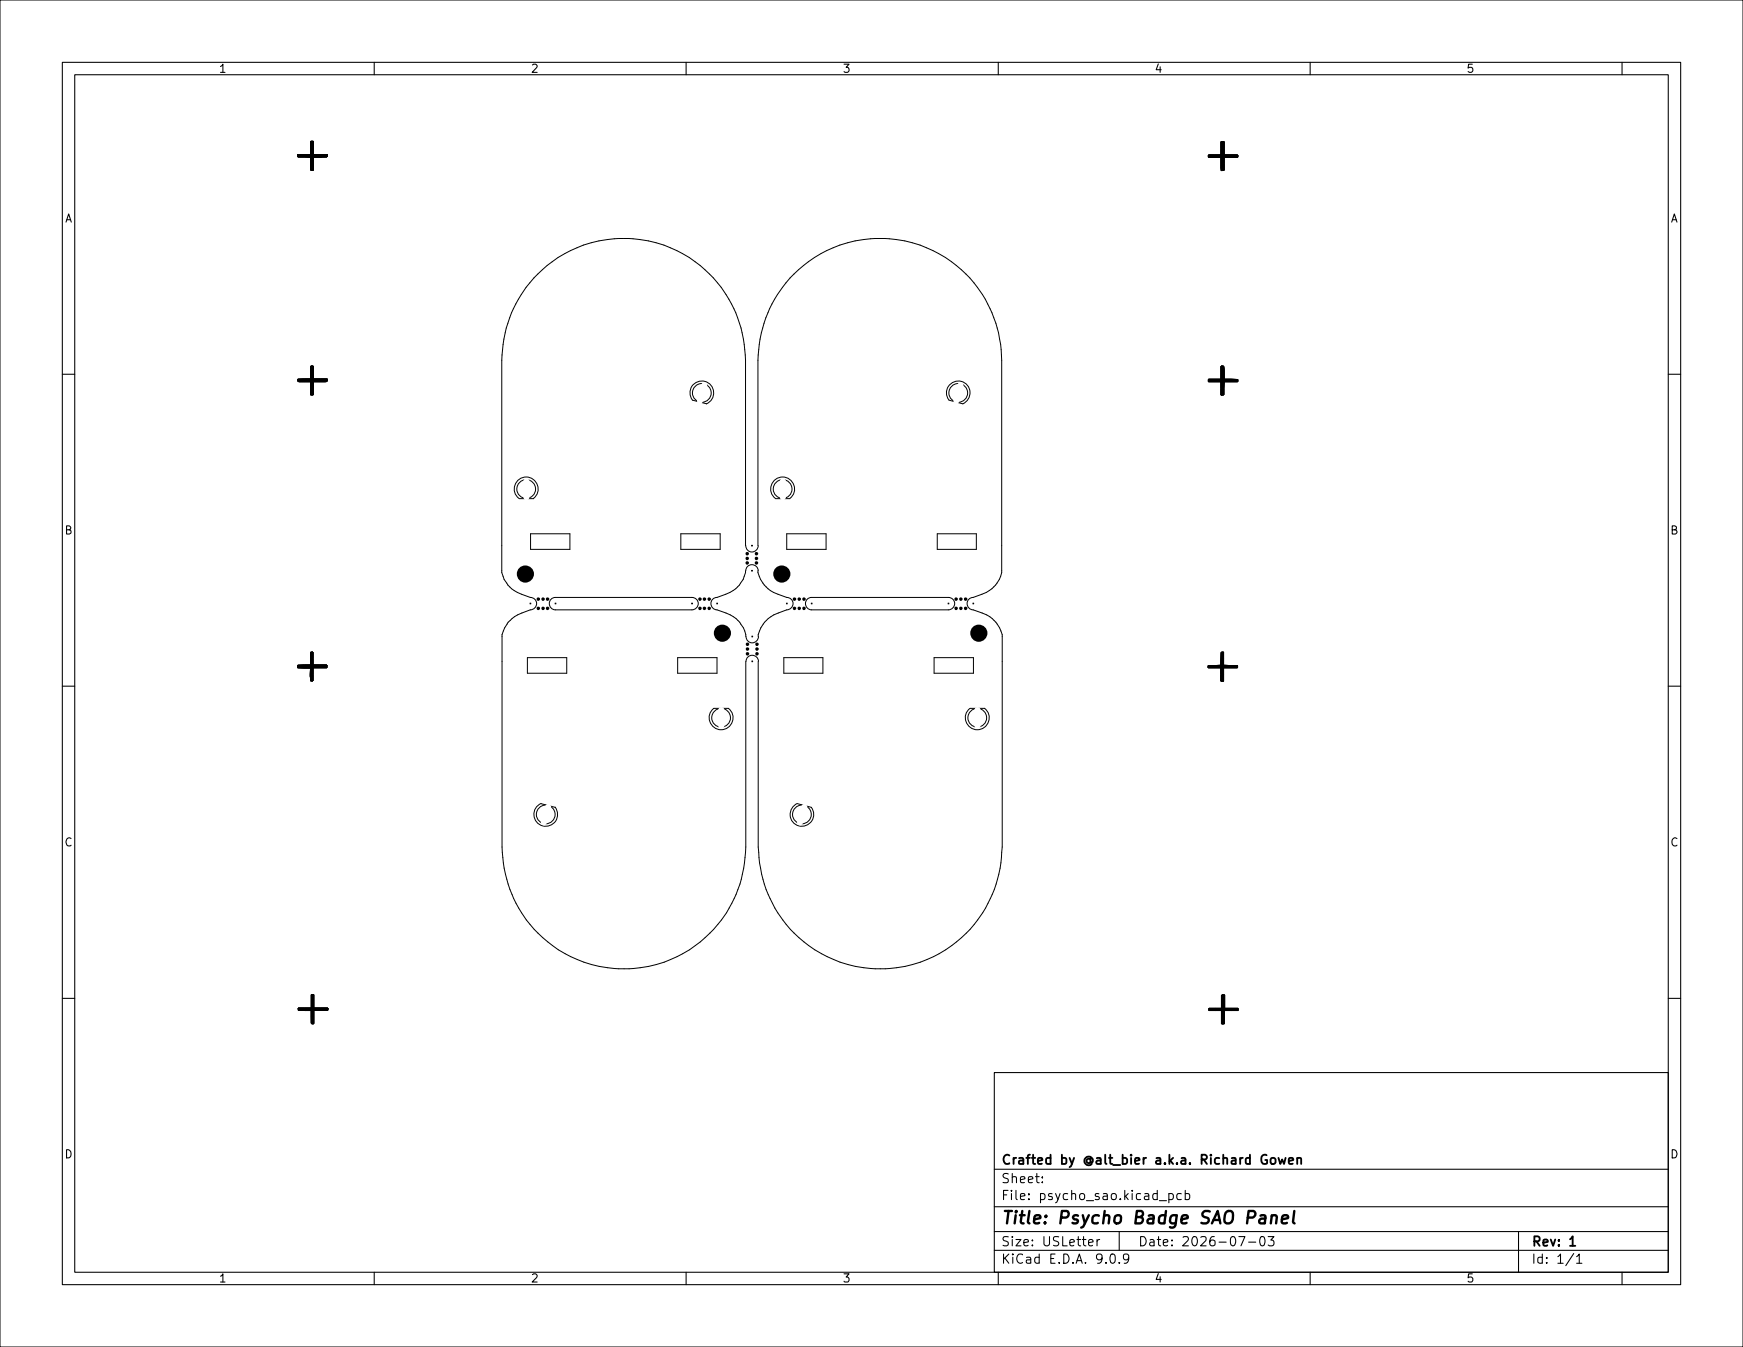
[picture p254: page 9]
